pozsarzs/zacchaeus/Zacchaeus computer/hardware/PBKP Back panel/README.md

# Zacchaeus Microcomputer

## Hardware/PBKP Back panel

### Directory content

|file |description |
|---|---|
|\[pbkp\]|KiCAD files |
|pbkp.pdf|schematic drawing|

### About module

This wiring diagram contains the connections of the fixed and removable
backplane connectors. It is occasionally updated due to newly connected
ones.

The connection of serial ports and modules may vary depending on the
application (for example: tape interface).
