pozsarzs/zacchaeus/Zacchaeus computer/hardware/PFRP Front panel/README.md

# Zacchaeus Microcomputer

## Hardware/PFRP Front panel

### Directory content

|file |description |
|---|---|
|\[pfrp\]|KiCAD files |
|pfrp.pdf|schematic drawing|

### About module

This wiring diagram contains the connections of the manuals and connectors
on front panel. The light from the LEDs mounted on the PCB is forwarded using
optical fibers. It is occasionally updated due to newly connected ones.
