pozsarzs/zacchaeus/Zacchaeus computer/hardware/SC702 RCBus backplane/SC702 description.pdf

S (https://smallcomputercentral.com/)mall Computer Central (https://smallcomputercentral.com/)

# SC702 – RCBus Backplane

SC702 is an RCBus modular backplane with 6 vertical bus sockets, 1 horizontal bus socket, and one horizontal bus plug.

A 12-slot version of this backplane is also available: SC710 (https://smallcomputercentral.com/sc710-rcbus-backplane/) (https://smallcomputercentral.com/sc710-rcbus-backplane/)

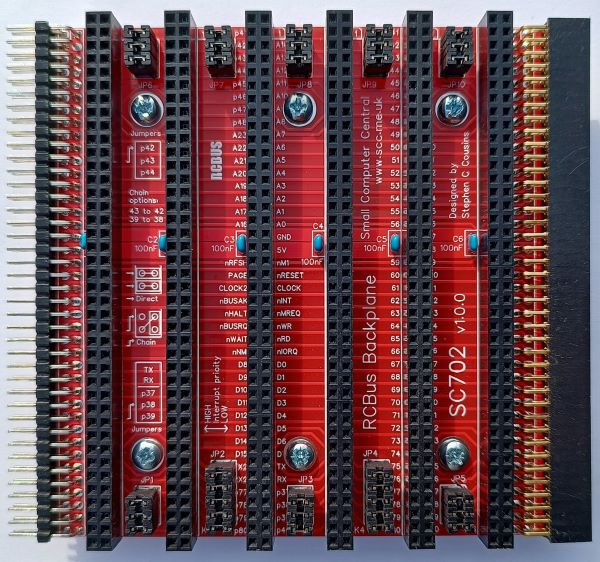
[picture p23: figure]

SC702 – Assembly guide
SC702 – Compatibility
SC702 – Parts list
SC702 – Printed circuit board SC702 – User guide

SC700 series information (https://smallcomputercentral.com/rcbus/sc700-series/) SC700 series support (https://smallcomputercentral.com/support/)

## Downloads

S (https://smallcomputercentral.com/wp-content/uploads/2024/01/sc702-kit-contents_v1.0.2_2024-01-13.pdf)C702, v1.0, Kit contents sheet (PDF) (https://smallcomputercentral.com/wp-content/uploads/2024/01/sc702-kit-contents_v1.0.2_2024-01-13.pdf) (https://smallcomputercentral.com/wpcontent/uploads/2024/01/sc702-kit-contents_v1.0.2_2024-01-13.pdf) (https://smallcomputercentral.com/wp-content/uploads/2024/01/sc702-kit-contents_v1.0.2_2024-01-13.pdf)
S (https://smallcomputercentral.com/wp-content/uploads/2023/04/sc702_v1.0.0_2023-03-21_00-14_schematic.pdf)C702, v1.0, Schematic (PDF) (https://smallcomputercentral.com/wp-content/uploads/2023/04/sc702_v1.0.0_2023-03-21_00-14_schematic.pdf) (https://smallcomputercentral.com/wpcontent/uploads/2023/04/sc702_v1.0.0_2023-03-21_00-14_schematic.pdf) (https://smallcomputercentral.com/wp-content/uploads/2023/04/sc702_v1.0.0_2023-03-21_00-14_schematic.pdf)
SC702, v1.0, PCB design files (OSHWLab) (https://oshwlab.com/sccousins/sc702-v1-0-backplane-6-1-for-rcbus) (https://oshwlab.com/sccousins/sc702-v1-0-backplane-6-1-for-rcbus)
SC702, v1.0, Gerber files (ZIP) (https://drive.google.com/file/d/1lC7prZ-vx8-ulZYEI05hR-YFU-A_hAfT/view?usp=share_link) (https://drive.google.com/file/d/1lC7prZ-vx8-ulZYEI05hR-YFU-A_hAfT/view?usp=share_link)
SC702, 3D printed mounting rails at thingiverse.com (https://www.thingiverse.com/thing:6334939/files)

## Warnings

Assembly: Ensure the bus sockets are pressed firmly against the PCB alone their entire length

## Errata

Nothing known

## Suppliers

Kits | Website | From | Currency
Small Computers Direct | SCDirect (https://small-computers-direct.square.site/s/search?q=sc702) (https://small-computers-direct.square.site/s/search?q=sc702) | UK | GBP
Stephen C Cousins | Tindie (https://www.tindie.com/search/?q=sc702) | UK | USD
Small Computer Central | Lectronz (https://lectronz.com/products/search?q=sc702) | UK | Euro/USD
PCBs | Website | From | Currency
Small Computers Direct | (https://small-computers-direct.square.site/s/search?q=sc733) (https://small-computers-direct.square.site/s/search?q=sc733)SCDirect (https://small-computers-direct.square.site/s/search?q=sc702) (https://small-computers-direct.square.site/s/search?q=sc702) (https://small-computers-direct.square.site/s/search?q=sc702) | UK | GBP
Stephen C Cousins | Tindie (https://www.tindie.com/products/tindiescx/picknmix-boards-for-rcbus-80pin/) (https://www.tindie.com/products/tindiescx/picknmix-boards-for-rcbus-80pin/) | UK | USD

Small
Computer
Central

Lectronz (https://lectronz.com/products/pick-n-mix-boards-for-rcbus-80pin) (https://lectronz.com/products/pick-n-mix-boards-for-rcbus-80pin)

UK | Euro/USD
Assembled and Tested | Website | From | Currency

Not available

Components
See parts list

Small Computers Direct does not collect VAT for EU countries Tindie does not collect VAT for EU countries Lectronz does collect EU VAT for orders up to 150 EUR

## Parts List

Reference | Qty | Component
PCB | 1 | SC702, v1.0, PCB
C1 to C6 | 6 | Capacitor, ceramic, 100 nF
JP1, 3 and 5 JP6 to JP10 | 8 | Header, male, 2 row x 3 pin, straight
JP2 and 4 | 2 | Header, male, 2 row x 5 pin, straight
Jumper | 34 | Jumper shunt
K1 to K6 | 6 | Header, female, 2 row x 40 pin, straight
P1 | 1 | Header, male, 2 row x 40 pin, angled
S1 | 1 | Header, female, 2 row x 40 pin, angled
Spacer | 6 | Spacer, 10mm, M3, nylon
Screw (for spacer) | 12 | Machine screw, 6mm, M3

Component details and sourcing (https://smallcomputercentral.com/components/)

## Printed Circuit Board

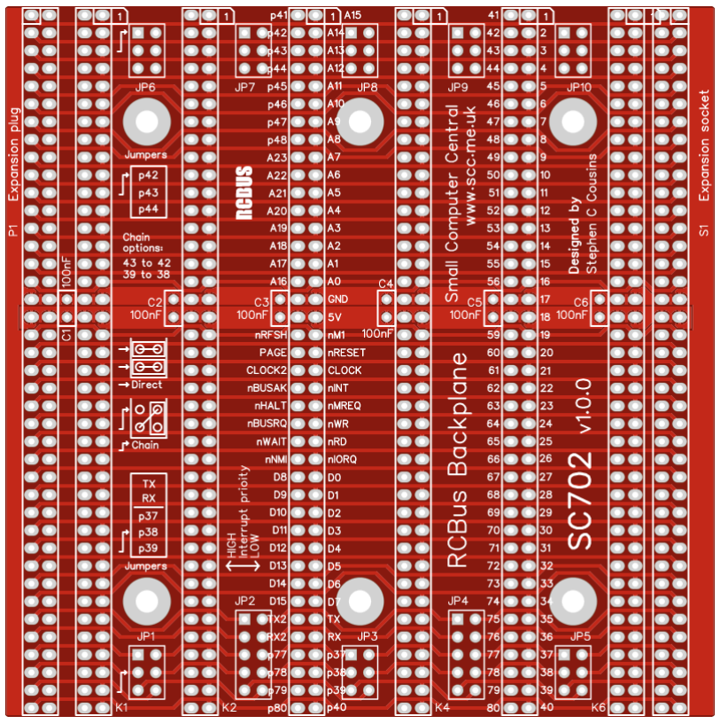
[picture p24: figure]

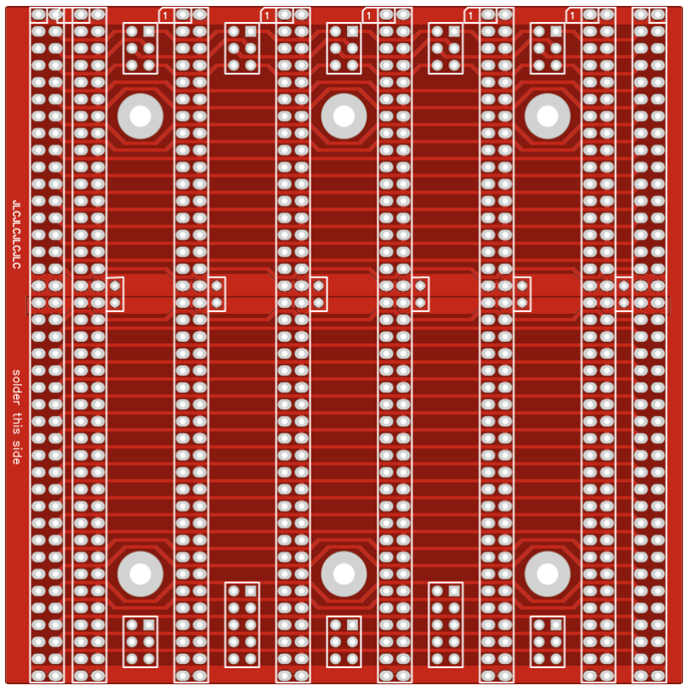
[picture p25: figure]

## User Guide

This backplane section can be used as an extension to other backplane sections or it can be used as the only backplane in the system.

Input/output port functions
I/O Address | Read | Write
none | n/a | n/a

Jumper options
Jumper Function

JP 1, 3, 5 | JPx.1 Connect P37 signal between bus sockets JPx.2 Connect P38 signal between bus sockets* JPx.3 Connect P39 signal between bus sockets* * See daisy chain details below
JP 2, 4 | JPx.1 Connect TX signal between bus sockets JPx.2 Connect RX signal between bus sockets JPx.3 Connect P37 signal between bus sockets JPx.4 Connect P38 signal between bus sockets* JPx.5 Connect P39 signal between bus sockets* * See daisy chain details below
JP6 to 10 | JPx.1 Connect P42 signal between bus sockets* JPx.2 Connect P43 signal between bus sockets* JPx.3 Connect P44 signal between bus sockets * See daisy chain details below

JP 1 to JP10 allow some signals to be isolated between bus sockets. This can be helpful if there are several mod‐ ules that use these signals for different functions.

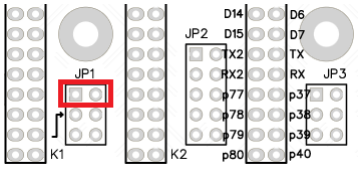
[picture p26: figure]

Typically the signals will be connected straight through to each bus socket by fitting jumper shunts horizontally, as illustrated to the left.

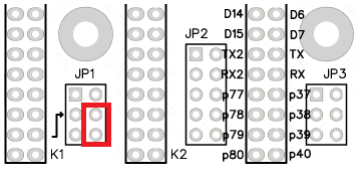
[picture p27: figure]

Alternatively, a daisy chain can be created from pin 39 to 38. This requires a jumper shunt to be fitted in the po‐ sition illustrated to the left. A second daisy chain can be created from pin 43 to 42.

A daisy chain is created with two pins on each module. One pin is an output signal while the other is an input signal. The jumper connects the output of one module to the input of the next. The illustration below shows the jumper positions required to create a daisy chain between four modules, in bus sockets K1 to K4.

Daisy chains are typically use to create a priority ‘chain’. In the case illustrated above the output is from pin 39 of one module and this is connected to the input pin 38 on the input of module to the right. This creates a prior‐ ity chain where the modules on the left are a higher priority than modules on the right.

Typical uses for a daisy chain are the Z80 mode 2 interrupt priority, IEI and IEO signals. This is specified as us‐ ing pins 39 and 38. The second chain, using pins 43 and 42 can be used for a DMA priority chain.

Priority chains require all bus slots in the chain to be occupied by suitable modules. A gap can be left by fitting a pair of jumper shunts horizontally to pass the input and output signals straight through to the bus socket not use the chain signals, rather than being crossed from output to input pins.

The illustration above configures the backplane for a daisy chain where bus socket K3 does not receive a crossed chain signal and thus should not contain a module which is part of the chain. Socket K3 can be empty or can contain a module which does not have connections to pins 39 or 38.

## Assembly Guide

Below is the suggested order of assembly. A general guide to assembling circuit boards can be found here (https://smallcomputercentral.com/assembly-guide/).

Decoupling capacitors C1 to C6
These can be fitted either way around
Header pins P1
Bus socket S1
Header pins JP1 to JP10
Bus sockets K1 to K6
Ensure the bus sockets are pressed firmly against the PCB along their entire length

## Compatibility

This backplane conforms fully to the RCBus specification v1.0 (https://smallcomputercentral.com/rcbus/) and thus supports: RCBus-2014, RCBus-Z80, RCBus-68xx, RCBus-9995.

The RCBus specification includes RCBus-2014 (both RC2014 standard 40-pin bus and RC2014 enhanced 60-pin bus) and also the full 80-pin RCBus. The 80-pin RCBus provides support for advanced Z80 features, such as the interrupt daisy-chain, as well as support for other processor families.

The following table indicates electrical compatibility with SC702. Check firmware and software details for any required software support.

Product (80-pin) | ? | Compatibility notes
SC126 (https://smallcomputercentral.com/sc126-z180-motherboard-rc2014/) Z180 motherboard | | Adds Z180 SBC/ motherboard
SC701 (https://smallcomputercentral.com/sc701-rcbus-backplane/) Backplane 6+1 | | Adds 6 module sockets RCBus 80-pin and PSU
SC702 (https://smallcomputercentral.com/sc702-rcbus-backplane/) Backplane 6+1 | | Adds 6 module sockets RCBus 80-pin
SC703 (https://smallcomputercentral.com/sc703-rcbus-power-supply-mod‐ule/) (https://smallcomputercentral.com/sc703-rcbus-power-supply-module/) Power from 12v | | Adds power supply (8 to 12 volt input) and reset
SC704 (https://smallcomputercentral.com/sc704-rcbus-i2c-bus-master/) I2C bus master | | Adds I2C bus master and I2C EEPROM
SC705 (https://smallcomputercentral.com/sc705-rcbus-serial-acia/) Serial ACIA | | Adds one serial port Typically set to 0x40
SC706 (https://smallcomputercentral.com/sc706-rcbus-z80-cpu-module/) Z80 CPU | | Adds Z80 CPU and main bus clock
SC707 (https://smallcomputercentral.com/sc707-rcbus-memory-module/) Memory 128k | | Adds 128k RAM and 128k flash ROM
SC708 (https://smallcomputercentral.com/sc708-rcbus-z80-sbc-module/) Z80 SBC | | Adds CPU, ROM, RAM clock and reset
SC709 (https://smallcomputercentral.com/sc709-rcbus-backplane/) Backplane 12+1 | | Adds 12 module sock‐ ets RCBus 80-pin and PSU
SC710 (https://smallcomputercentral.com/sc710-rcbus-backplane/) Backplane 12+1 | | Adds 12 module sock‐ ets RCBus 80-pin
SC711 (https://smallcomputercentral.com/sc711-rcbus-prototyping-module/) Prototyping | | Prototyping module
SC712 (https://smallcomputercentral.com/sc712-rcbus-power-supply-mod‐ule/) (https://smallcomputercentral.com/sc712-rcbus-power-supply-module/) Power from 5v | | Adds power supply (5 volt input) and reset
SC713 (https://smallcomputercentral.com/sc713-rcbus-tool/) RCBus tool | n/a | Simple reference tool No electrical function

SC714 (https://smallcomputercentral.com/sc714-rcbus-z80-memory-mod‐ule/) (https://smallcomputercentral.com/sc714-rcbus-z80-memory-module/) Memory 512k | Adds 512k RAM and 512k flash ROM
SC715 (https://smallcomputercentral.com/sc715-rcbus-compact-flash-mod‐ule/) (https://smallcomputercentral.com/sc715-rcbus-compact-flash-module/) Compact flash | Adds Compact Flash storage
SC716 (https://smallcomputercentral.com/sc716-rcbus-z80-sio-2-serial-mod‐ule/) (https://smallcomputercentral.com/sc716-rcbus-z80-sio-2-serial-module/) Z80 SIO/2 | Adds two serial ports Typically set to 0x84
SC717 (https://smallcomputercentral.com/sc717-rcbus-z80-pio-module/) Z80 PIO | Adds parallel I/O using Z80 PIO
SC718 (https://smallcomputercentral.com/sc718-rcbus-z80-ctc-module/) Z80 CTC | Adds counter/timer using Z80 CTC
SC719 (https://smallcomputercentral.com/sc719-rcbus-digital-i-o-module/) Digital I/O | Adds digital I/O Eight in, eight out
SC720 (https://smallcomputercentral.com/sc781-rcbus-z80-sbc-mother‐board/) (https://smallcomputercentral.com/sc781-rcbus-z80-sbc-motherboard/) Z80 motherboard | Adds Z80 SBC/ motherboard
SC721 (https://smallcomputercentral.com/sc721-rcbus-memory-module/) Memory 512k | Adds 512k RAM and 2 x 512k flash ROM
SC722 (https://smallcomputercentral.com/sc722-rcbus-z180-cpu-module/) Z180 CPU | Adds Z180 CPU with two serial ports
SC723 (https://smallcomputercentral.com/sc723-rcbus-backplane-3/) Backplane 3 | No male header pins for expansion
SC724 (https://smallcomputercentral.com/sc724-rcbus-breakout-module/) Breakout | Prototyping breakout module
SC725 (https://smallcomputercentral.com/sc725-rcbus-serial-and-timer-module/) (https://smallcomputercentral.com/sc725-rcbus-serial-and-timer-module/) SIO+CTC | Adds two serial ports and 4 counter/timers
SC726 (https://smallcomputercentral.com/sc726-rcbus-clock-module/) Clock generator | Generates CLK and CLK2 bus signals
SC727 (https://smallcomputercentral.com/sc727-rcbus-rtc-module/) Real time clock | Adds real time clock for time and date
SC728 (https://smallcomputercentral.com/sc727-rcbus-module-riser/) Module riser | Simple module riser for RCBus 80-pin
SC791 (https://smallcomputercentral.com/sc791-rcbus-z80-romwbw-com‐puter/) (https://smallcomputercentral.com/sc791-rcbus-z80-romwbw-computer/) Z80 system | Modular Z80 system
SC792 (https://smallcomputercentral.com/sc792-modular-z180-computer/) Z180 system | Modular Z180 system
Product (40 pin) | ? | Compatibility notes

SC114 (https://smallcomputercentral.com/2019/02/27/sc114-motherboard-kit/) (https://smallcomputercentral.com/2019/02/27/sc114-motherboard-kit/) Z80 motherboard | Z80 SBC/motherboard
SC130 (https://smallcomputercentral.com/sc130-z180-motherboard/) Z180 motherboard | Z180 SBC/motherboard
SC133 (https://smallcomputercentral.com/sc133-modular-backplane-rc2014/) (https://smallcomputercentral.com/sc133-modular-backplane-rc2014/) Backplane 11+1 | Adds 11 module sock‐ ets RCBus 40-pin and PSU
SC134 (https://smallcomputercentral.com/sc134-led-output-module-rc2014/) LED output port | Adds eight LED outputs
SC135 (https://smallcomputercentral.com/sc135-digital-output-module-rc2014/) (https://smallcomputercentral.com/sc135-digital-output-module-rc2014/) Digital output port | Adds eight digital outputs
SC136 (https://smallcomputercentral.com/sc136-digital-input-module-rc2014/) (https://smallcomputercentral.com/sc136-digital-input-module-rc2014/) Digital input port | Adds eight digital inputs
SC137 (https://smallcomputercentral.com/sc137-i2c-master-module-rc2014/) I2C bus master | Adds I2C bus master
SC139 (https://smallcomputercentral.com/sc139-serial-68b50-module-rc2014/) (https://smallcomputercentral.com/sc139-serial-68b50-module-rc2014/) Serial ACIA | Adds one serial port Typically set to 0x40
SC141 (https://smallcomputercentral.com/sc141-modular-backplane-rc2014/) (https://smallcomputercentral.com/sc141-modular-backplane-rc2014/) Backplane 12+1 | Adds 12 module sock‐ ets RCBus 40-pin
SC142 (https://smallcomputercentral.com/sc142-power-module-rc2014/) Power from 12v | Adds power supply (8 to 12 volt input) and reset
SC143 (https://smallcomputercentral.com/sc143-rom-module-rc2014/) Flash ROM | Adds 128k flash ROM
SC145 (https://smallcomputercentral.com/sc145-compact-flash-rc2014/) Compact flash | Adds Compact Flash storage
SC147 (https://smallcomputercentral.com/sc147-modular-backplane-rc2014/) (https://smallcomputercentral.com/sc147-modular-backplane-rc2014/) Backplane 6+1 | Adds 6 module sockets RCBus 40-pin
SC148 (https://smallcomputercentral.com/sc148-power-module-rc2014/) Power from 5v | Adds power supply (5 volt input) and reset
SC149 (https://smallcomputercentral.com/sc149-z80-cpu-module-rc2014/) Z80 CPU | Adds Z80 CPU and main bus clock
SC150 (https://smallcomputercentral.com/sc150-paged-ram-module-rc2014/) (https://smallcomputercentral.com/sc150-paged-ram-module-rc2014/) Paged RAM 128k | Adds 128k of paged RAM

SC151 (https://smallcomputercentral.com/sc151-paged-rom-modulerc2014/) (https://smallcomputercentral.com/sc151-paged-rom-module-rc2014/)
Paged ROM 128k

Adds 128k of paged
ROM
Other suppliers | ? | Compatibility notes
RC2014 Mini system | | No male header pins for expansion
RC2014 Pro system | | No male header pins for expansion
RC2014 Zed system | | No male header pins for expansion
RC2014 Micro module | | Adds CPU, ROM, RAM serial, clock and reset
RC2014 Backplane 5 | | If header pins fitted it adds 4 x 40-pin sockets
RC2014 Backplane 8 | | No male header pins for expansion
RC2014 Backplane Pro | | No male header pins for expansion
RC2014 Z80 CPU | | Adds Z80 CPU
RC2014 SIO/2 dual serial | | Adds two serial ports at 0x80 to 0x87
RC2014 Compact flash | | Adds Compact Flash at 0x10 to 0x17
RC2014 Dual clock | | Generates CLK and CLK2 bus signals
RC2014 Pageable ROM | | Adds 64k paged ROM
RC2014 64k RAM | | Adds 64k paged RAM
RC2014 Memory 512k | | Adds 512k RAM and 512k flash ROM
RC2014 Digital I/O | | Adds eight LED out‐ puts and eight push buttons
RC2014 Real time clock | | Adds real time clock for time and date
RC2014 RP2040 VGA terminal | | Connect VGA monitor and USB keyboard
RC2014 Pi Pico terminal | | Connect VGA monitor and USB keyboard

RC2014 YM2149 sound card | Adds authentic retro sound
Weird electronics Flock v2 | Adds floppy disk and real time clock

## Notes

This product is designed for hobby use and is not suitable for industrial, commercial, or safety-critical applications.
The product contains small parts and is not suitable for young children.
