pozsarzs/zacchaeus/Zacchaeus computer/hardware/SC702 RCBus backplane/SC702 kit contents.pdf

A | A
B | B

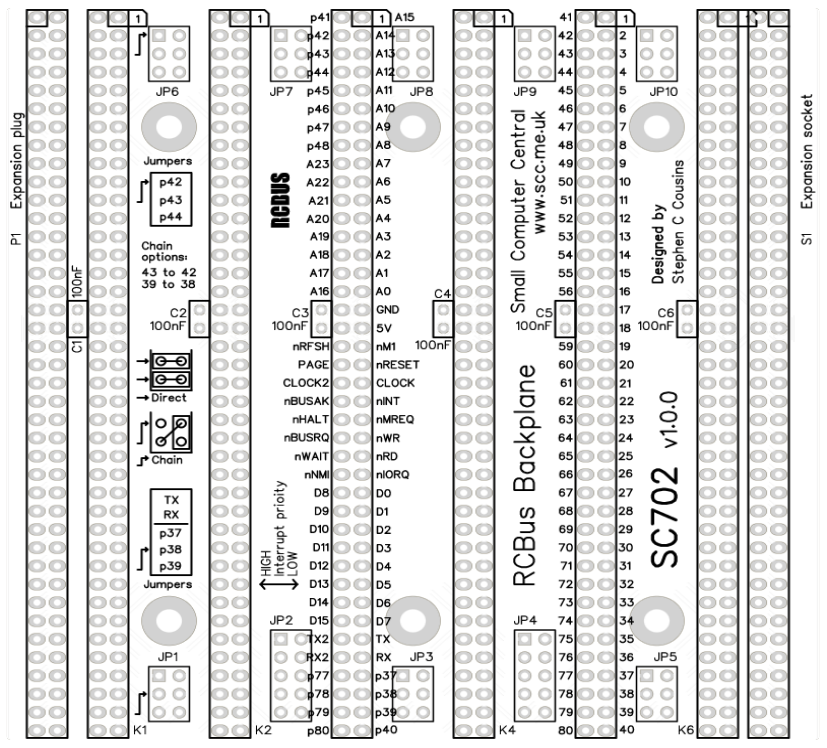
[picture p28: figure]

C | C
D | D

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
TITLE:

SC142 - Kit Contents

REV: 1.0.2

Date:

2021-01-11

Sheet: 1/1
Drawn By: sccousins

Company: www.scc.me.uk

C1 to C6
Capacitor 100 nF
6

Designed for
RCBus

# Welcome to your SC702, Backplane Kit

## Assembly instructions, user guide, and other documentation can be found at www.scc.me.uk (small computer central)

Contains small parts. Not suitable for young children. Designed for hobby use. Not suitable for commercial, industrial or safety-critical use.
1

SC702 v1.0.x
Printed circuit board

2024-01-13

SC702 - Kit Contents

Release date: 2023-04-05

6

K1 to K6 Female
2 row x 40 pin straight
1

JP1 to JP10 Header
2 row x 40 pin straight

Jumper shunt
34

See note 1

1

S1 Header socket
2 row x 40 pin angled

Spacer
Nylon, 10mm, M3
6

Screw (for spacer)
M3, 6mm, pan head
12

1

P1 Header plug
2 row x 40 pin angled

the PCB alone their entire length

(long nose wire cutters work well)

Notes:
1/ Cut into short length strips, 3 and 5 pins long, for J1 to JP10

2/ Ensure the module sockets (K1 to K6) are pressed firmly against

Label includes "104" | See note 2
