pozsarzs/zacchaeus/Zacchaeus computer/hardware/SC716 RCBus SIO-2 module/SC716 kit contents.pdf

A | A

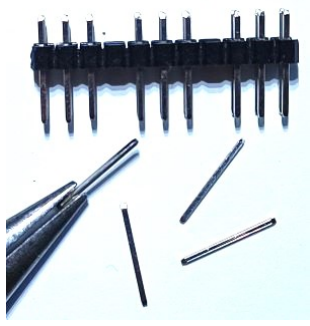
[picture p32: figure]

B | B

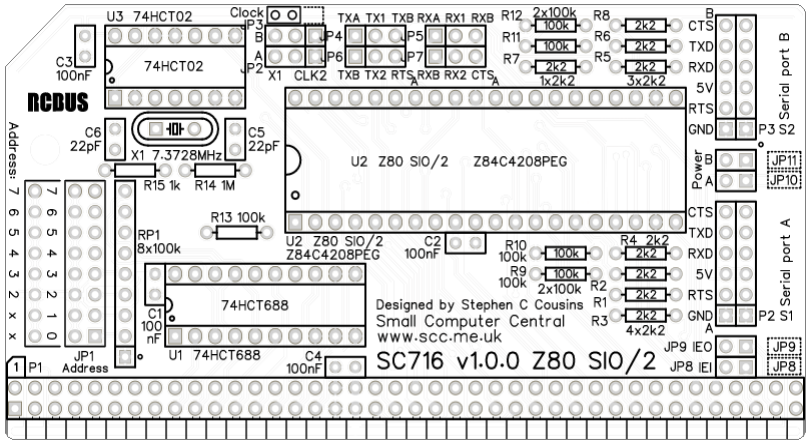
[picture p33: figure]

C | C
D | D

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
TITLE:

SC142 - Kit Contents

REV: 1.0.0

Date:

2021-01-11

Sheet: 1/1
Drawn By: sccousins

Company: www.scc.me.uk

C1 to C4
100 nF
4

Designed for
RCBus

# Welcome to your SC716, Z80 SIO/2 Serial Module Kit

## Assembly instructions, user guide, and other documentation can be found at www.scc.me.uk (small computer central)

Contains small parts. Not suitable for young children. Designed for hobby use. Not suitable for commercial, industrial or safety-critical use.
1

SC716 v1.0.x
Printed circuit board

2023-05-14

SC716 - Kit Contents

Release date: 2023-05-14

P1 Male
2 row x 40 pin angled
1

Spacer
Nylon, 10mm, M3

Screw (for spacer)
M3, 6mm, pan head
1 1

1

U3
74HCT02

1

JP1 Male
2 row x 8 pin angled

Jumper shunts
16

1

X1
7.3728 MHz crystal

2

C5 and C6
22 pF capacitor
Label includes "22" | See note 1 JP2 to JP7 Header 2 row x 11 pin straight
1

JP8 + JP9 Male
2 row x 2 pin angled
1

JP10 + JP11 Male
2 row x 2 pin angled
1

Cut with long nose wire cutters from a strip 2 row x 12+ pins

P2 Male
1 row x 6 pin angled
1

Cut from a strip 12+ pins long

P3 Male
1 row x 6 pin angled
1

1

5 1

R9 to R13
100K
8

R1 to R8
2K2

R14
1M

R15
1K

Label includes "104"

RP1 Resistor network
8 x 100K

# 1 2 S1 and S2 Female 1 row x 6 pin angled

1

1

U1
74HCT688

U1 socket
20-pin IC socket DIL
1

U1 Socket
40-pin IC socket DIL

1

U2 Z80 SIO/2
Z84C42xxPEG

U3 socket
14-pin IC socket DIL
1

Notes
1/ Removed the 4th and

connector fits in JP2

(pull out with pliers)

8th pair of pins so the

to JP7 holes

Label includes "104"
