pozsarzs/zacchaeus/Zacchaeus computer/hardware/SC717 RCBus PIO module/SC717 kit contents.pdf

A | A
B | B

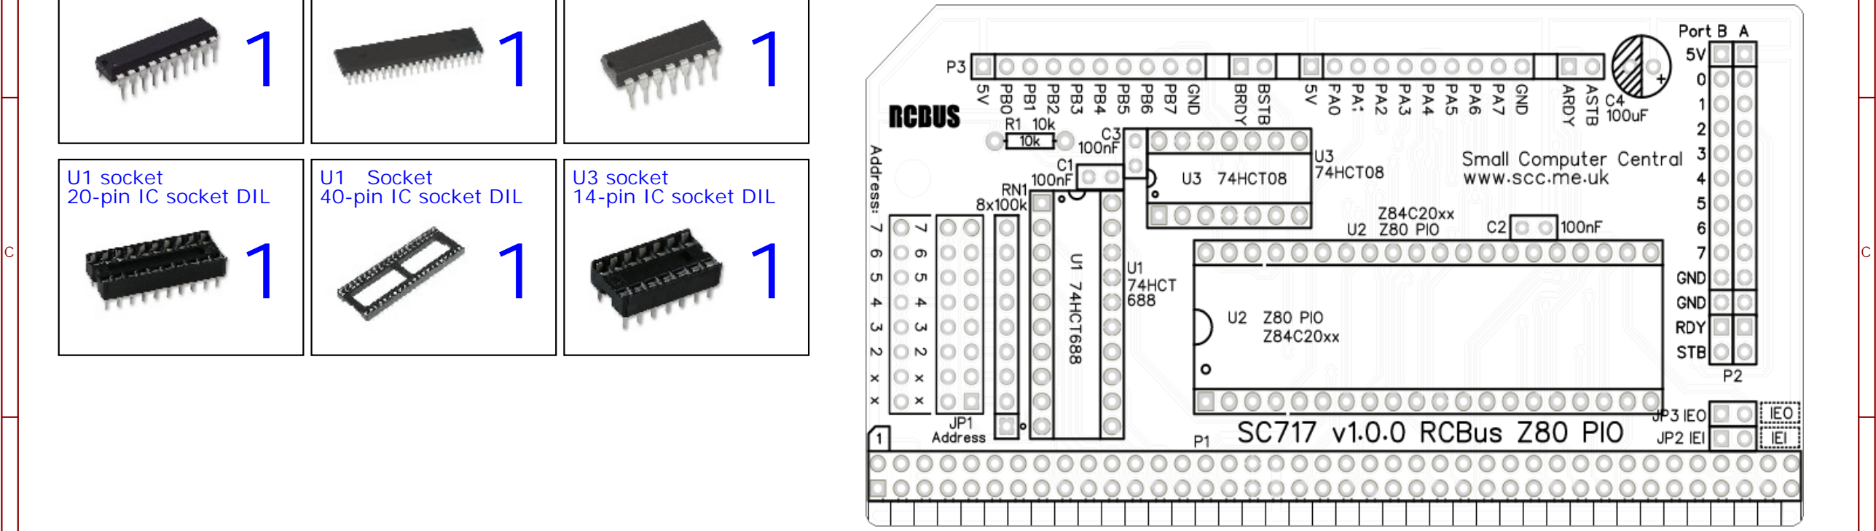
[picture p37: figure]
U1 socket 20-pin IC socket DIL; U1 Socket 40-pin IC socket DIL; U3 socket 14-pin IC socket DIL 1

D | D

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
TITLE:

SC142 - Kit Contents

REV: 1.0.0

Date:

2021-01-11

Sheet: 1/1
Drawn By: sccousins

Company: www.scc.me.uk

C1 to C3
100 nF
3

Designed for
RCBus

# Welcome to your SC717, Z80 PIO Digital Module Kit

## Assembly instructions, user guide, and other documentation can be found at www.scc.me.uk (small computer central)

Contains small parts. Not suitable for young children. Designed for hobby use. Not suitable for commercial, industrial or safety-critical use.
1

SC717 v1.0.x
Printed circuit board

2023-05-17

SC717 - Kit Contents

Release date: 2023-05-17

P1 Male
2 row x 40 pin angled
1

Spacer
Nylon, 10mm, M3

Screw (for spacer)
M3, 6mm, pan head
1 1

U3
74HCT08

1

JP1 Male
2 row x 8 pin angled

Jumper shunts
8

JP2 + JP3 Male
2 row x 2 pin angled
1

Cut from a strip 2 row x 10+ pins

P3 Male
1 row x 27 pin angled
1

Label includes "104"

RN1 Resistor network
8 x 100K
1

U1
74HCT688

U2 Z80 PIO
Z84C20xxPEG

Label includes "104"

1

C4
100 F

1

P2 Box header
2 row x 13 pin angled
1

R1
10k
