pozsarzs/zacchaeus/Zacchaeus computer/hardware/SC718 RCBus CTC module/SC718 kit contents.pdf

A | A
B | B

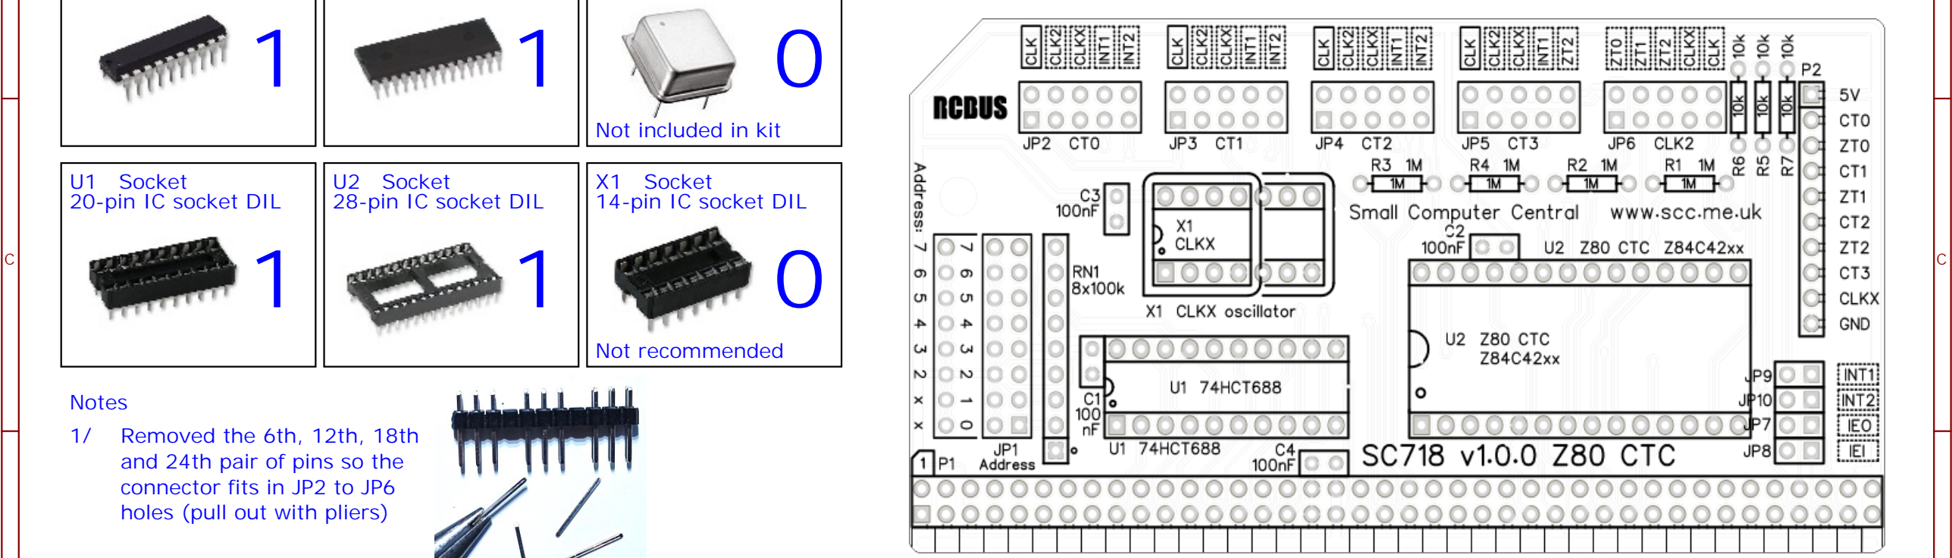
[picture p41: figure]
U1 Socket 20-pin IC socket DIL; U2 Socket 28-pin IC socket DIL; X1 Socket 14-pin IC socket DIL 0; Not included in kit; Not recommended; Notes 1/; holes (pull out with pliers); and 24th pair of pins so the connector fits in JP2 to JP6; Removed the 6th, 12th, 18th
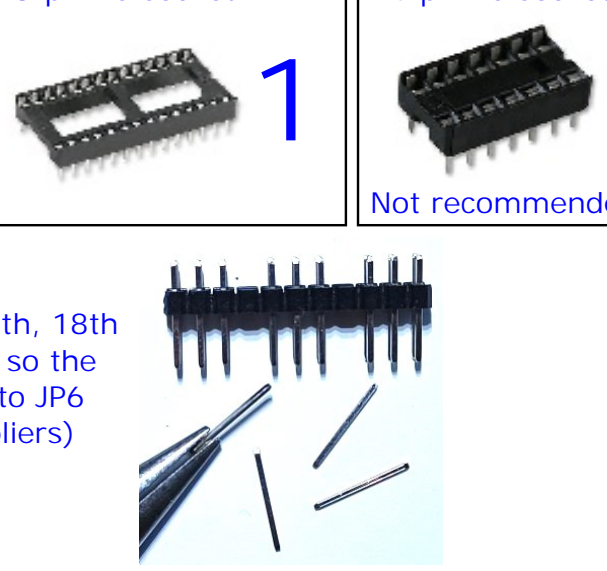
[picture p42: figure]

D | D

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
TITLE:

SC142 - Kit Contents

REV: 1.0.0

Date:

2021-01-11

Sheet: 1/1
Drawn By: sccousins

Company: www.scc.me.uk

C1 to C4
100 nF
4

Designed for
RCBus

# Welcome to your SC718, Z80 CTC Timer Module Kit

## Assembly instructions, user guide, and other documentation can be found at www.scc.me.uk (small computer central)

Contains small parts. Not suitable for young children. Designed for hobby use. Not suitable for commercial, industrial or safety-critical use.
1

SC718 v1.0.x
Printed circuit board

2023-05-21

SC718 - Kit Contents

Release date: 2023-05-21

P1 Male
2 row x 40 pin angled
1

Spacer
Nylon, 10mm, M3

Screw (for spacer)
M3, 6mm, pan head
1 1

1

JP1 Male
2 row x 8 pin angled

Jumper shunts
15

JP7+8+9+10 Male
2 row x 4 pin angled
1

Cut from a strip 2 row x 12+ pins

P2 Male
1 row x 10 pin angled
1

Label includes "104"

RN1 Resistor network
8 x 100K
1

U1
74HCT688

U2 Z80 CTC
Z84C30xxPEG

Label includes "104"
3

R5 to R7
10k

1

JP2 to JP6 Header
2 row x 29 pin straight

See note 1

R1 to R4
1M
4

X1 (optional)
7.3728MHz oscillator

Errata: PCB v1.0.0 has the wrong component label for U2
