pozsarzs/zacchaeus/Zacchaeus computer/hardware/SC719 RCBus DIO module/SC719 kit contents.pdf

A | A
B | B

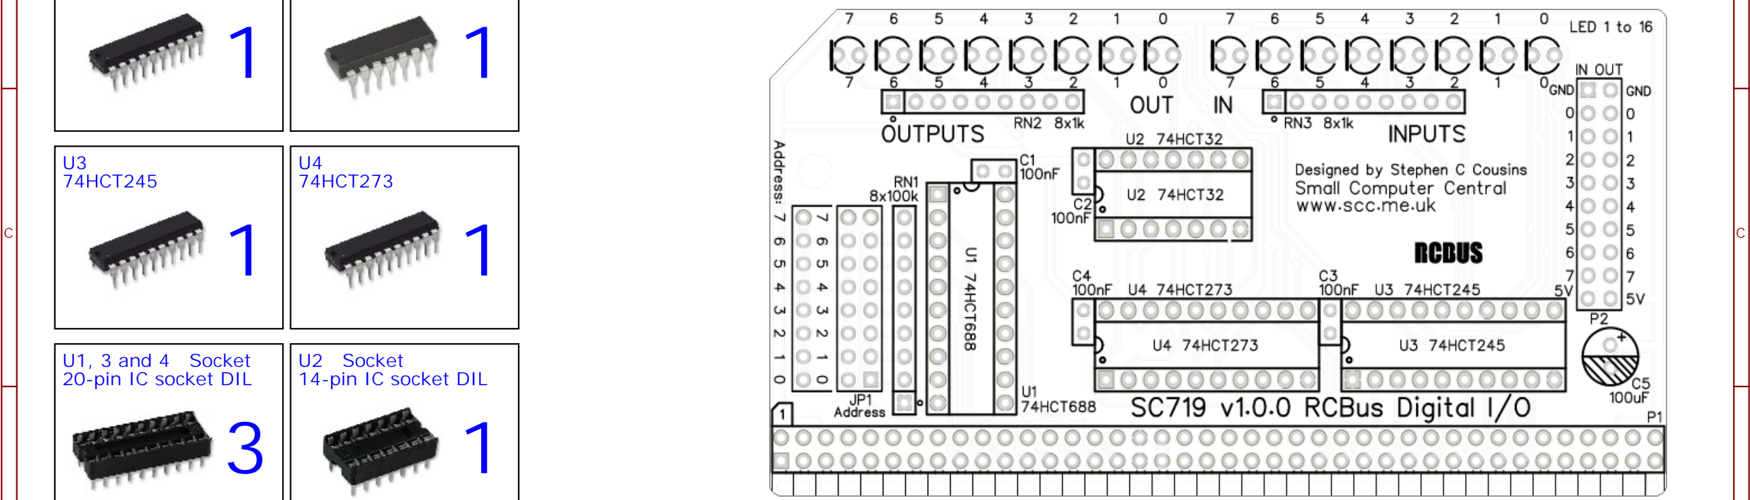
[picture p46: figure]
U1, 3 and 4 Socket 20-pin IC socket DIL; U2 Socket 14-pin IC socket DIL; U3 74HCT245; U4 74HCT273

D | D

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
TITLE:

SC142 - Kit Contents

REV: 1.0.1

Date:

2021-01-11

Sheet: 1/1
Drawn By: sccousins

Company: www.scc.me.uk

C1 to C4
100 nF
4

Designed for
RCBus

# Welcome to your SC719, Digital I/O Module Kit

## Assembly instructions, user guide, and other documentation can be found at www.scc.me.uk (small computer central)

Contains small parts. Not suitable for young children. Designed for hobby use. Not suitable for commercial, industrial or safety-critical use.
1

SC719 v1.0.x
Printed circuit board

2023-08-28

SC719 - Kit Contents

Release date: 2023-05-21

P1 Male
2 row x 40 pin angled
1

Spacer
Nylon, 10mm, M3

Screw (for spacer)
M3, 6mm, pan head
1 1

1

JP1 Male
2 row x 8 pin angled

Jumper shunts
8

Label includes "102"

RN2 and 3 Resistor
network 8 x 1K
2

U1
74HCT688

Label includes "104"

C5
100 F
1 | 8

LED9 to LED16
| Red LED 3mm angled

LED1 to LED8
Green LED 3mm angled
8

P2 Box header
2 row x 10 pin angled

# 1 1 RN1 Resistor network

8 x 100K

Label includes "104"

U2
74HCT32
