pozsarzs/zacchaeus/Zacchaeus computer/hardware/Front panel/README.md

# Zacchaeus Microcomputer

## Hardware/Front panel

### Directory content

|file |description |
|---|---|
|z180cpu.cdr |label 'Z180 CPU' |
|zacchaeus.cdr |label 'ZACCHAEUS' |
|zacchaeus_z180.dxf  |front panel design in DXF|
|zacchaeus_z180.jpg  |front panel appearance |
|zacchaeus_z180.panel|front panel design |

This folder contains the design of the front panel of the device. The front
panel was made in excellent quality by the Slovak company
[Quickpanel](https://quickpanel.sk). The design was made with their own
downloadable [design program](https://quickpanel.sk/en/download-quickpanel-program-software).
