pozsarzs/zacchaeus/PEIX External interface box/hardware/aim62-1/aim62-1.jpg

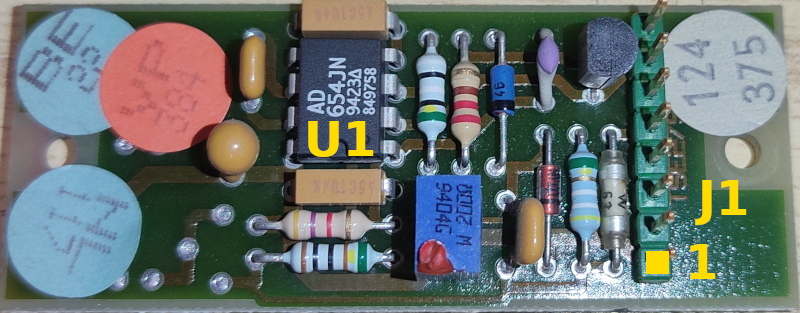
PEIX External interface box/hardware/aim62-1/aim62-1.jpg
