pozsarzs/zacchaeus/PEMX External memory box/hardware/block diagram/blk_pemx.png

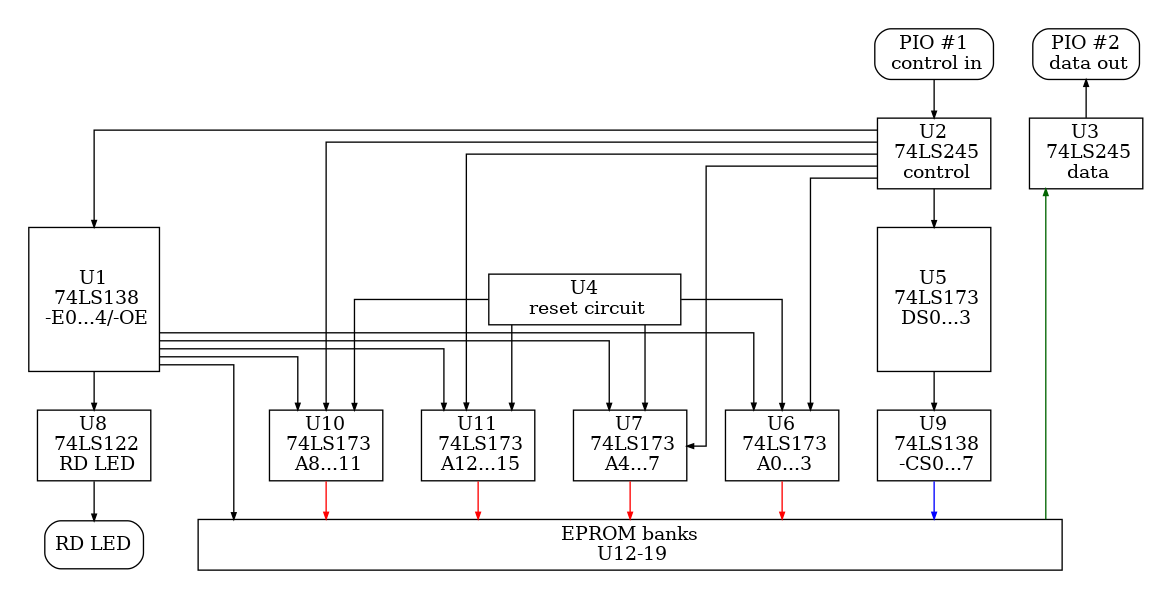
PEMX External memory box/hardware/block diagram/blk_pemx.png
