pozsarzs/zacchaeus/pictures/screenshot/scr_01.png

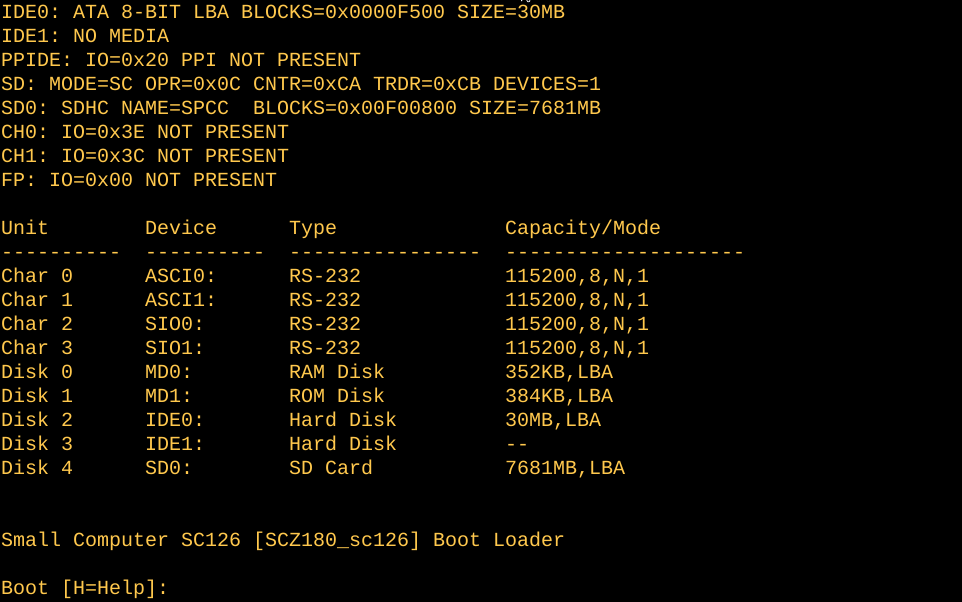
pictures/screenshot/scr_01.png
