pozsarzs/zacchaeus/pictures/screenshot/scr_02.png

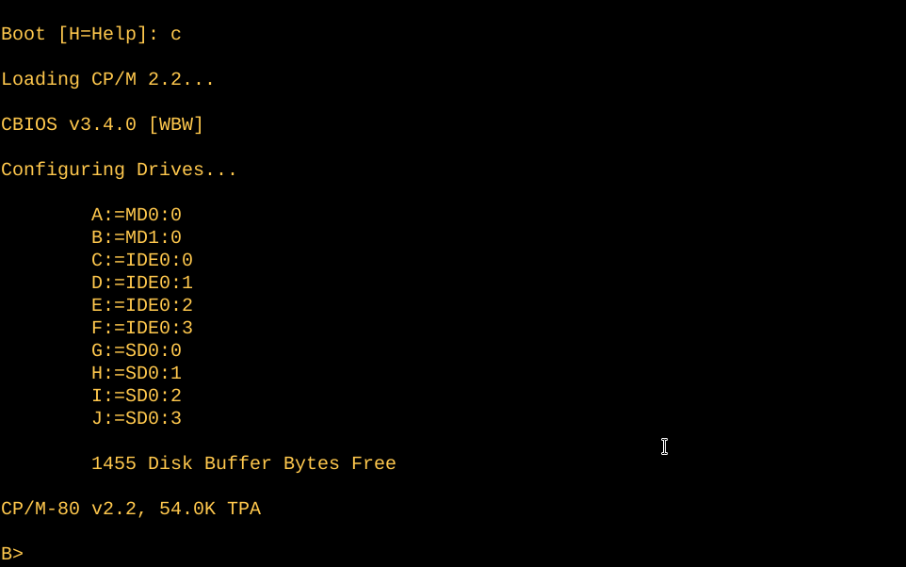
pictures/screenshot/scr_02.png
