pozsarzs/zacchaeus/pictures/screenshot/scr_03.png

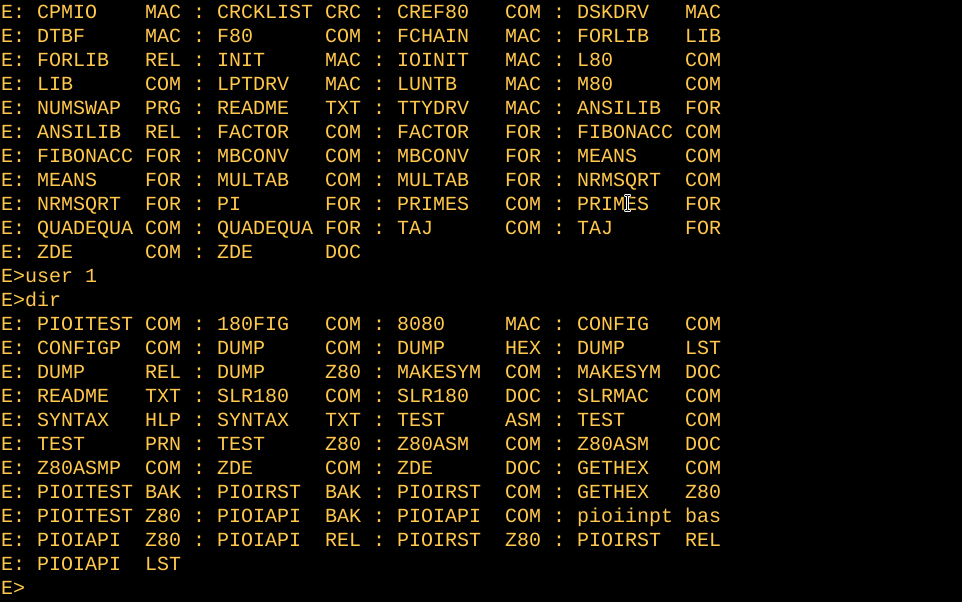
pictures/screenshot/scr_03.png
