pozsarzs/zacchaeus/pictures/screenshot/scr_04.png

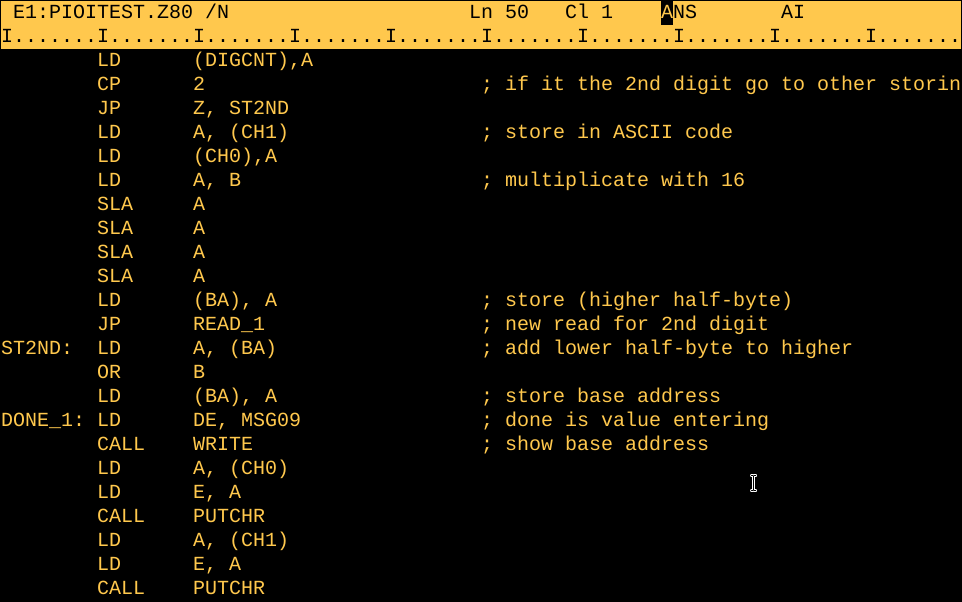
pictures/screenshot/scr_04.png
