pozsarzs/zacchaeus/pictures/screenshot/scr_05.png

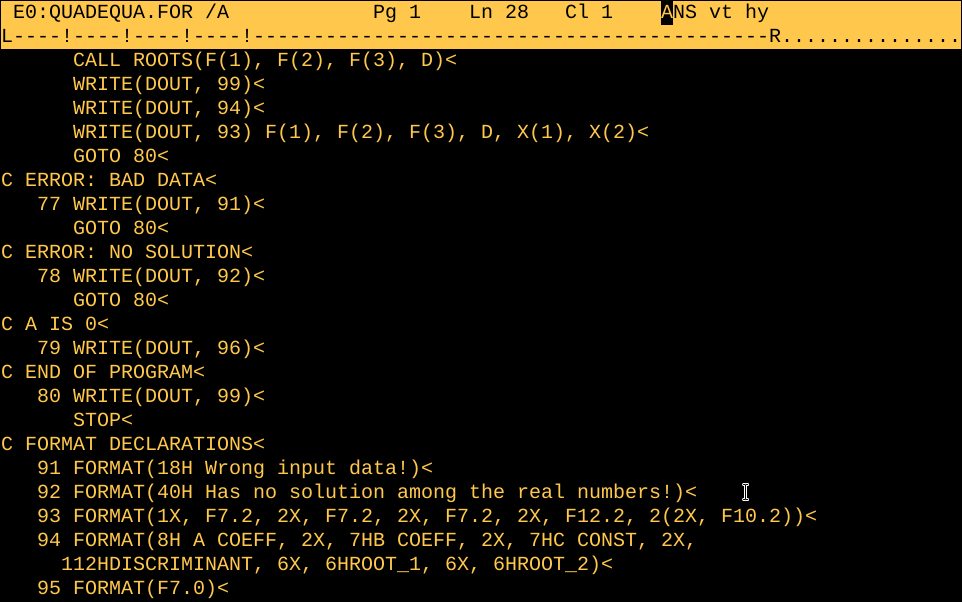
pictures/screenshot/scr_05.png
