pozsarzs/zacchaeus/pictures/Zacchaeus_01.jpg

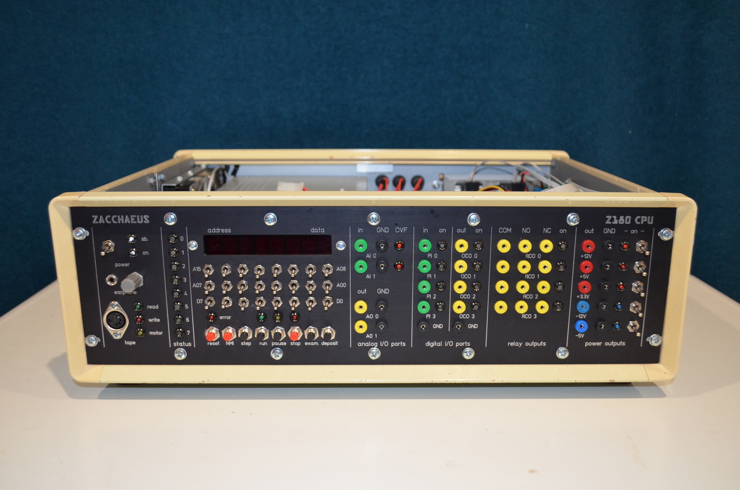
pictures/Zacchaeus_01.jpg
