pozsarzs/zacchaeus/pictures/Zacchaeus_02.jpg

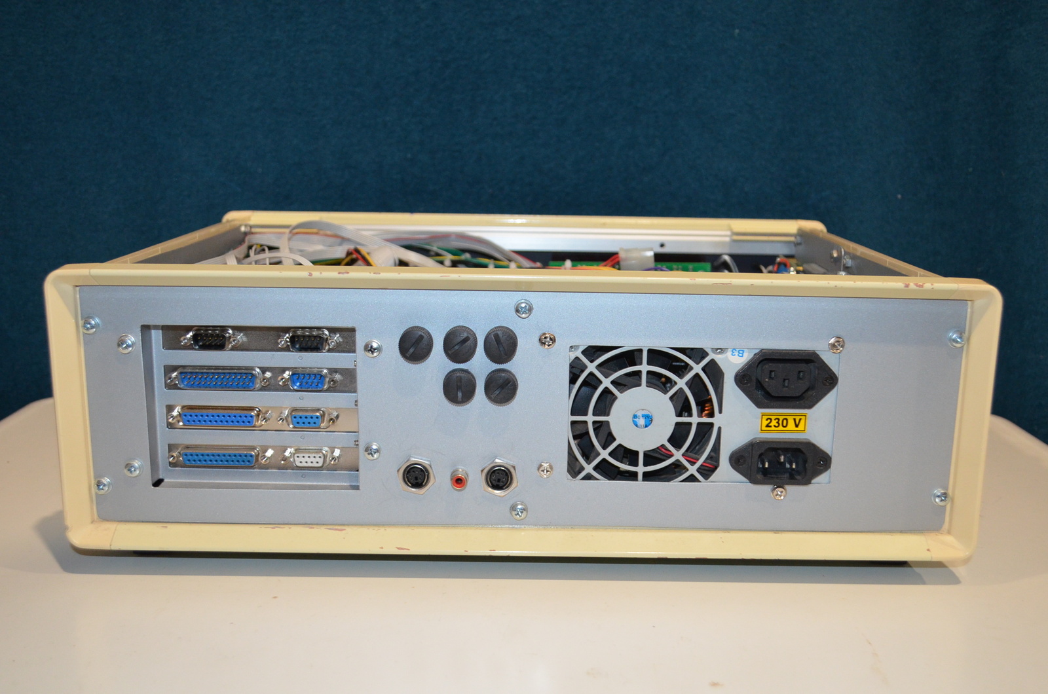
pictures/Zacchaeus_02.jpg
