pozsarzs/zacchaeus/Zacchaeus computer/hardware/Front panel/zacchaeus_z180.jpg

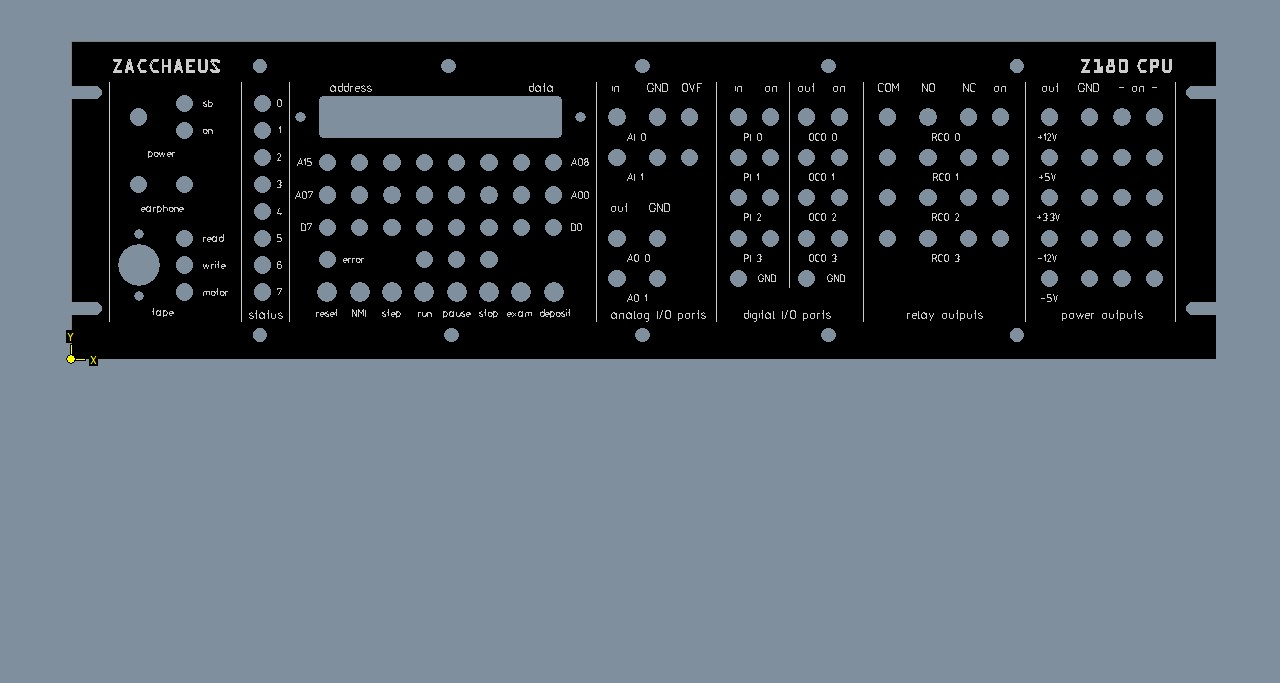
Zacchaeus computer/hardware/Front panel/zacchaeus_z180.jpg
