pozsarzs/zacchaeus/Zacchaeus computer/hardware/PMAN-IF Interface module/pman-if.jpg

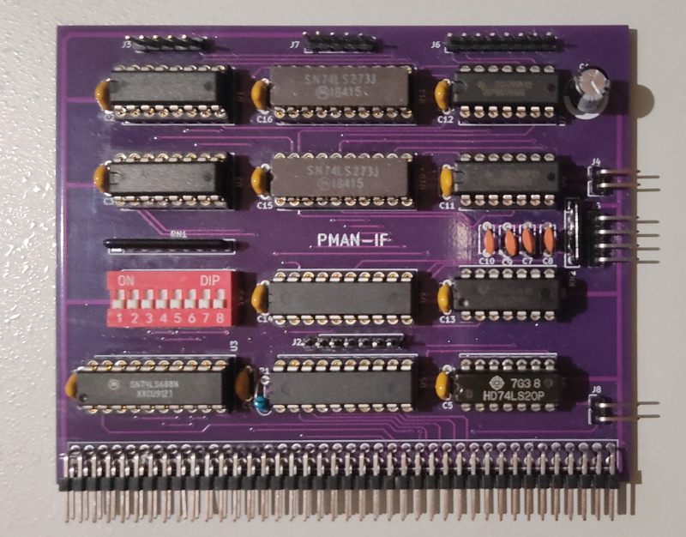
Zacchaeus computer/hardware/PMAN-IF Interface module/pman-if.jpg
