pozsarzs/zacchaeus/Zacchaeus computer/hardware/SC126 Z180 motherboard/SC126.jpg

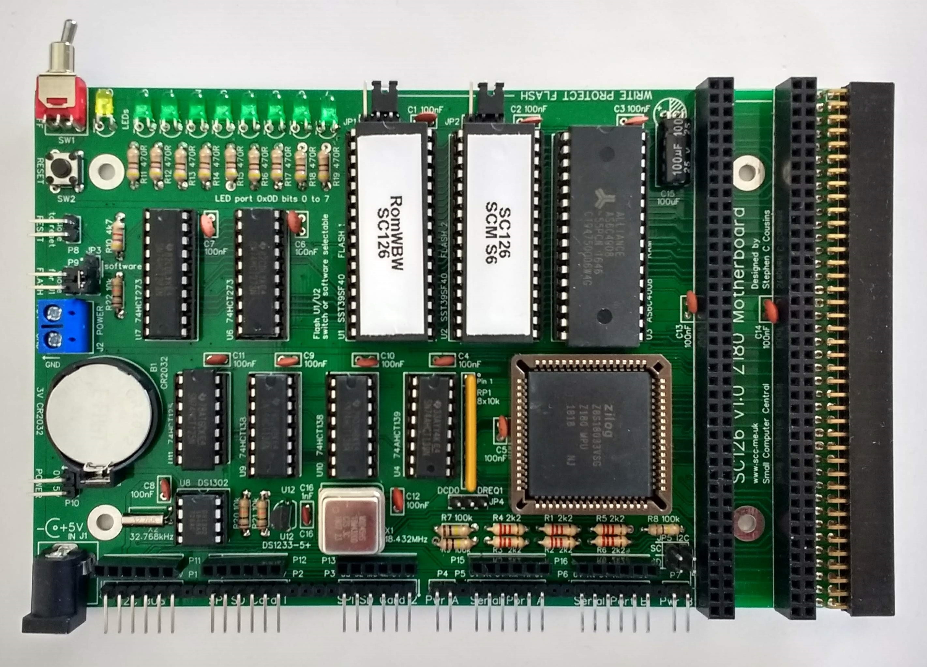
Zacchaeus computer/hardware/SC126 Z180 motherboard/SC126.jpg
