pozsarzs/zacchaeus/Zacchaeus computer/hardware/SC716 RCBus SIO-2 module/sc716.jpg

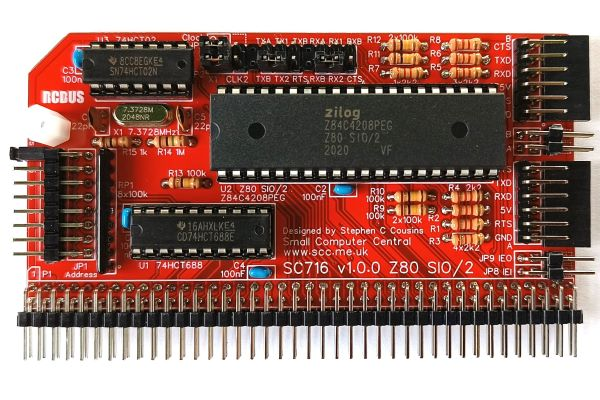
Zacchaeus computer/hardware/SC716 RCBus SIO-2 module/sc716.jpg
