pozsarzs/zacchaeus/Zacchaeus computer/hardware/MCS-51M RS232 level shifter module/MCS-51M assembled.jpg

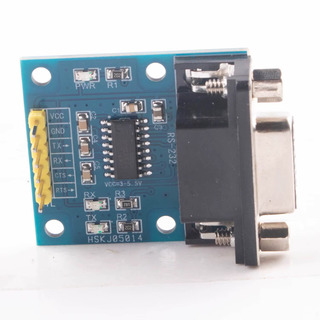
Zacchaeus computer/hardware/MCS-51M RS232 level shifter module/MCS-51M assembled.jpg
