pozsarzs/zacchaeus/Zacchaeus computer/hardware/RCBus/protocard-1.pdf

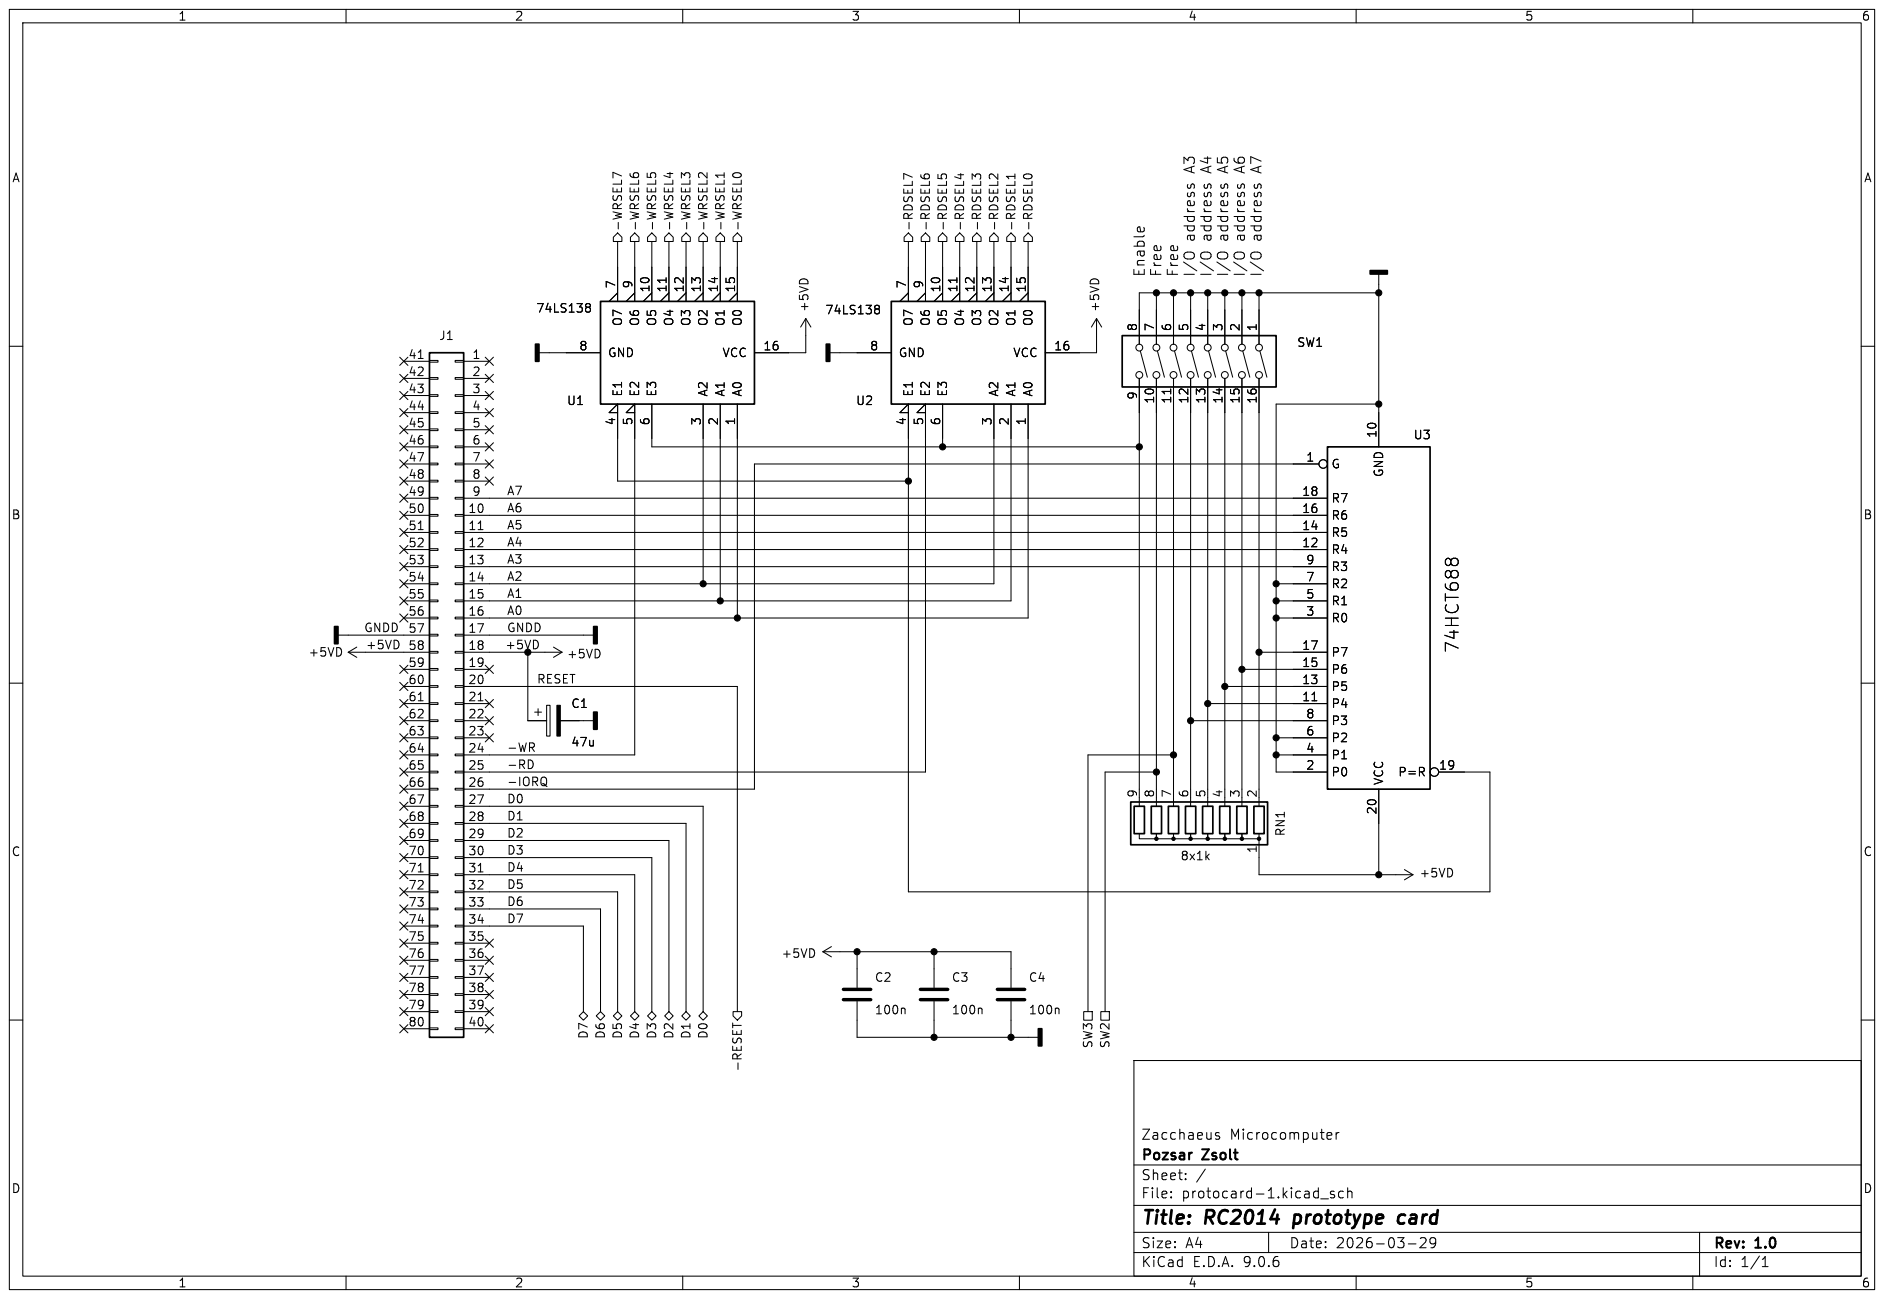
[picture p70: page 1]

Id: 1/1 Title: RC2014 prototype card
