pozsarzs/zacchaeus/Zacchaeus computer/hardware/RCBus/protocard-2.pdf

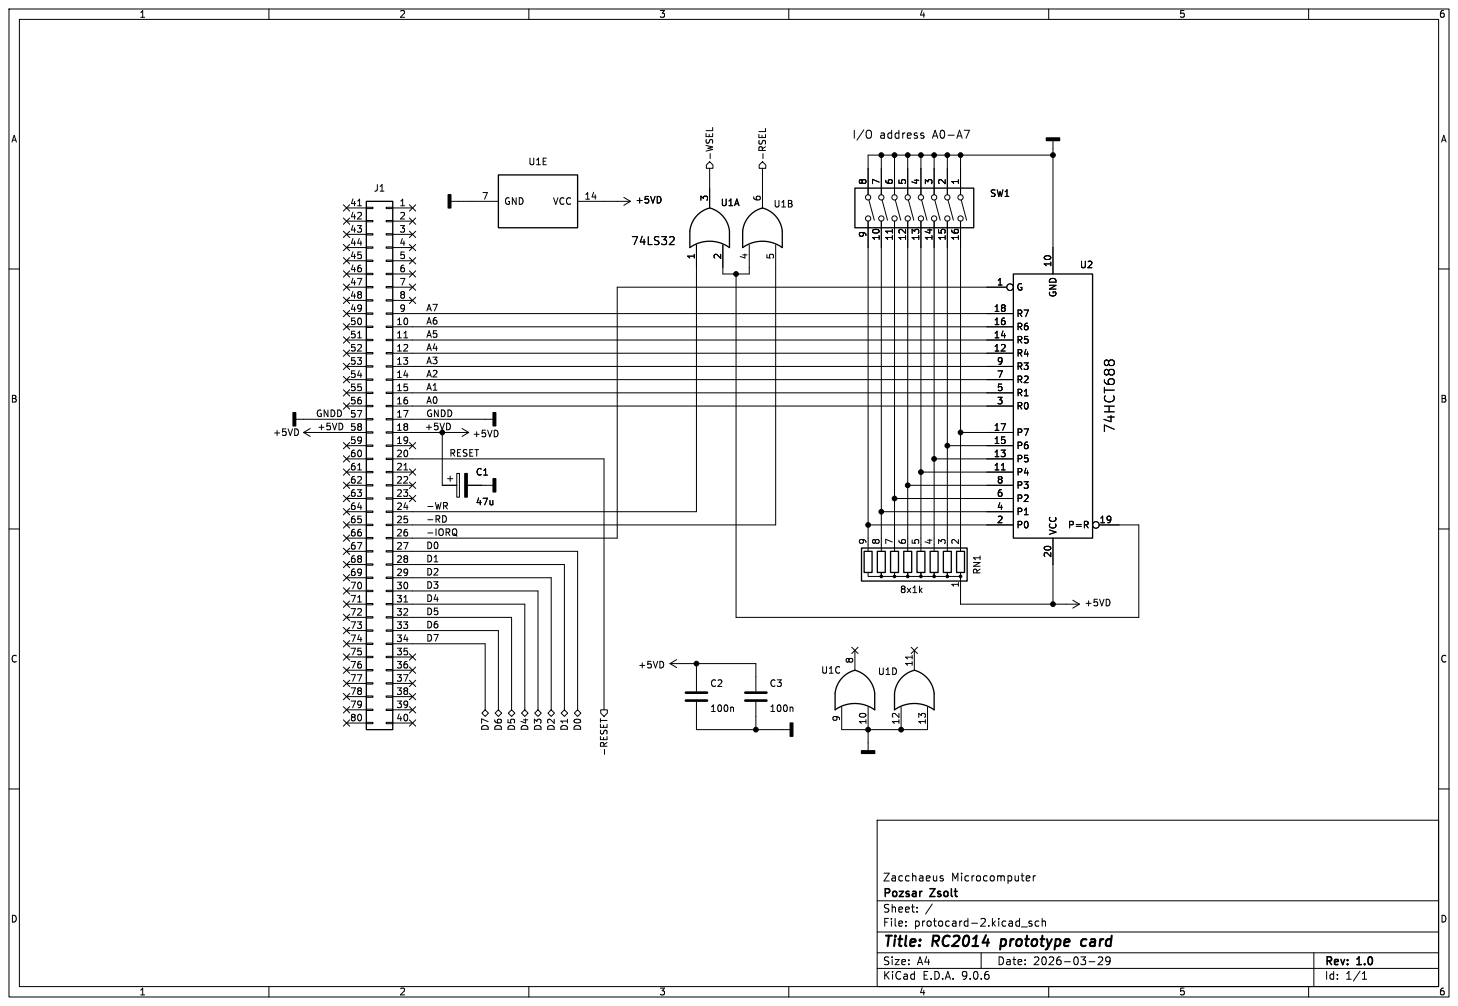
[picture p71: page 1]

Id: 1/1 Title: RC2014 prototype card
