pozsarzs/zacchaeus/PEIX External interface box/hardware/aqm61-2/aqm61-2.pdf

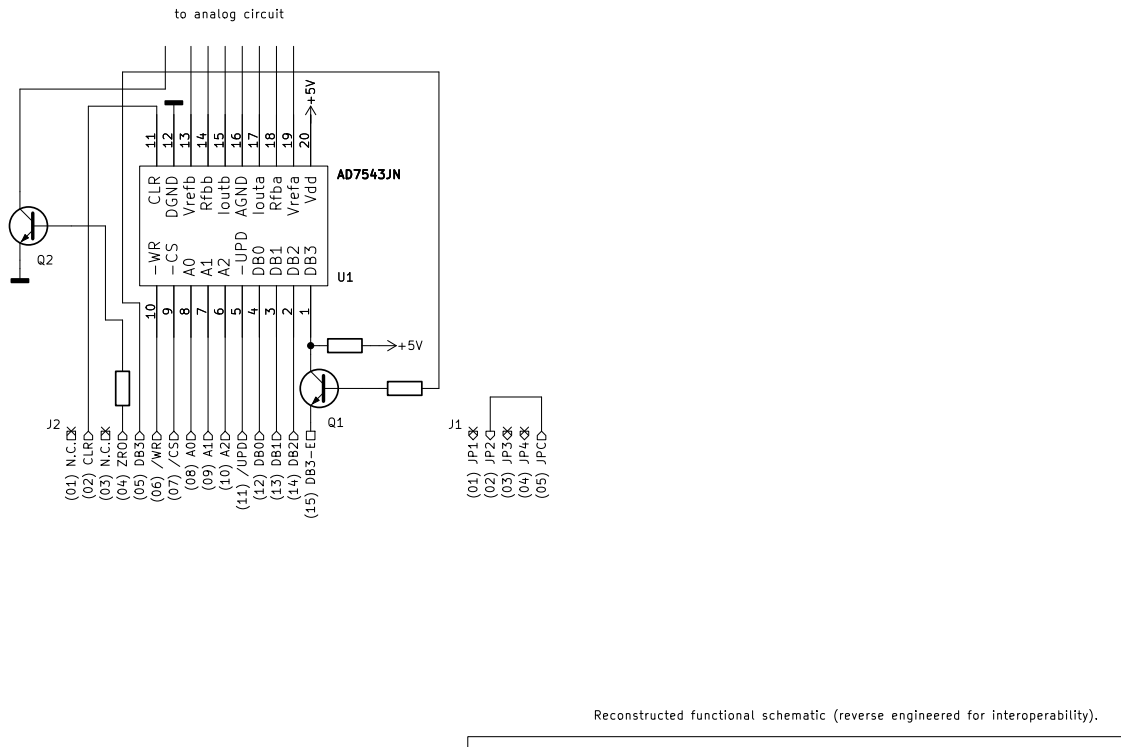
[picture p72: page 1]

3 U1 AD7543JN Q1 +5V (02) CLR (11) /UPD (01) N.C. (04) ZRO (03) N.C. (05) DB3 (13) DB1 (15) DB3-E (14) DB2 (05) JPC (01) JP1 (04) JP4 (02) JP2 (03) JP3 (09) A1 (06) /WR (07) /CS (10) A2 (08) A0 (12) DB0
