pozsarzs/zacchaeus/Zacchaeus computer/hardware/PPOW Power distribution module/ppow.pdf

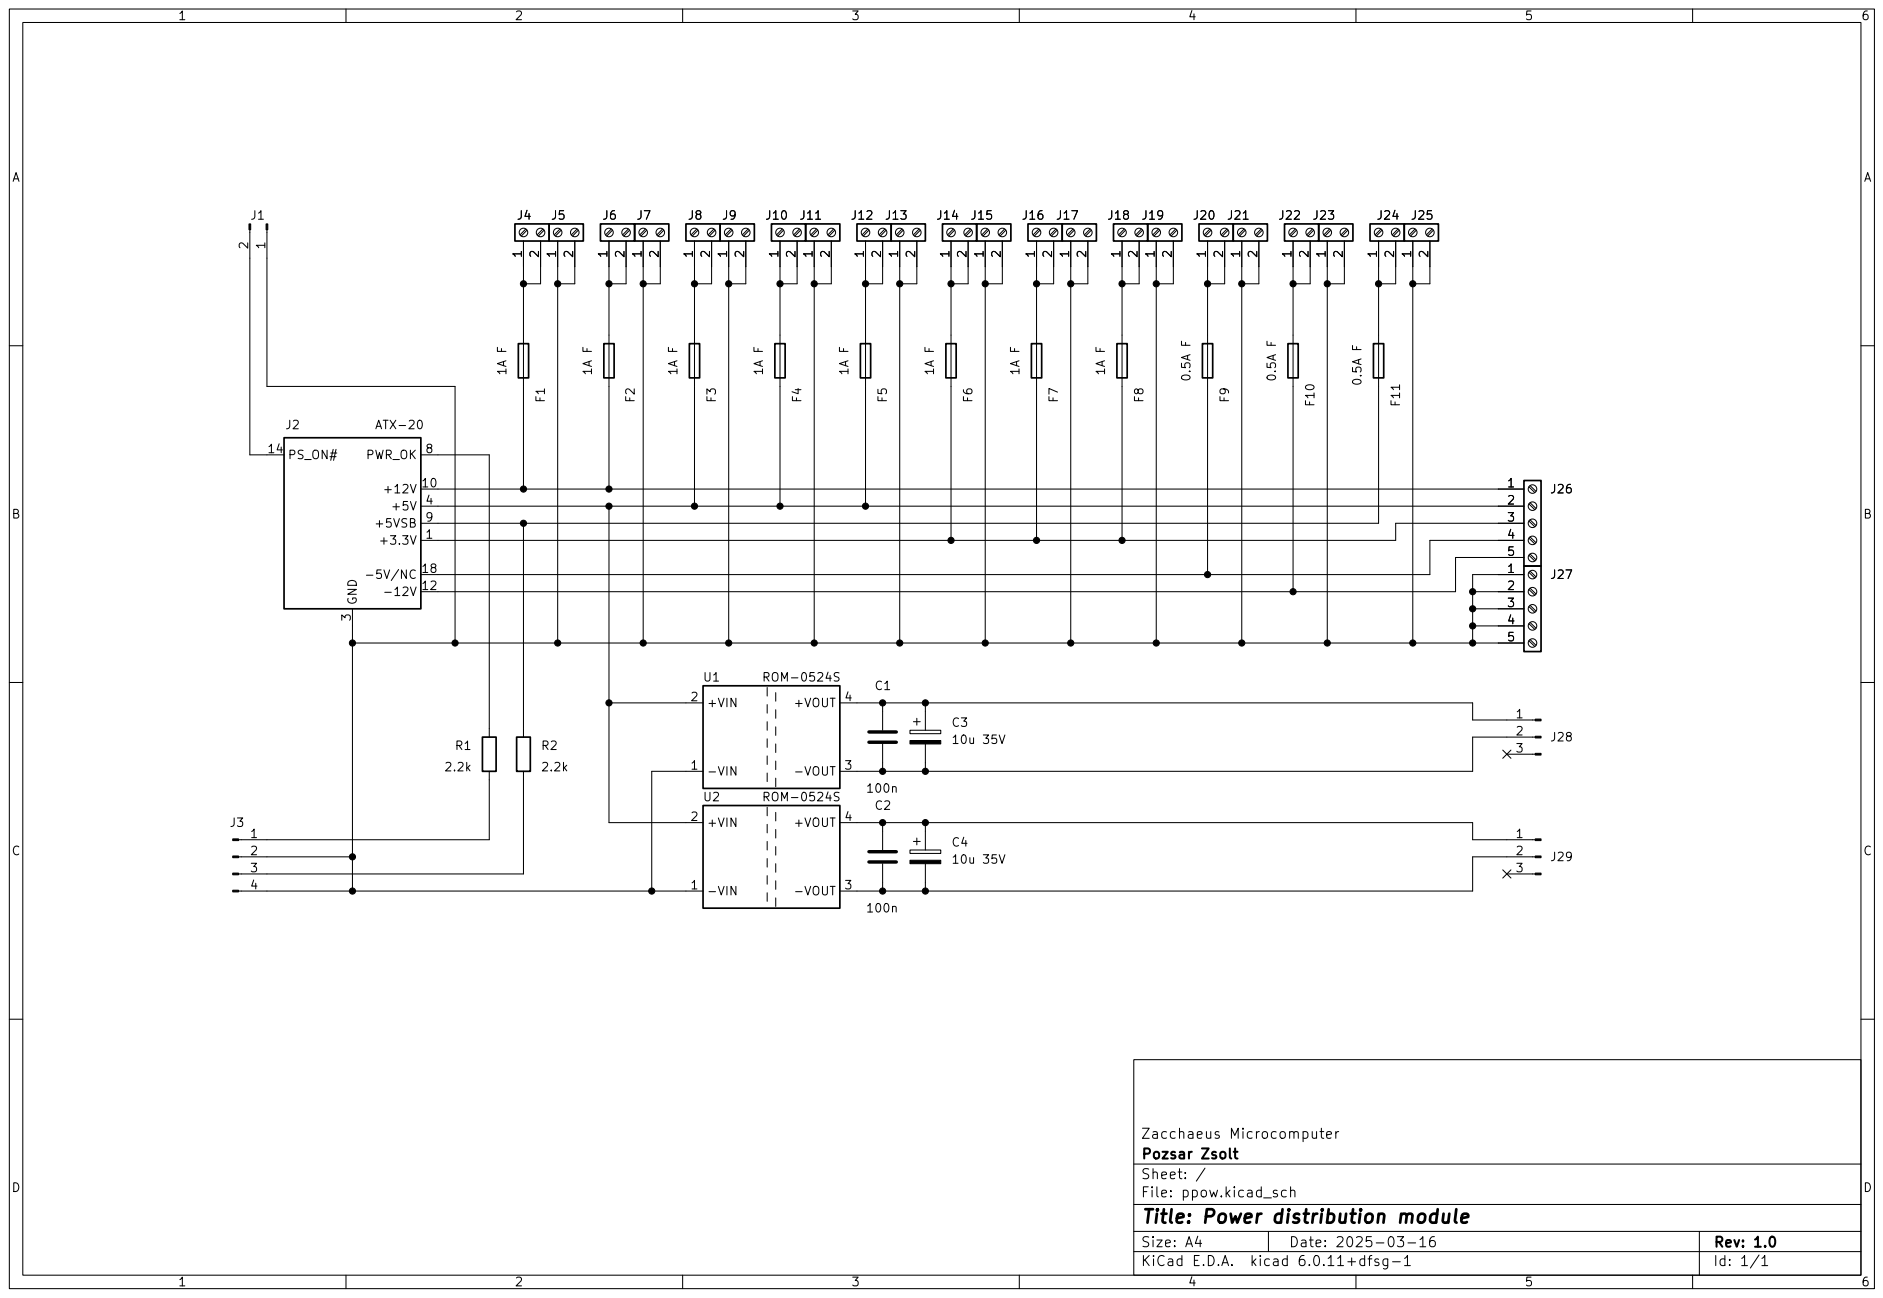
[picture p73: page 1]

2 2
3 3
4 4

Id: 1/1 Title: Power distribution module
