pozsarzs/zacchaeus/Zacchaeus computer/hardware/PMAN-SW Switch module/pman-sw-B_Cu.pdf

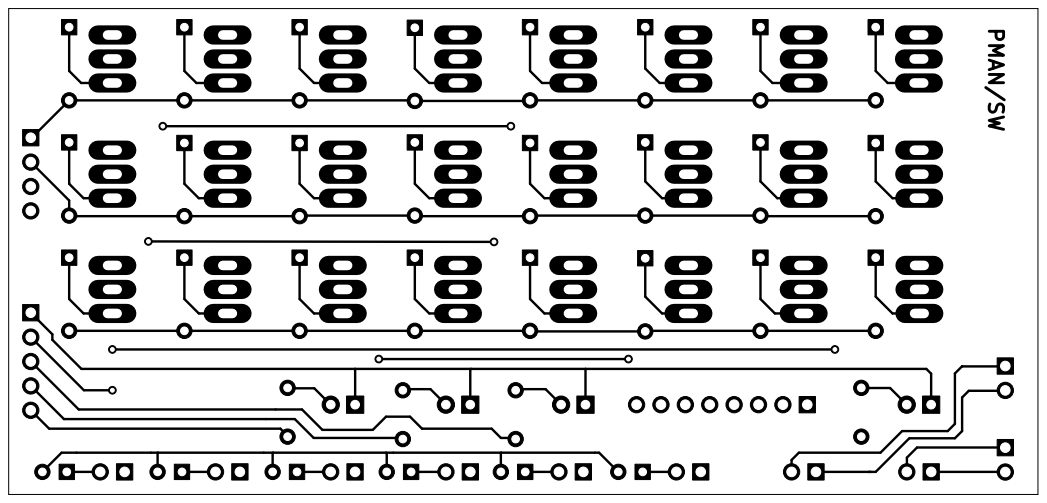
[picture p74: page 1]

Id: 1/1 Title: PMAN/SW - switch module
