pozsarzs/zacchaeus/Zacchaeus computer/hardware/PMAN-SW Switch module/pman-sw-F_Silkscreen.pdf

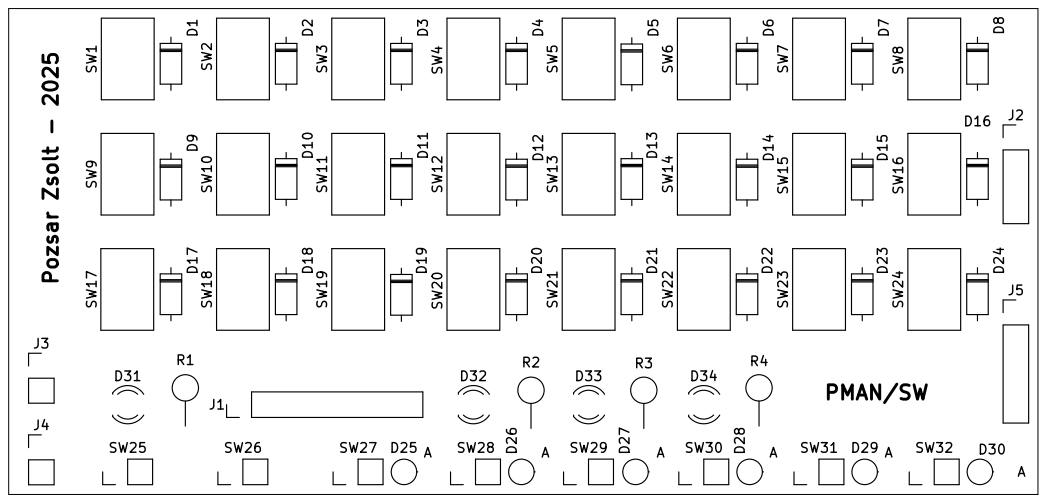
[picture p76: page 1]

Id: 1/1 Title: PMAN/SW - switch module
