pozsarzs/zacchaeus/Zacchaeus computer/hardware/SC126 Z180 motherboard/SC126 kit contents.pdf

6

2

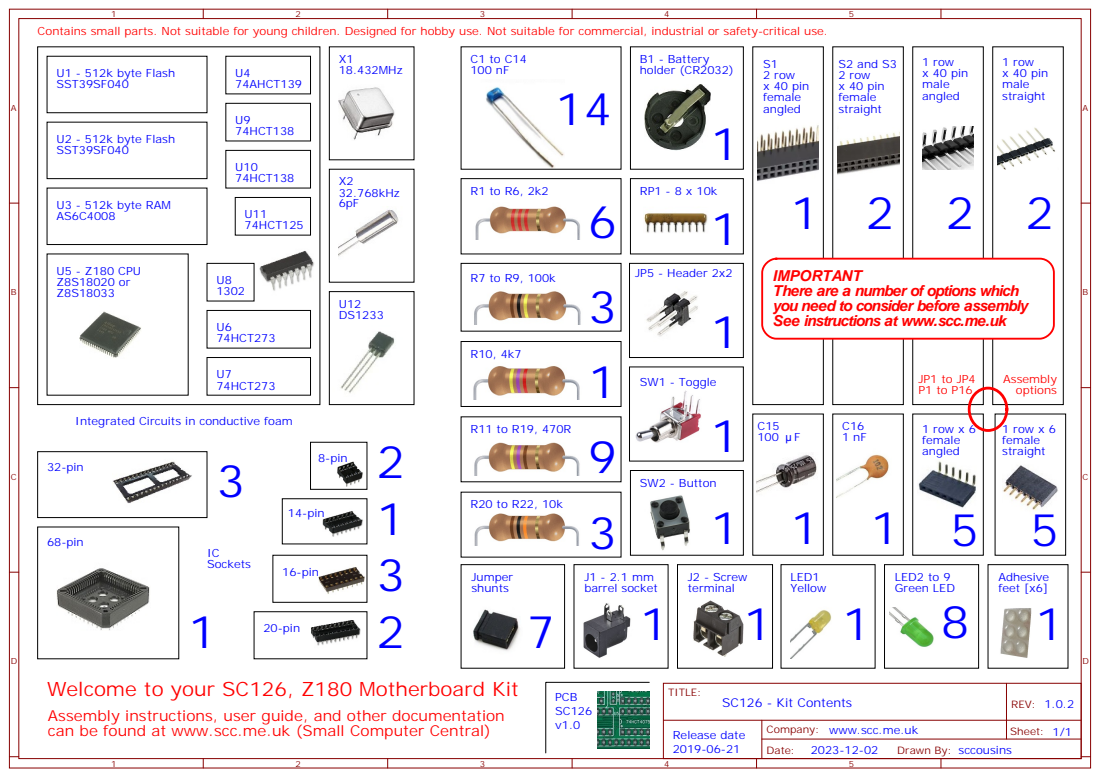
[picture p77: page 1]
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

IMPORTANT
There are a number of options which
you need to consider before assembly
See instructions at www.scc.me.uk

Welcome to your SC126, Z180 Motherboard Kit
Assembly instructions, user guide, and other documentation
can be found at www.scc.me.uk (Small Computer Central)

Company: www.scc.me.uk
