pozsarzs/zacchaeus/Zacchaeus computer/hardware/SC126 Z180 motherboard/SC126 schematic.pdf

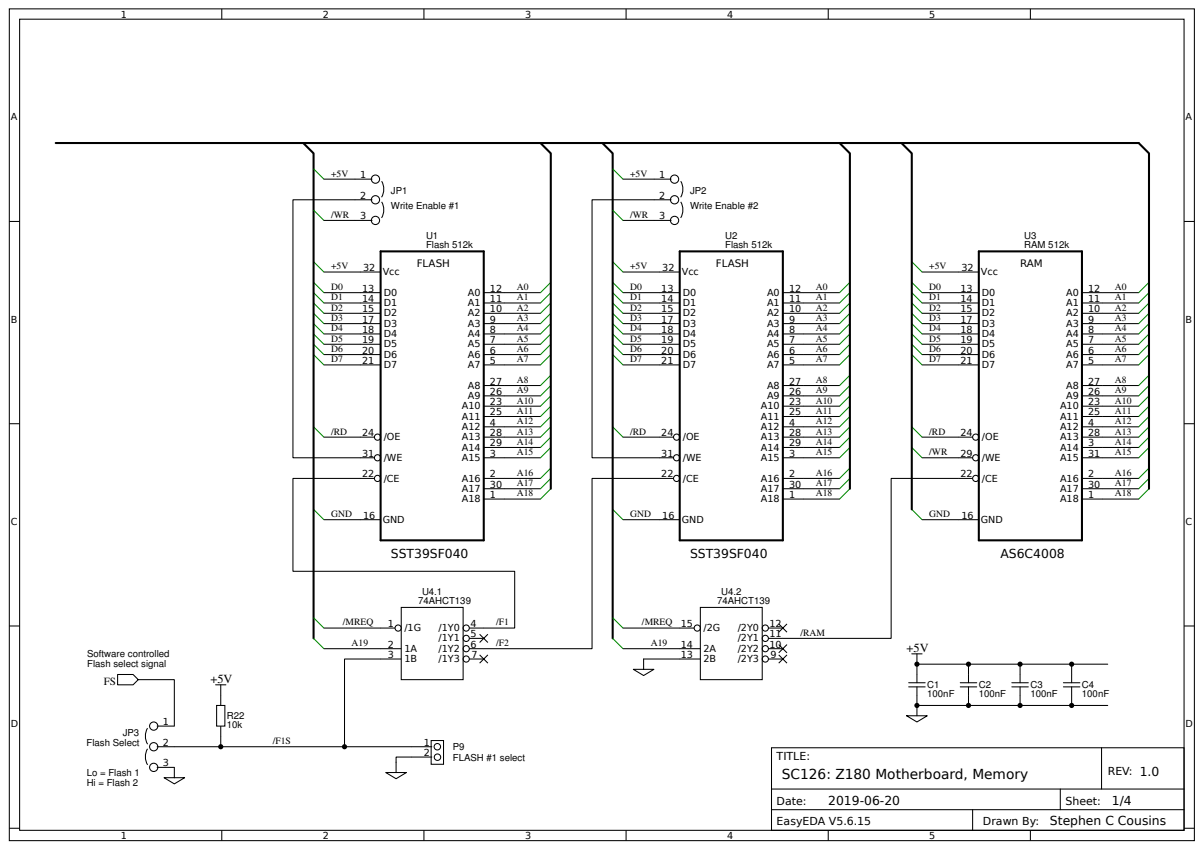
[picture p78: page 1]

+5V

+5V

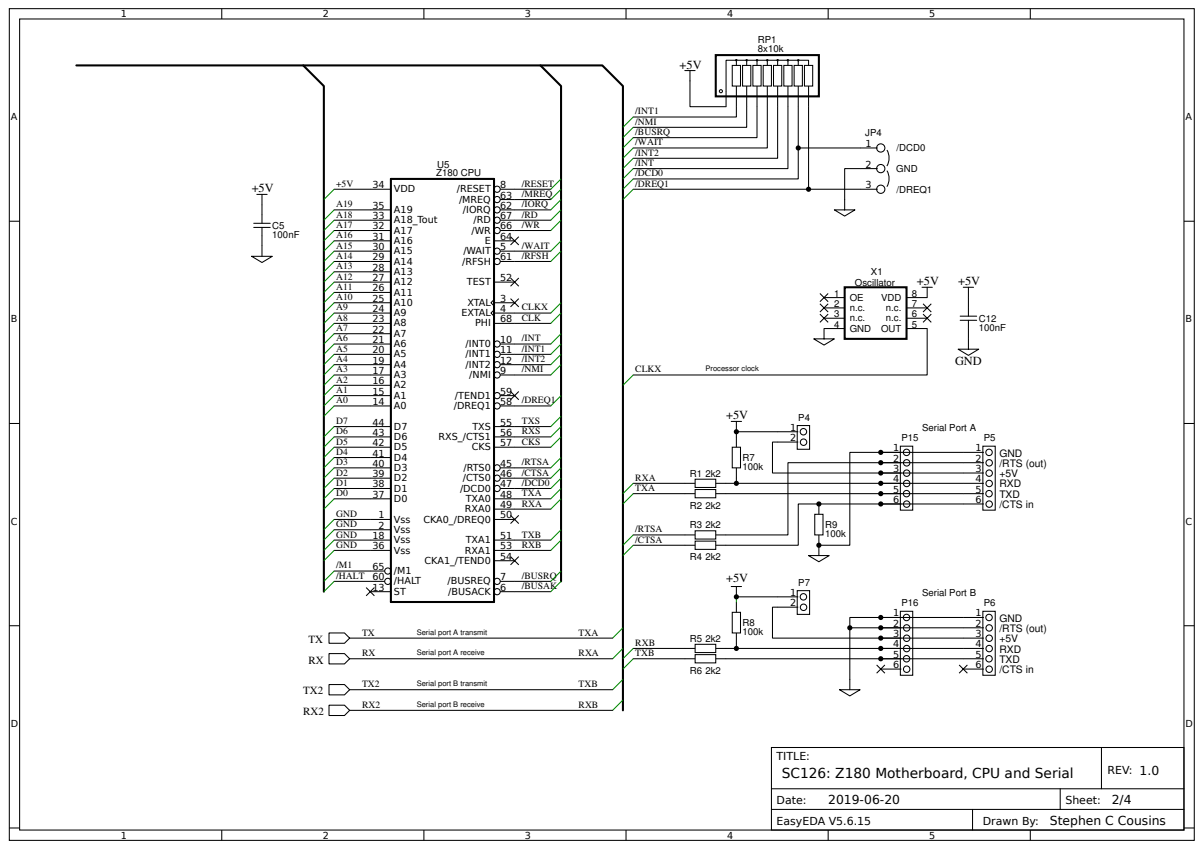
[picture p79: page 2]

+5V

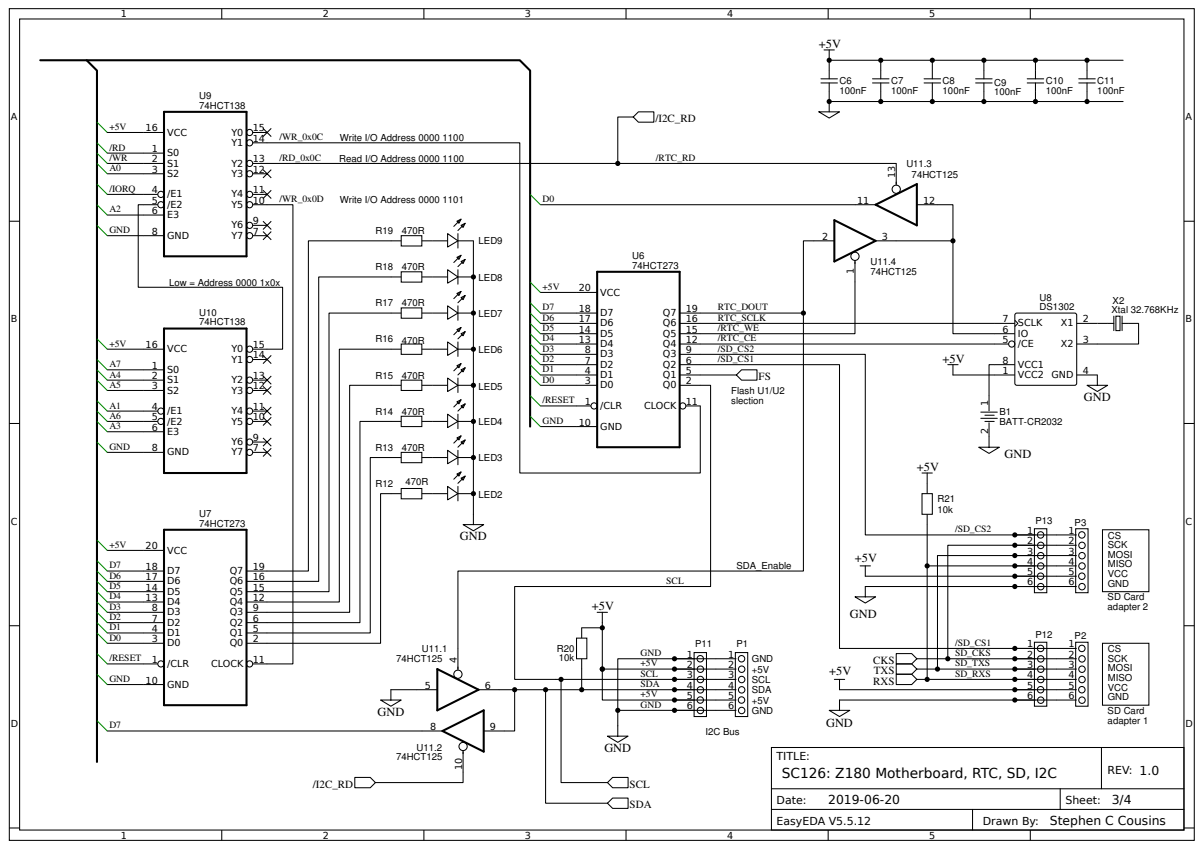
[picture p80: page 3]

+5V

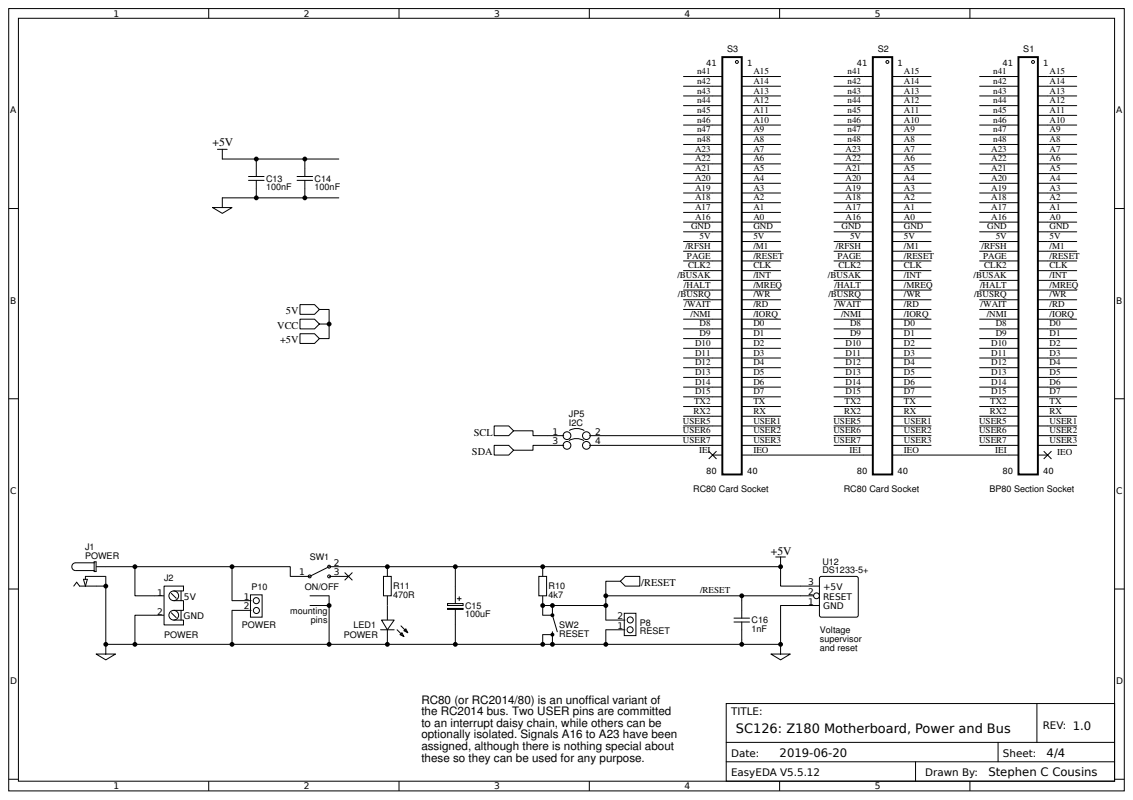
[picture p81: page 4]

RC80 (or RC2014/80) is an unoffical variant of
the RC2014 bus. Two USER pins are committed
to an interrupt daisy chain, while others can be
optionally isolated. Signals A16 to A23 have been
assigned, although there is nothing special about
these so they can be used for any purpose.
