pozsarzs/zacchaeus/Zacchaeus computer/hardware/SC715 RCBus CF module/SC715 kit contents.pdf

3

1 | 1

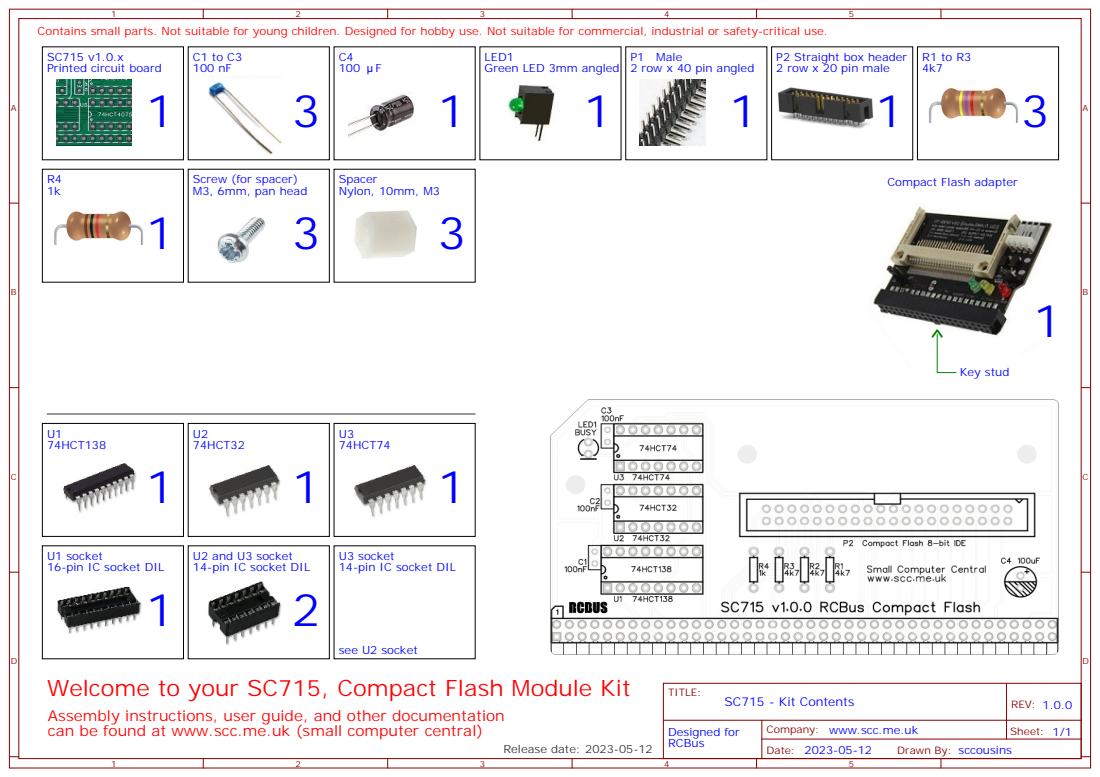
[picture p82: page 1]
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

U1 socket
16-pin IC socket DIL

U2 and U3 socket
14-pin IC socket DIL

U3 socket

Welcome to your SC715, Compact Flash Module Kit
Assembly instructions, user guide, and other documentation
can be found at www.scc.me.uk (small computer central)

Company: www.scc.me.uk
Date:
