pozsarzs/zacchaeus/Zacchaeus computer/hardware/PMAN-IF Interface module/pman-if-F_Cu.pdf

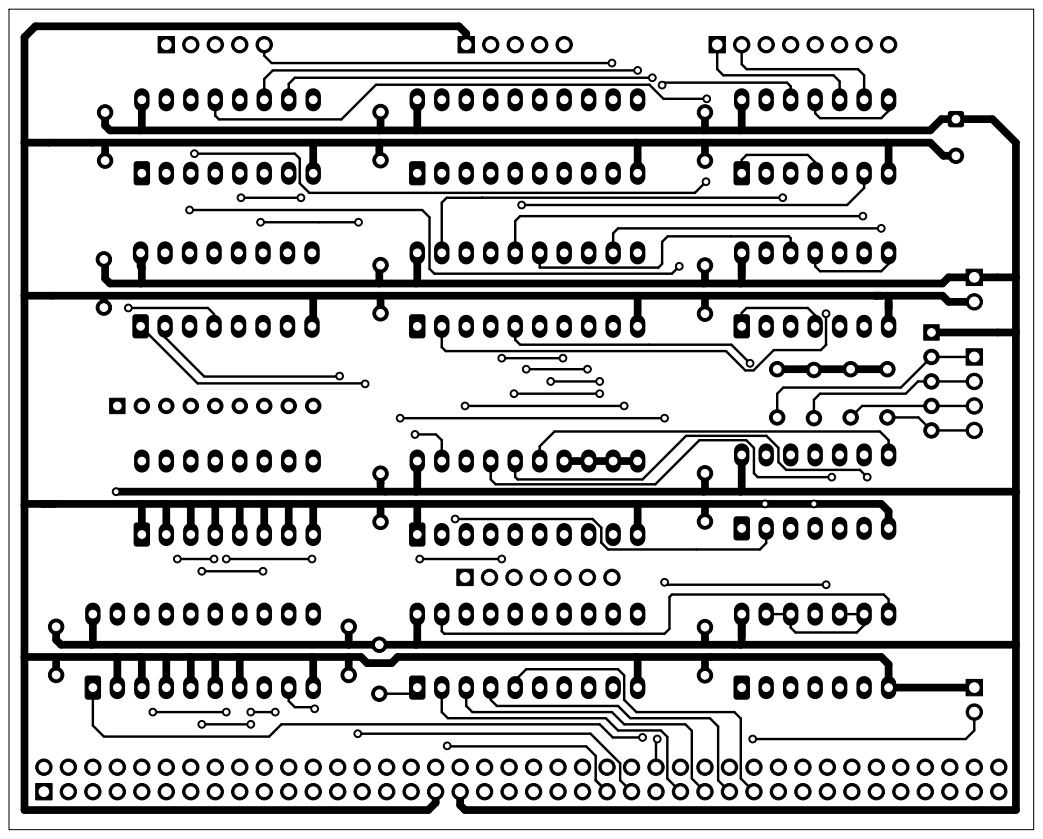
[picture p94: page 1]

Id: 1/2 Title: PMAN-IF Interface module
