pozsarzs/zacchaeus/Zacchaeus computer/hardware/PMAN-IF Interface module/pman-if-F_Silkscreen.pdf

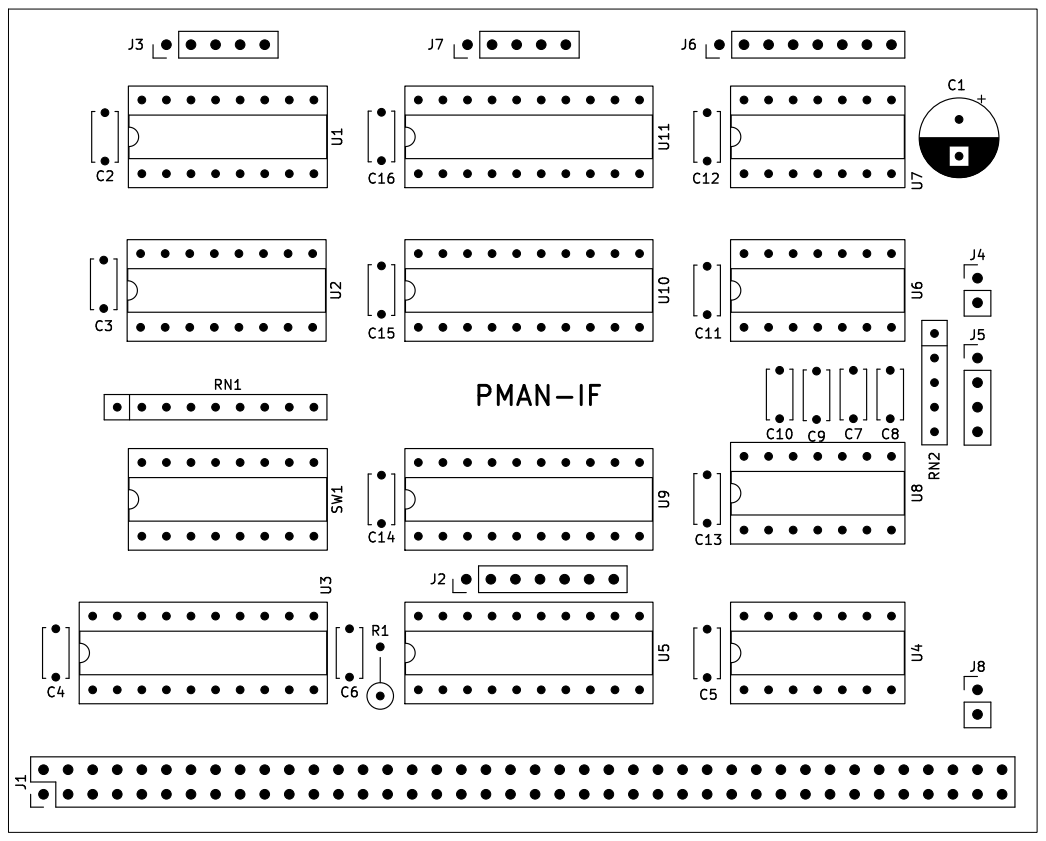
[picture p95: page 1]

Id: 2/2 Title: PMAN-IF Interface module
