pozsarzs/zacchaeus/Zacchaeus computer/hardware/PMAN-IF Interface module/pman-if.pdf

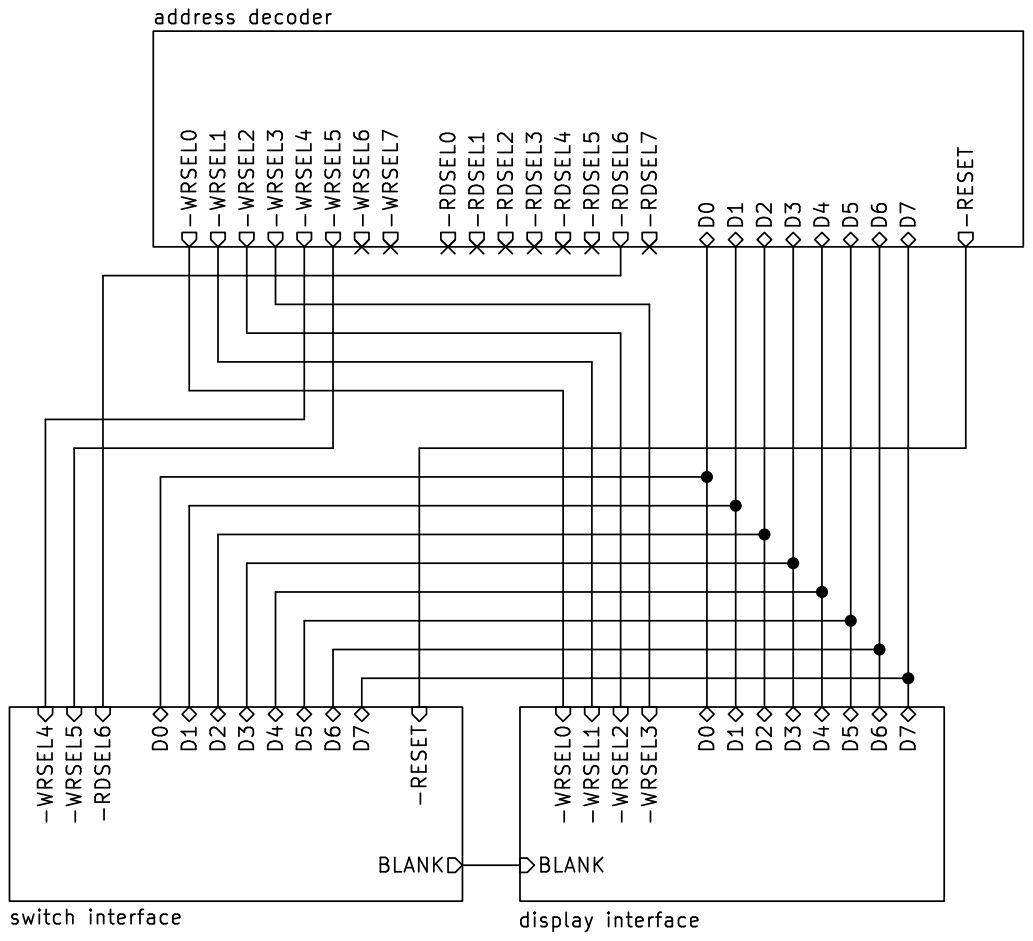
[picture p96: page 1]

Id: 1/4 Title: PMAN-IF - Manual control panel interface module

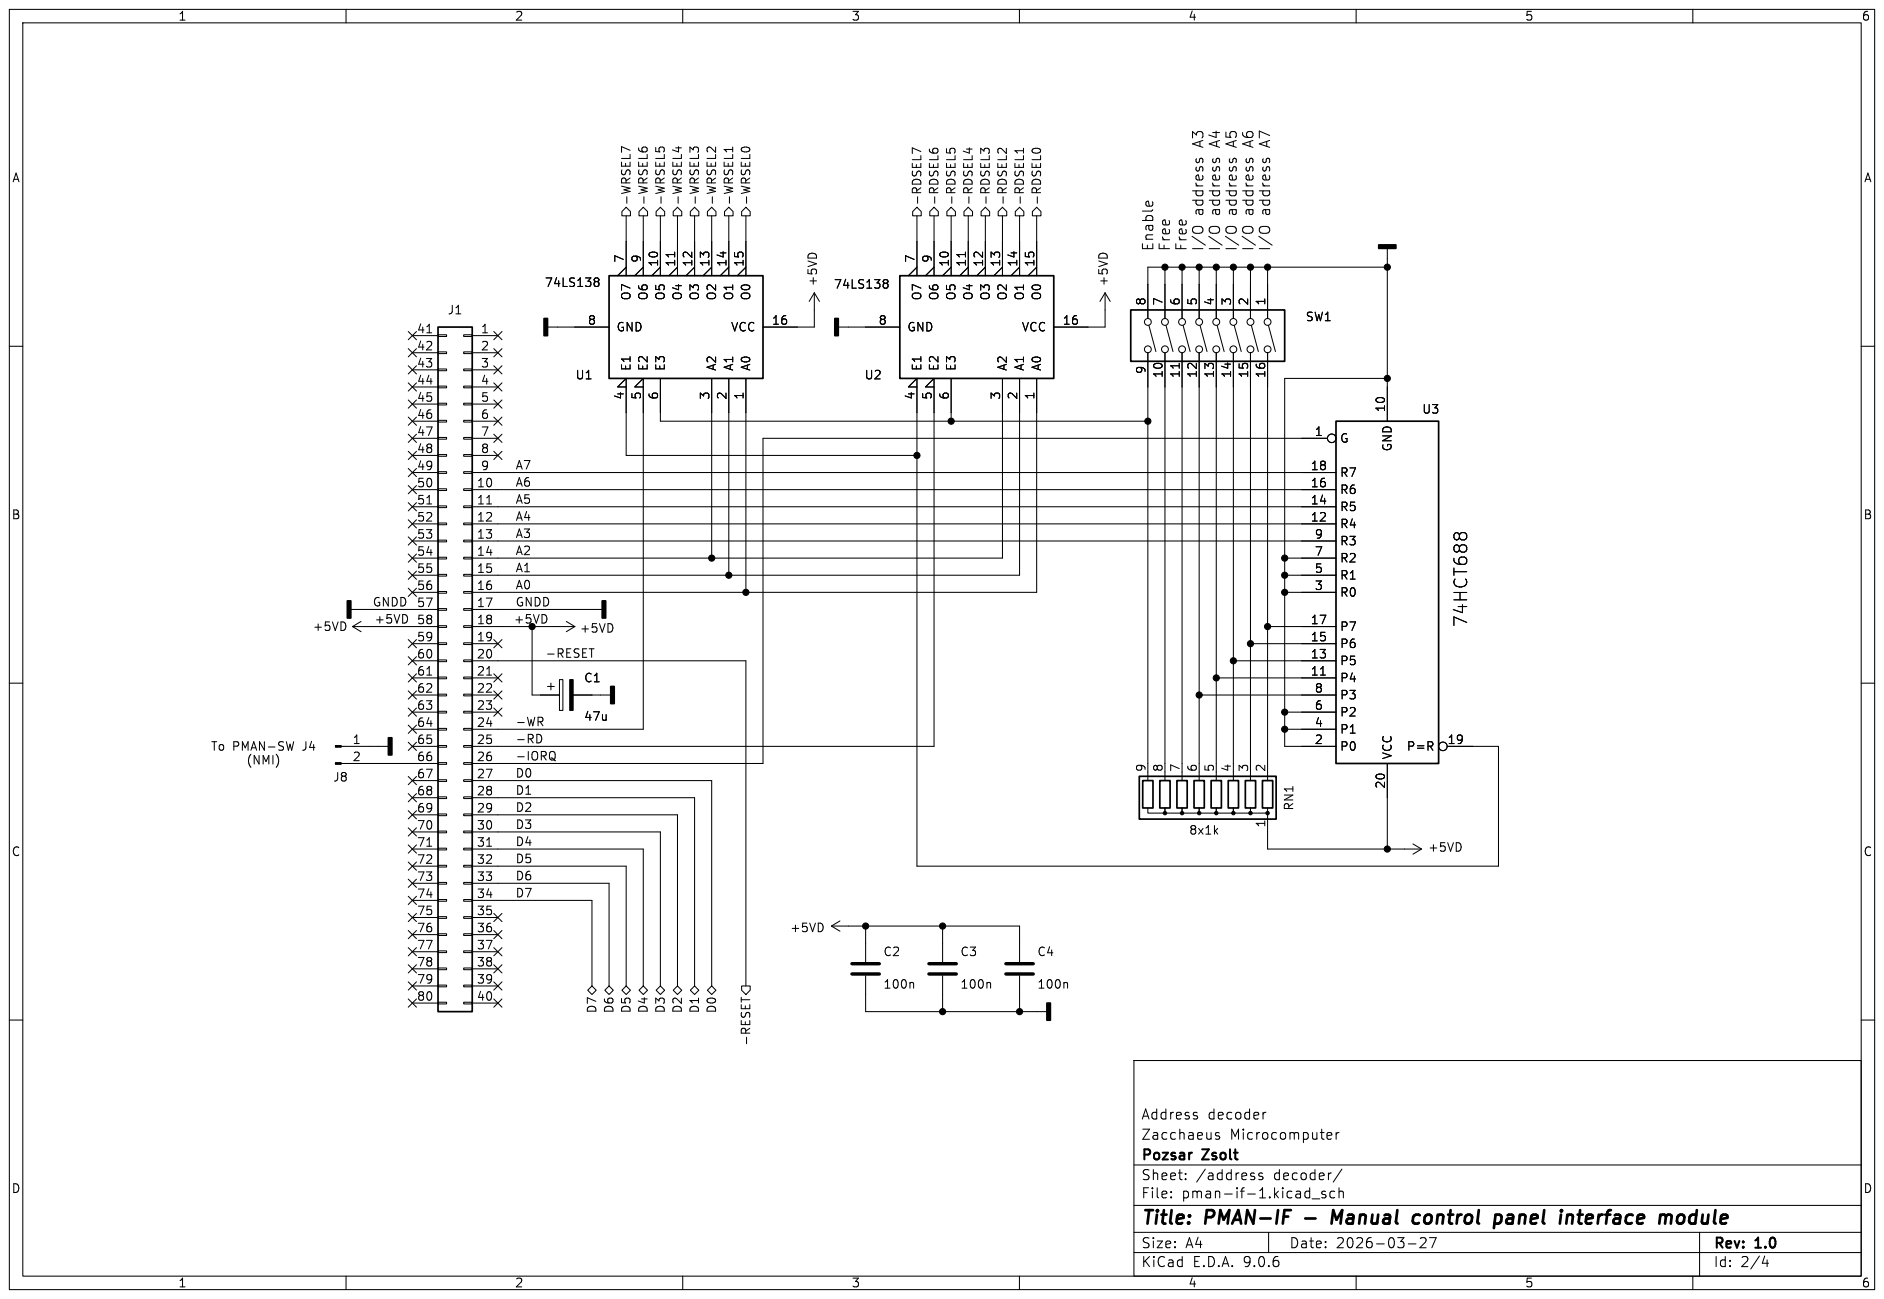
[picture p97: page 2]

Id: 2/4 Title: PMAN-IF - Manual control panel interface module

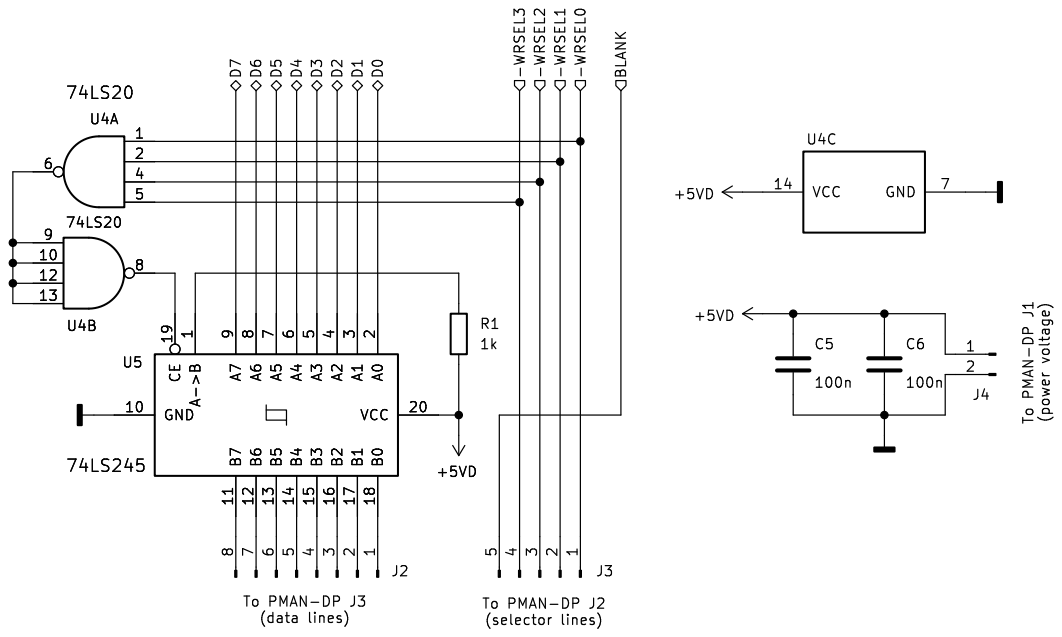
[picture p98: page 3]

2 2
4 4
5 5

Id: 3/4 Title: PMAN-IF - Manual control panel interface module

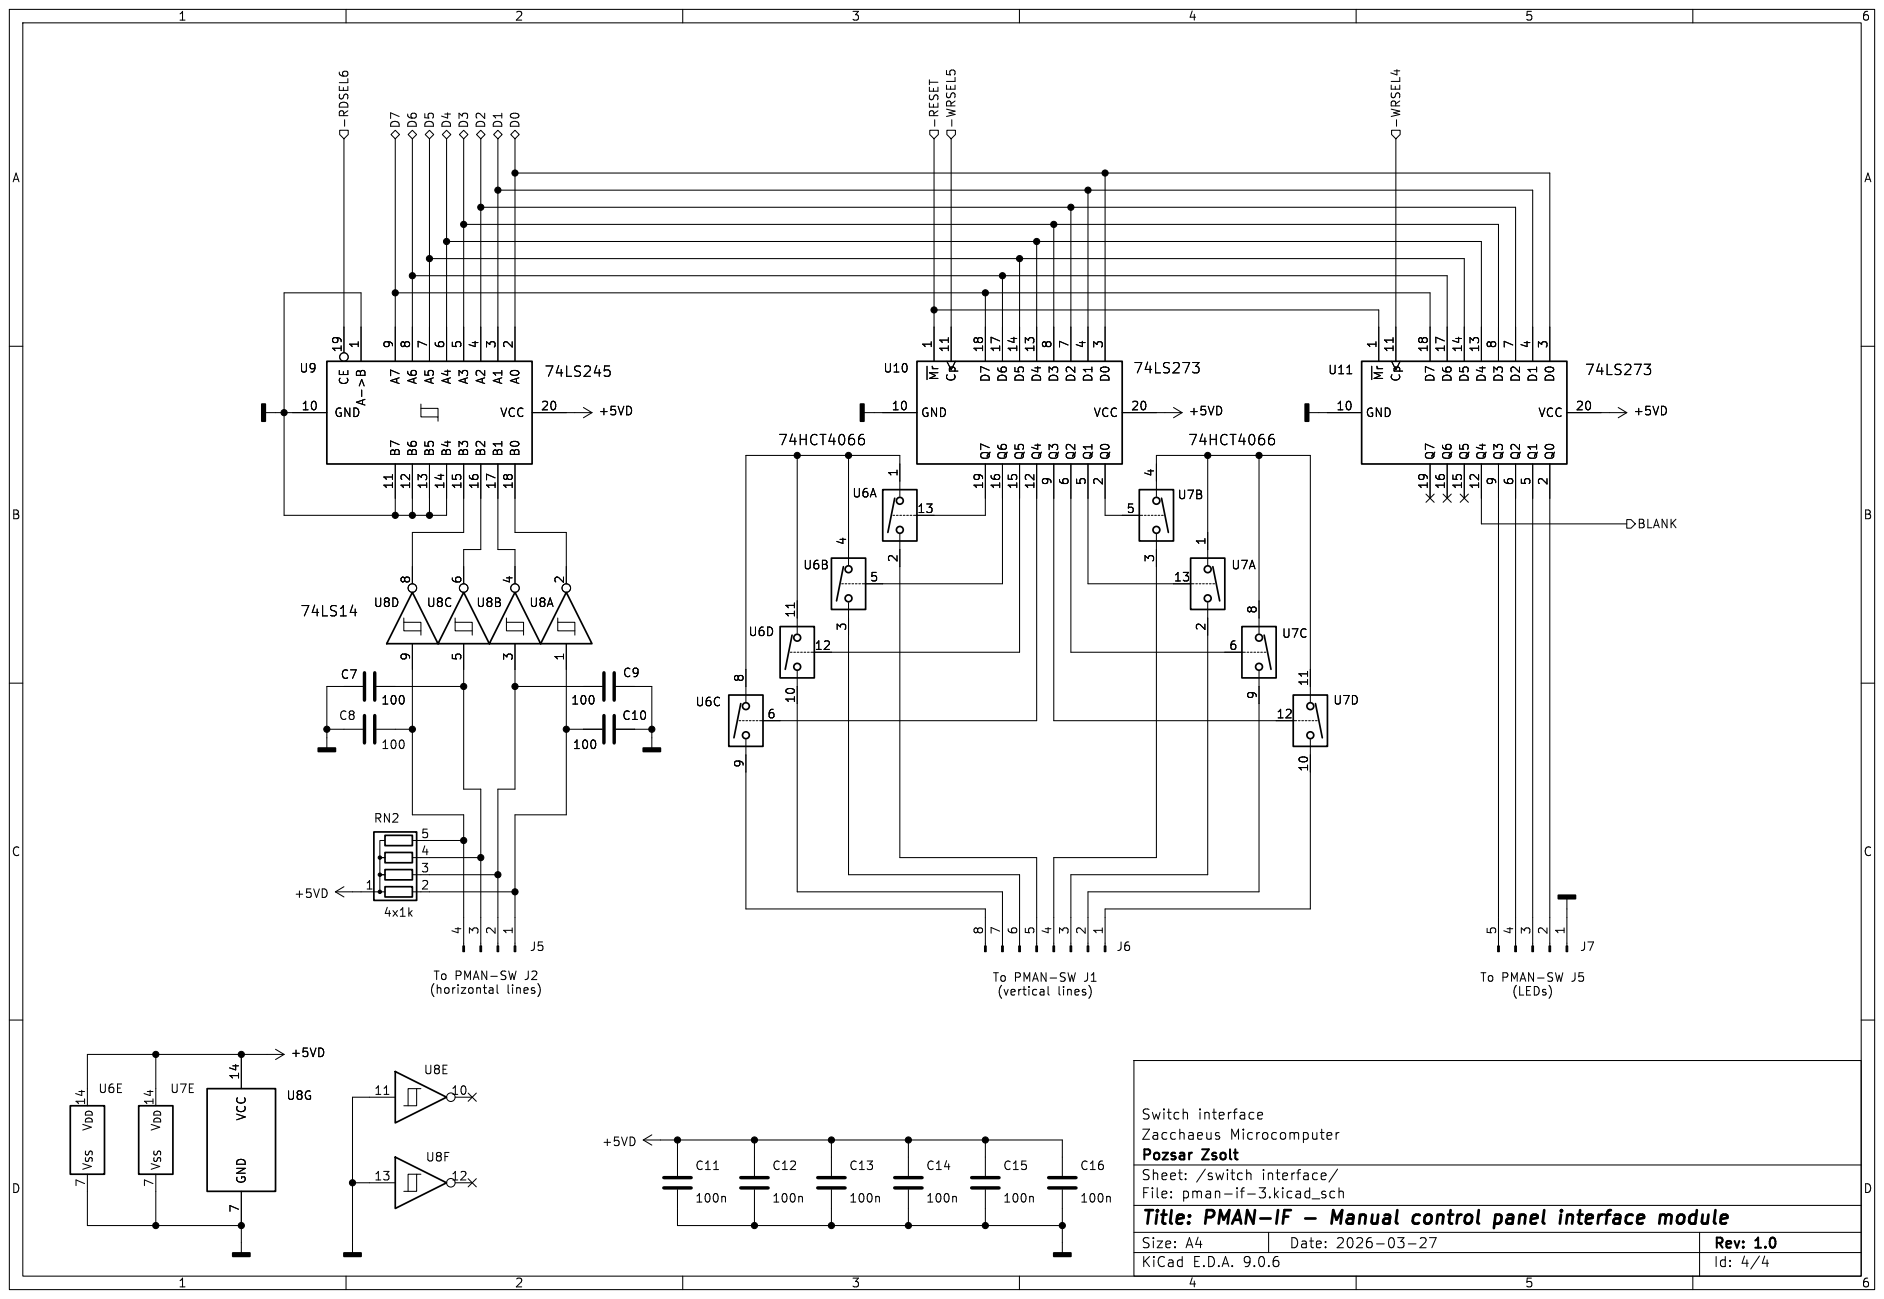
[picture p99: page 4]

8 D4 13 D5 14 D6 17 D7 18 Cp 11 ~{Mr} 1 VCC 20 GND 10 Q0

Id: 4/4 Title: PMAN-IF - Manual control panel interface module
