pozsarzs/zacchaeus/Zacchaeus computer/hardware/PFRP Front panel/pfrp.pdf

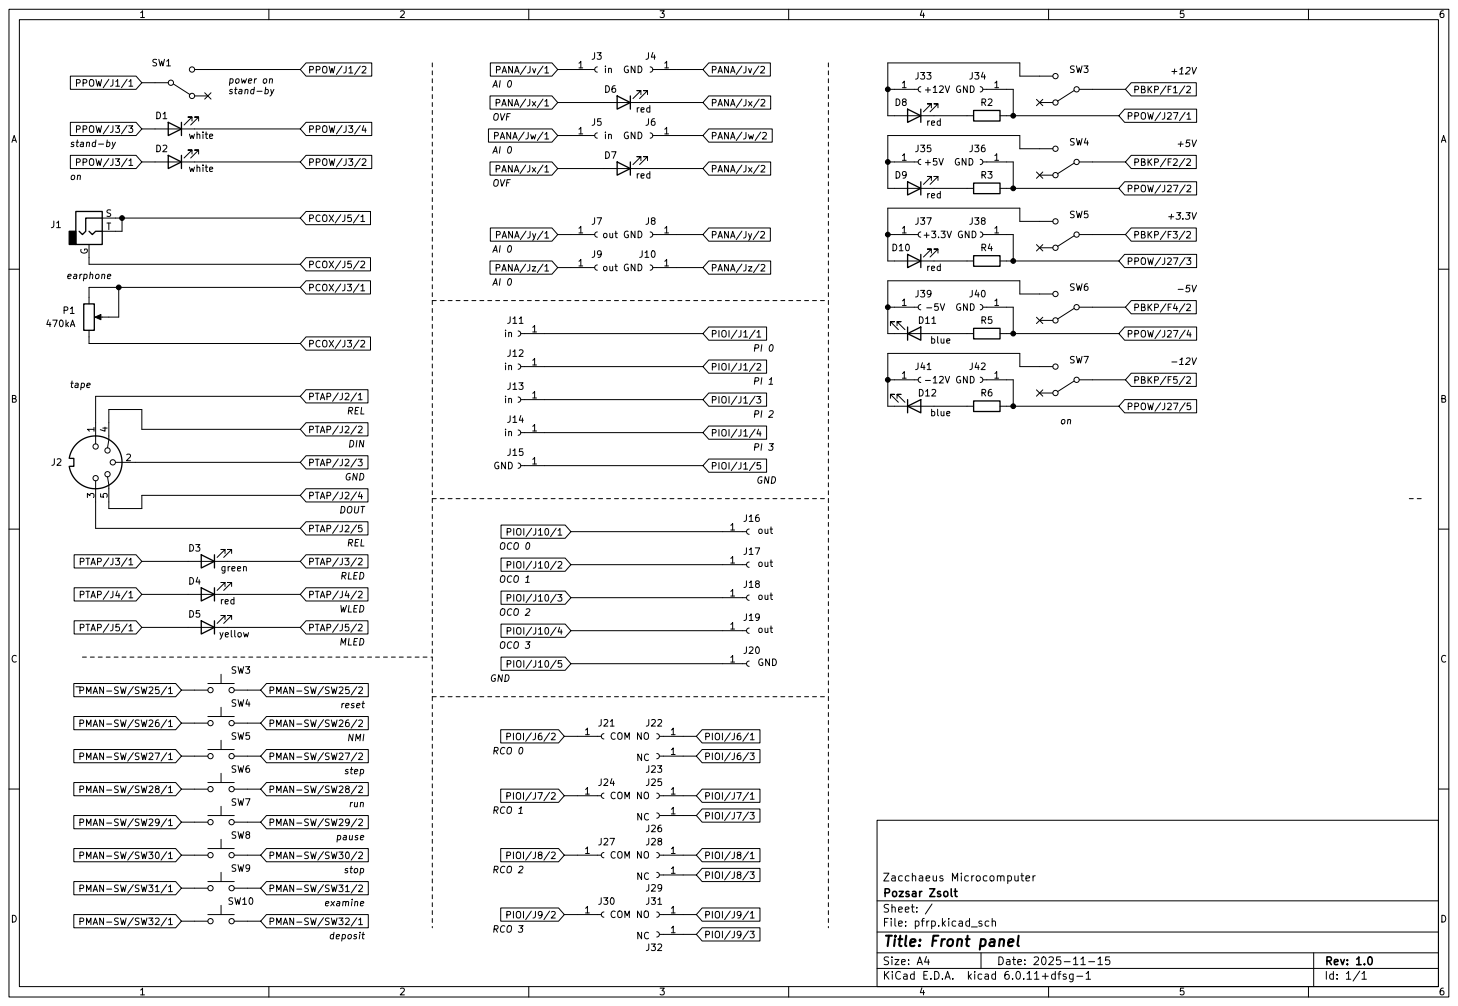
[picture p100: page 1]
