pozsarzs/zacchaeus/PEIX External interface box/hardware/ebe_287-1/ebe_287-1-analog.pdf

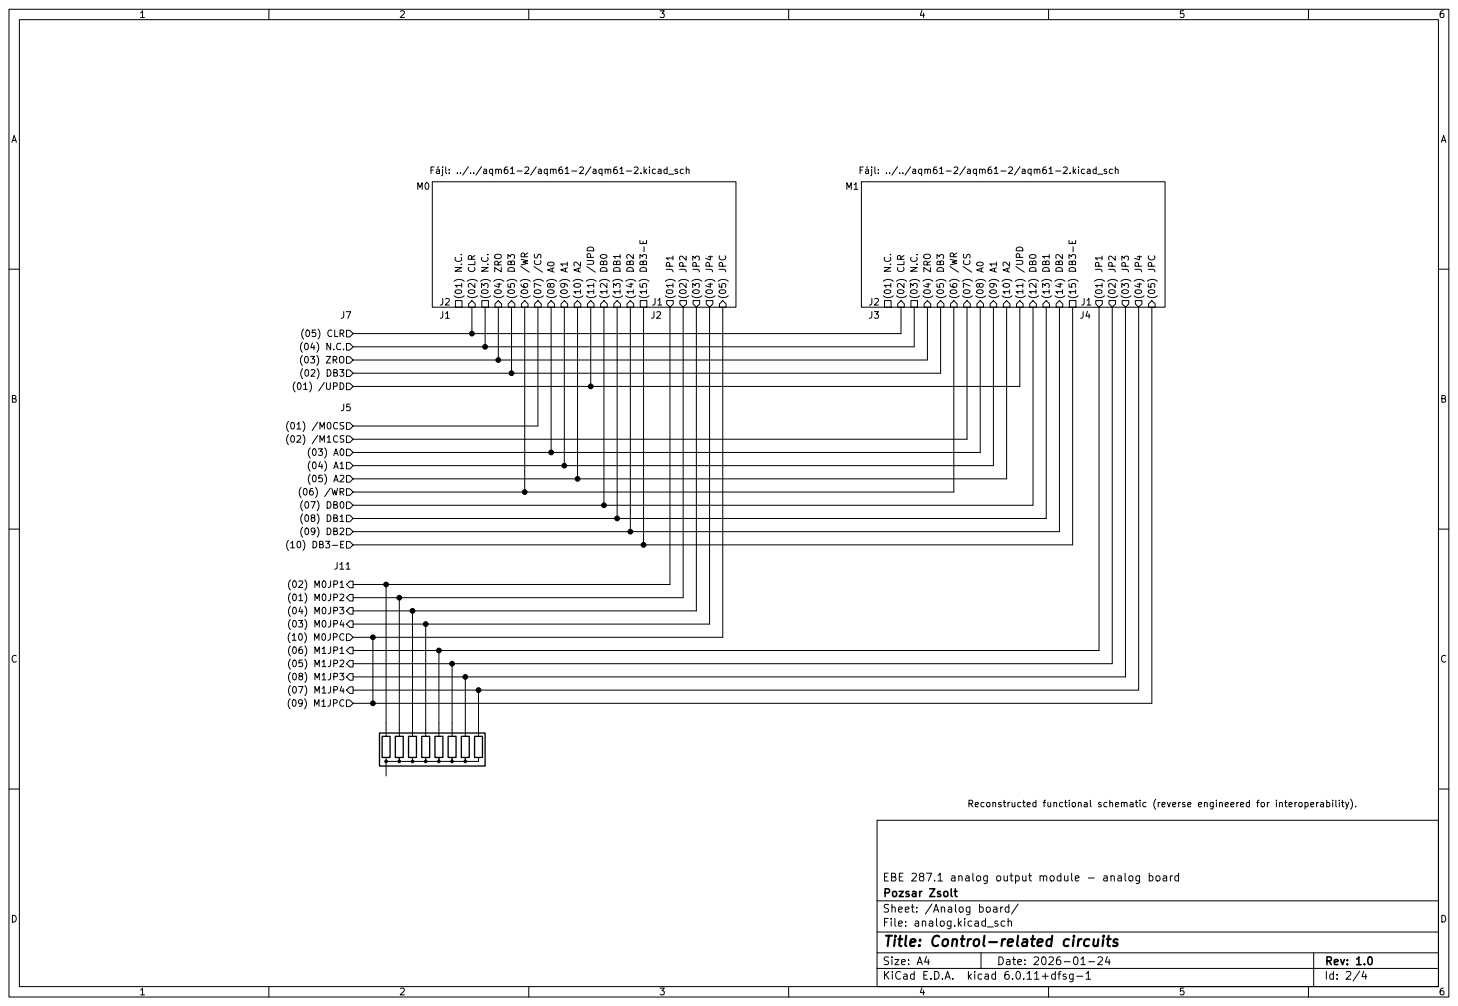
[picture p101: page 1]
