pozsarzs/zacchaeus/PEIX External interface box/hardware/ebe_287-1/ebe_287-1-digital.pdf

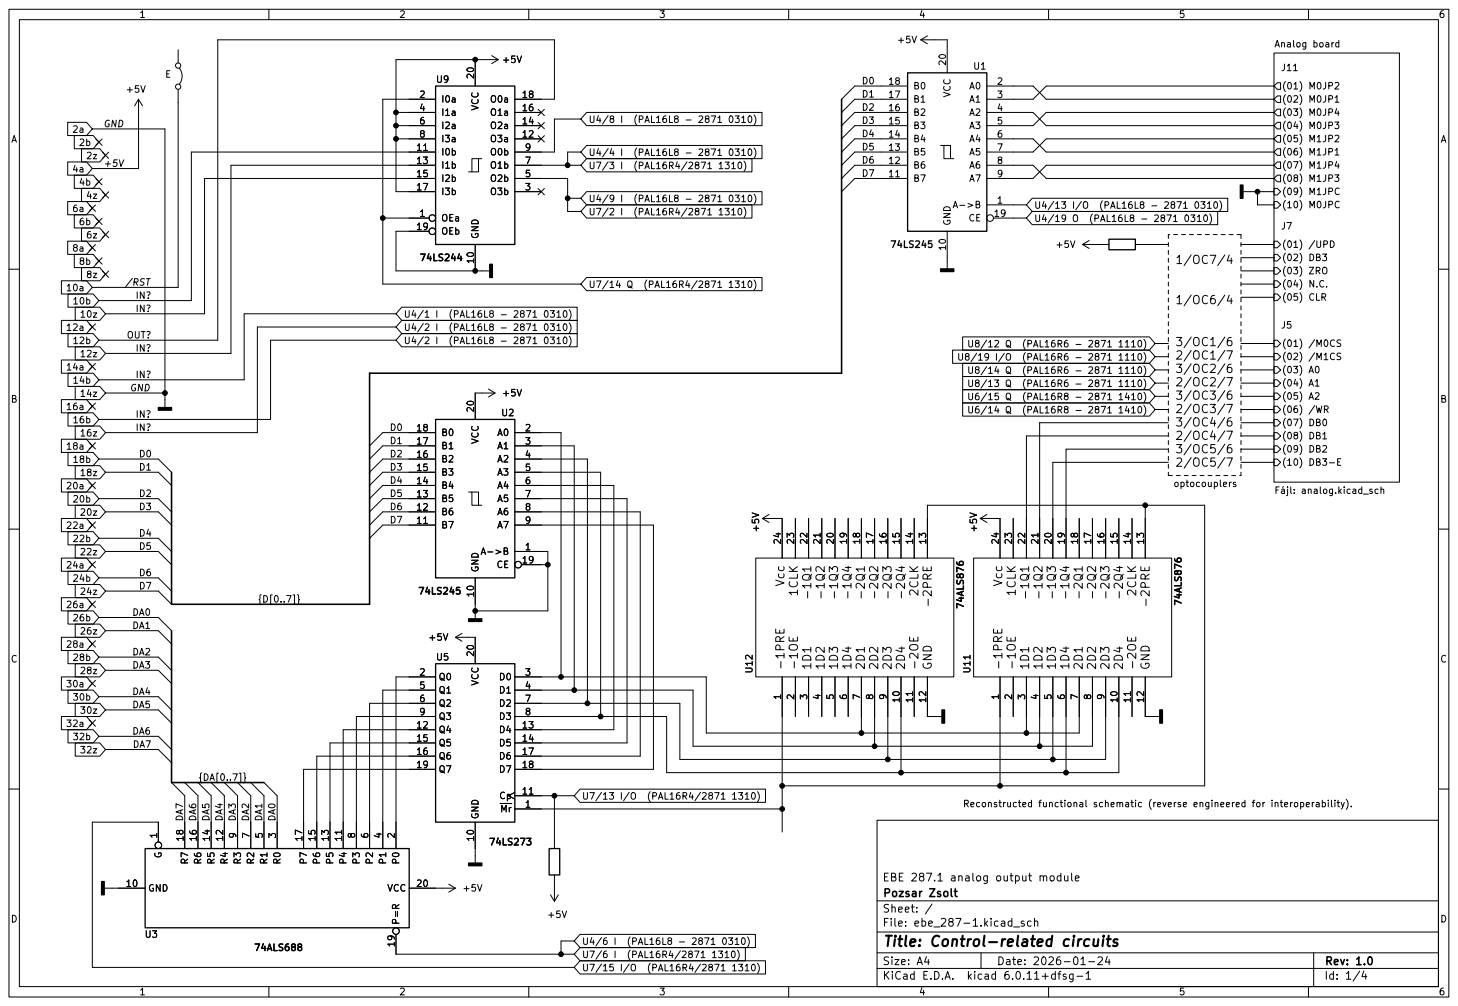
[picture p102: page 1]
