pozsarzs/zacchaeus/PEIX External interface box/hardware/ebe_206-1/ebe_206-1.pdf

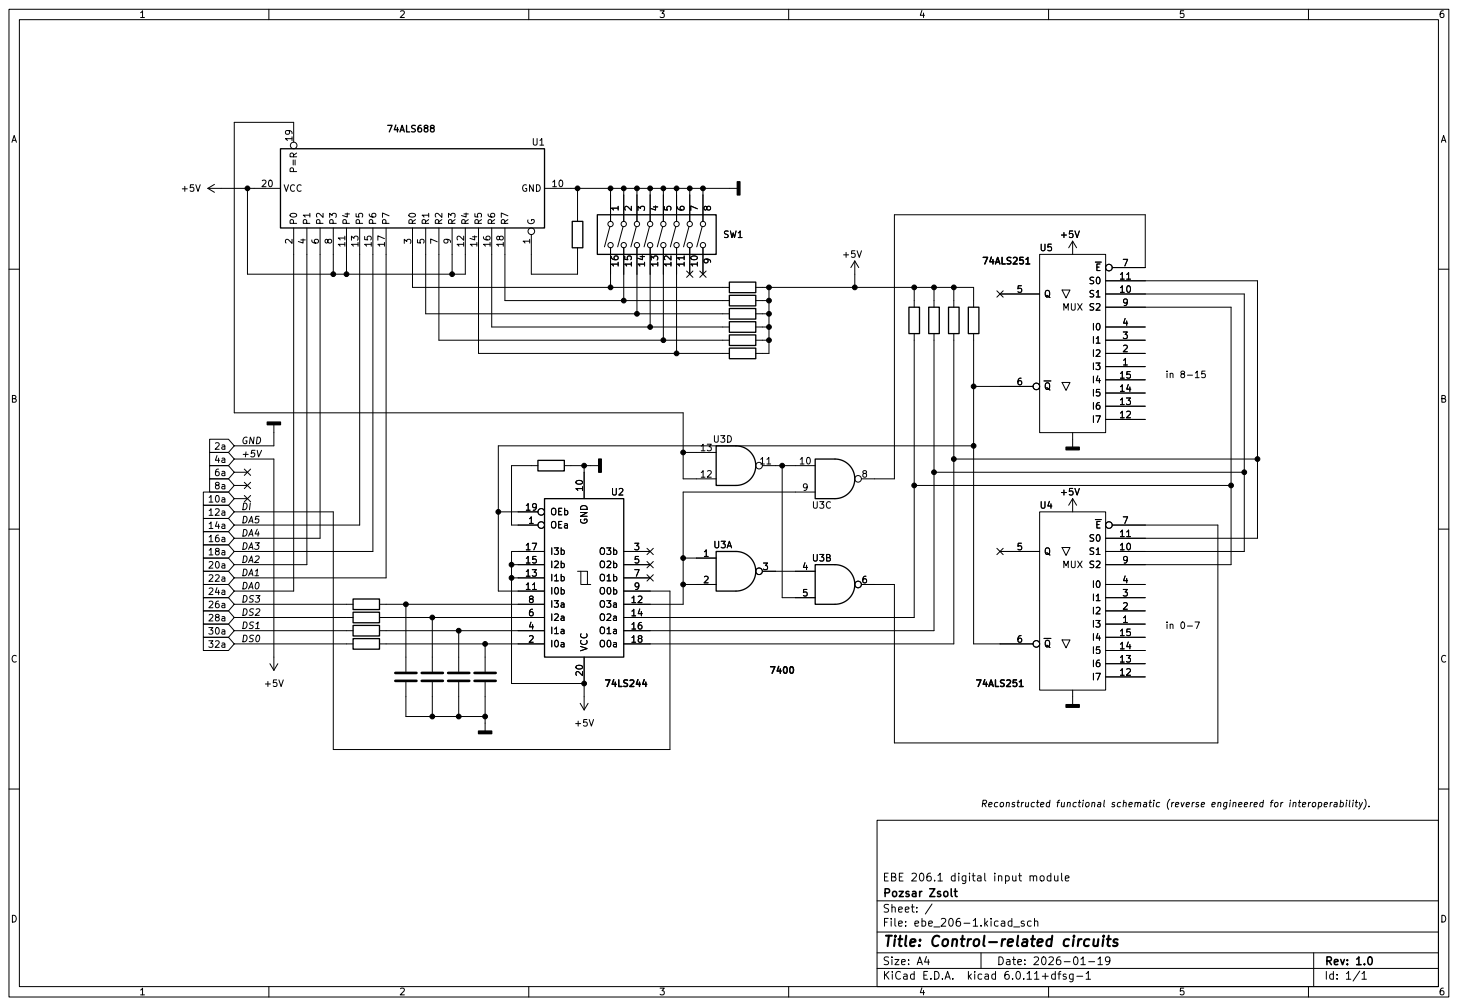
[picture p103: page 1]
