pozsarzs/zacchaeus/PEIX External interface box/hardware/ebe_266-1/ebe_266-1.pdf

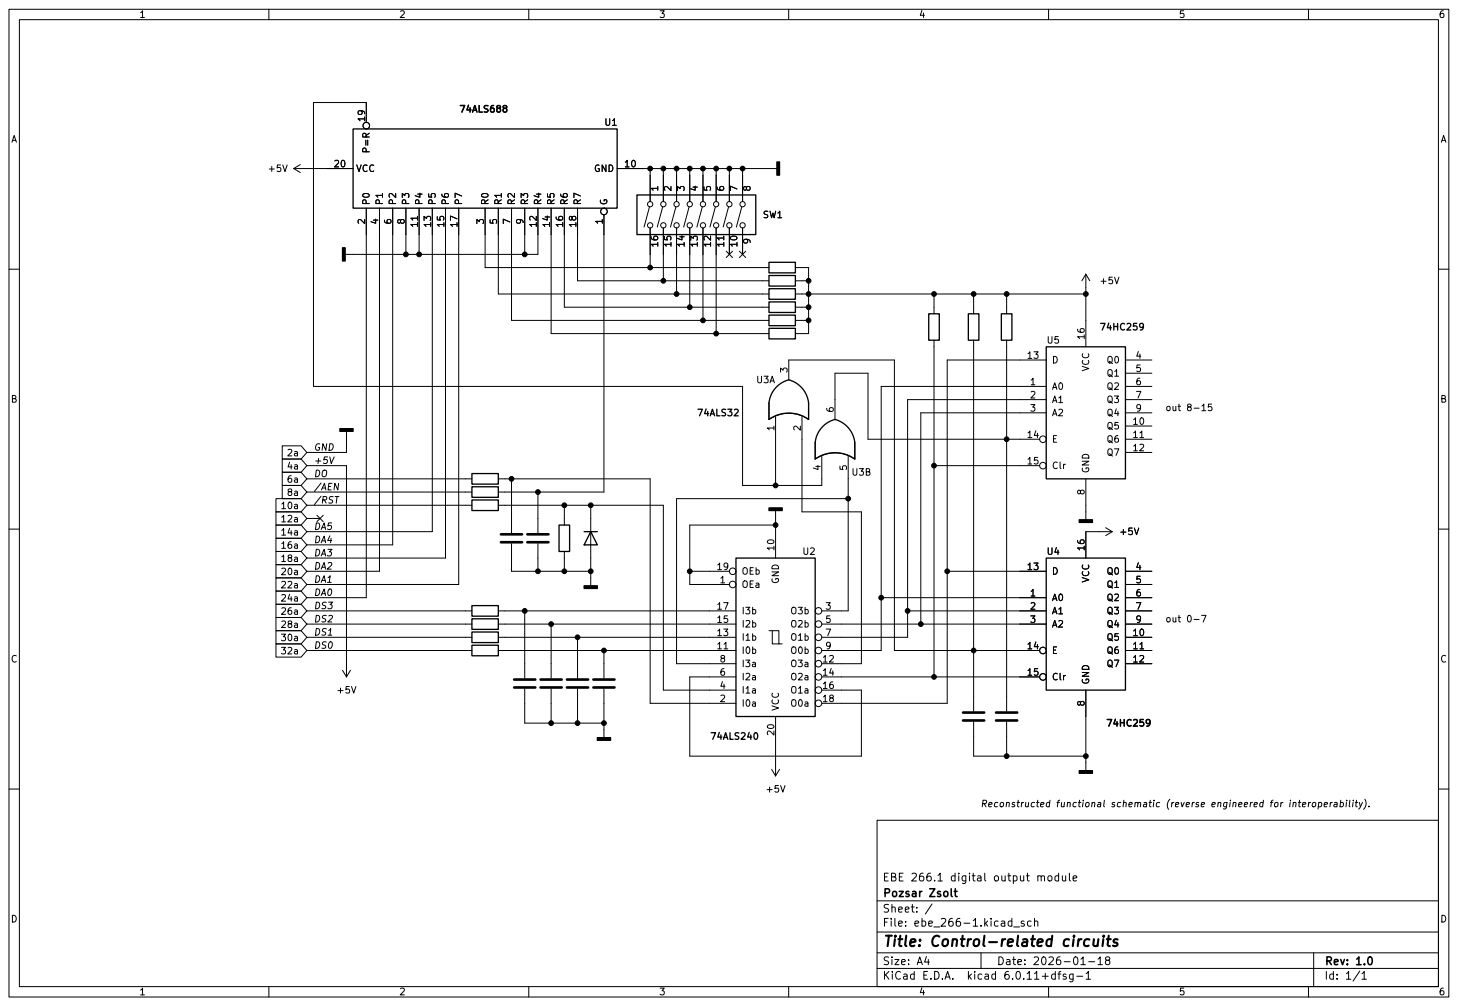
[picture p104: page 1]
