pozsarzs/zacchaeus/Zacchaeus computer/hardware/PBKP Back panel/pbkp.pdf

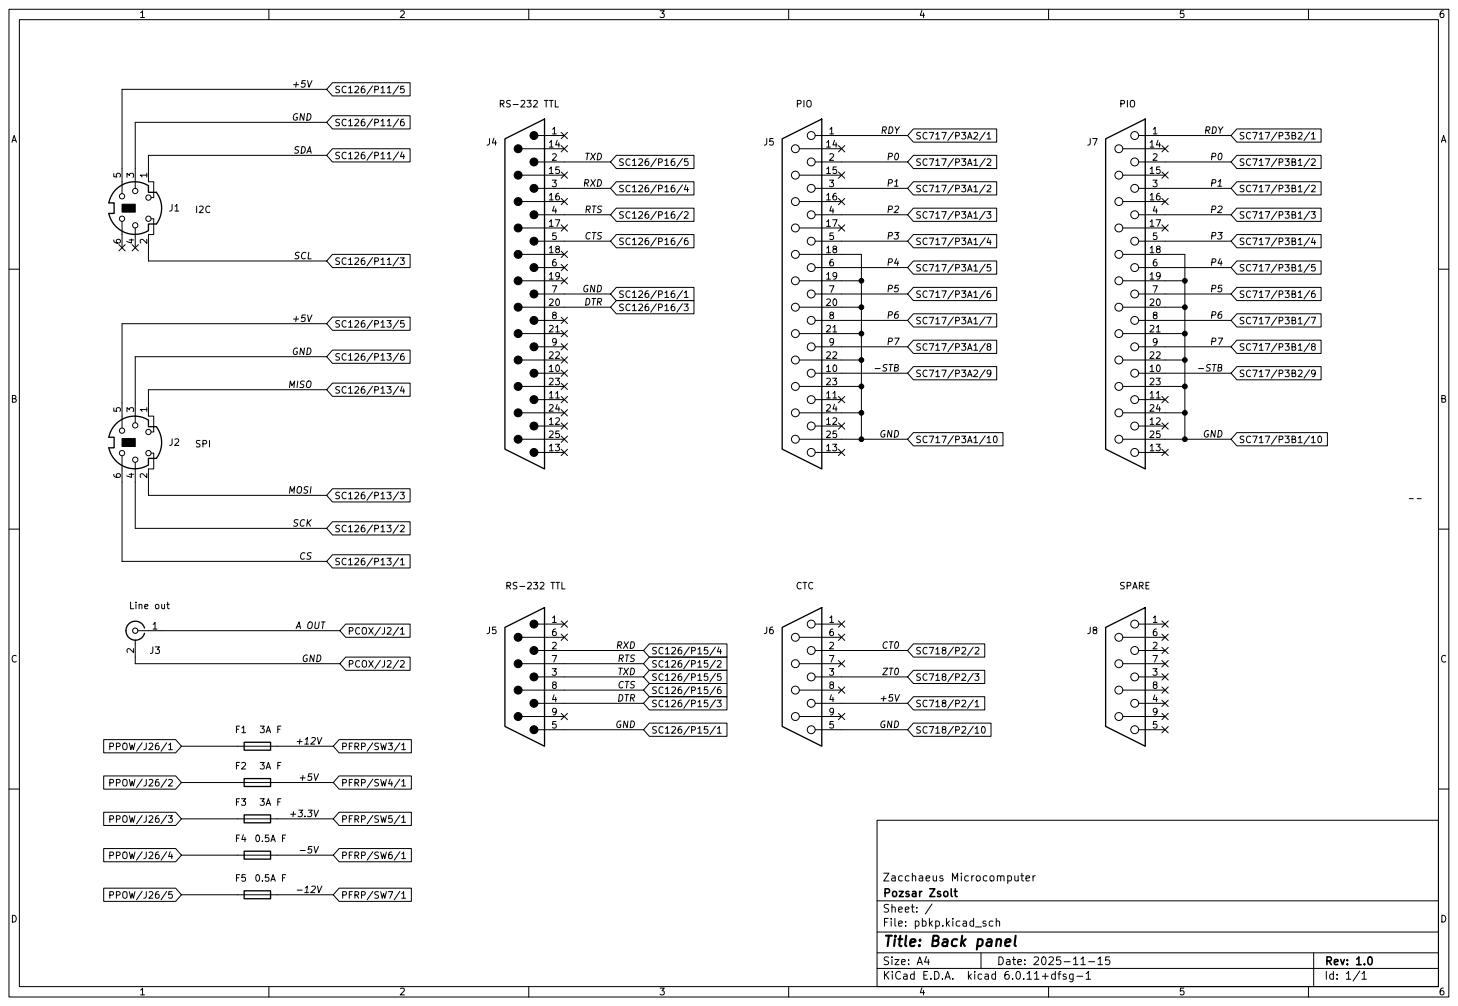
[picture p105: page 1]
