pozsarzs/zacchaeus/Zacchaeus computer/hardware/PCOX COVOX module/pcox-B_Cu.pdf

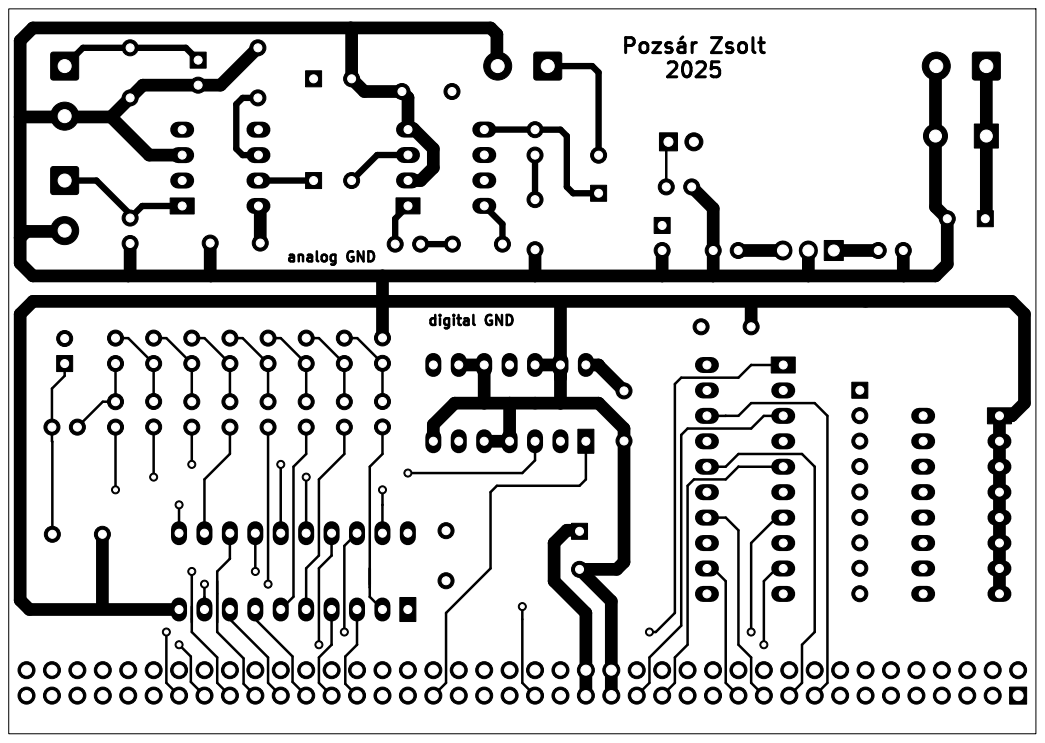
[picture p106: page 1]

Id: 1/1 Title: PCOX - COVOX module
