pozsarzs/zacchaeus/Zacchaeus computer/hardware/PCOX COVOX module/pcox-F_Cu.pdf

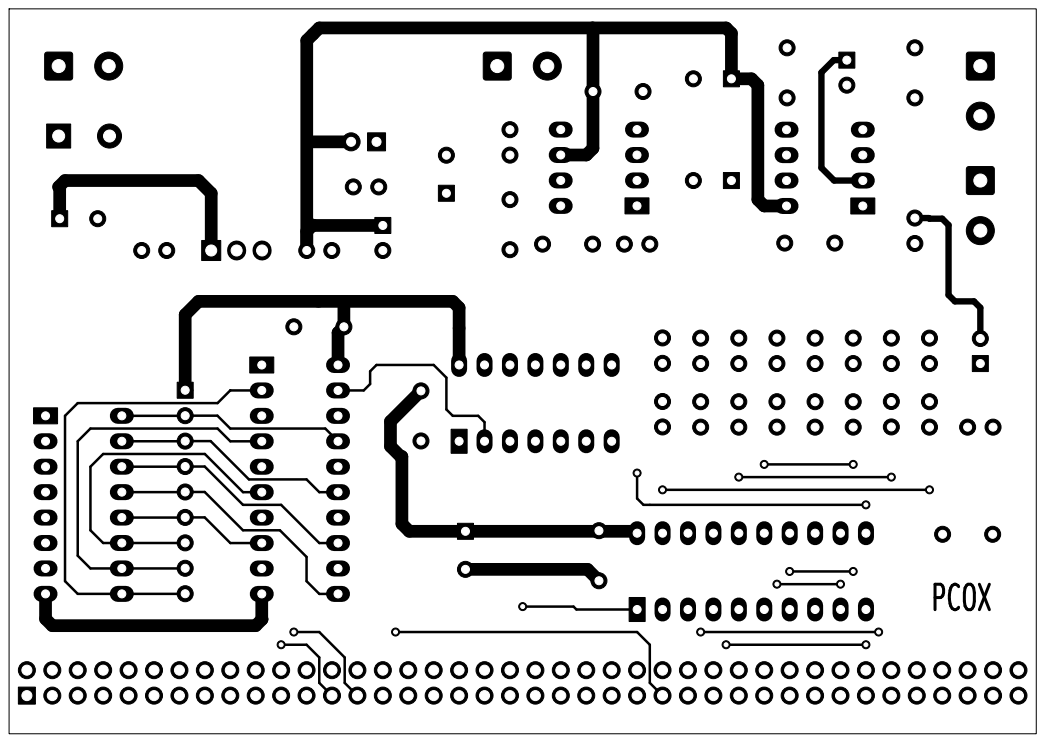
[picture p107: page 1]

Id: 1/2 Title: PCOX - COVOX module
