pozsarzs/zacchaeus/Zacchaeus computer/hardware/PCOX COVOX module/pcox-F_Silkscreen.pdf

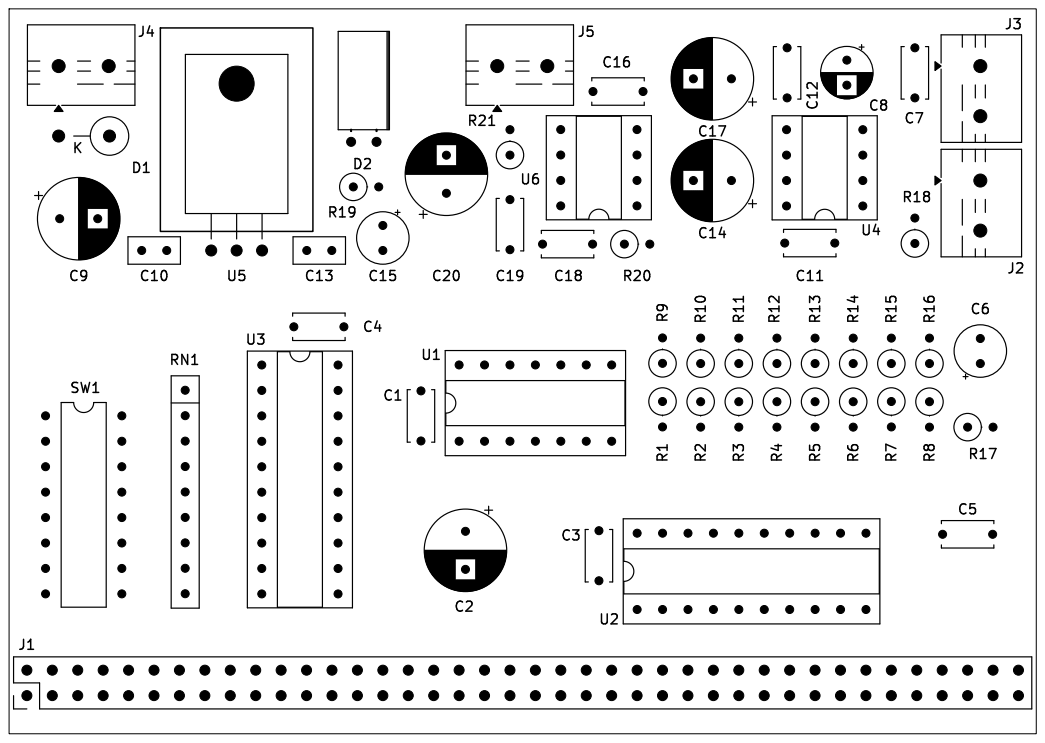
[picture p108: page 1]

Id: 2/2 Title: PCOX - COVOX module
