pozsarzs/zacchaeus/Zacchaeus computer/hardware/PCOX COVOX module/pcox.pdf

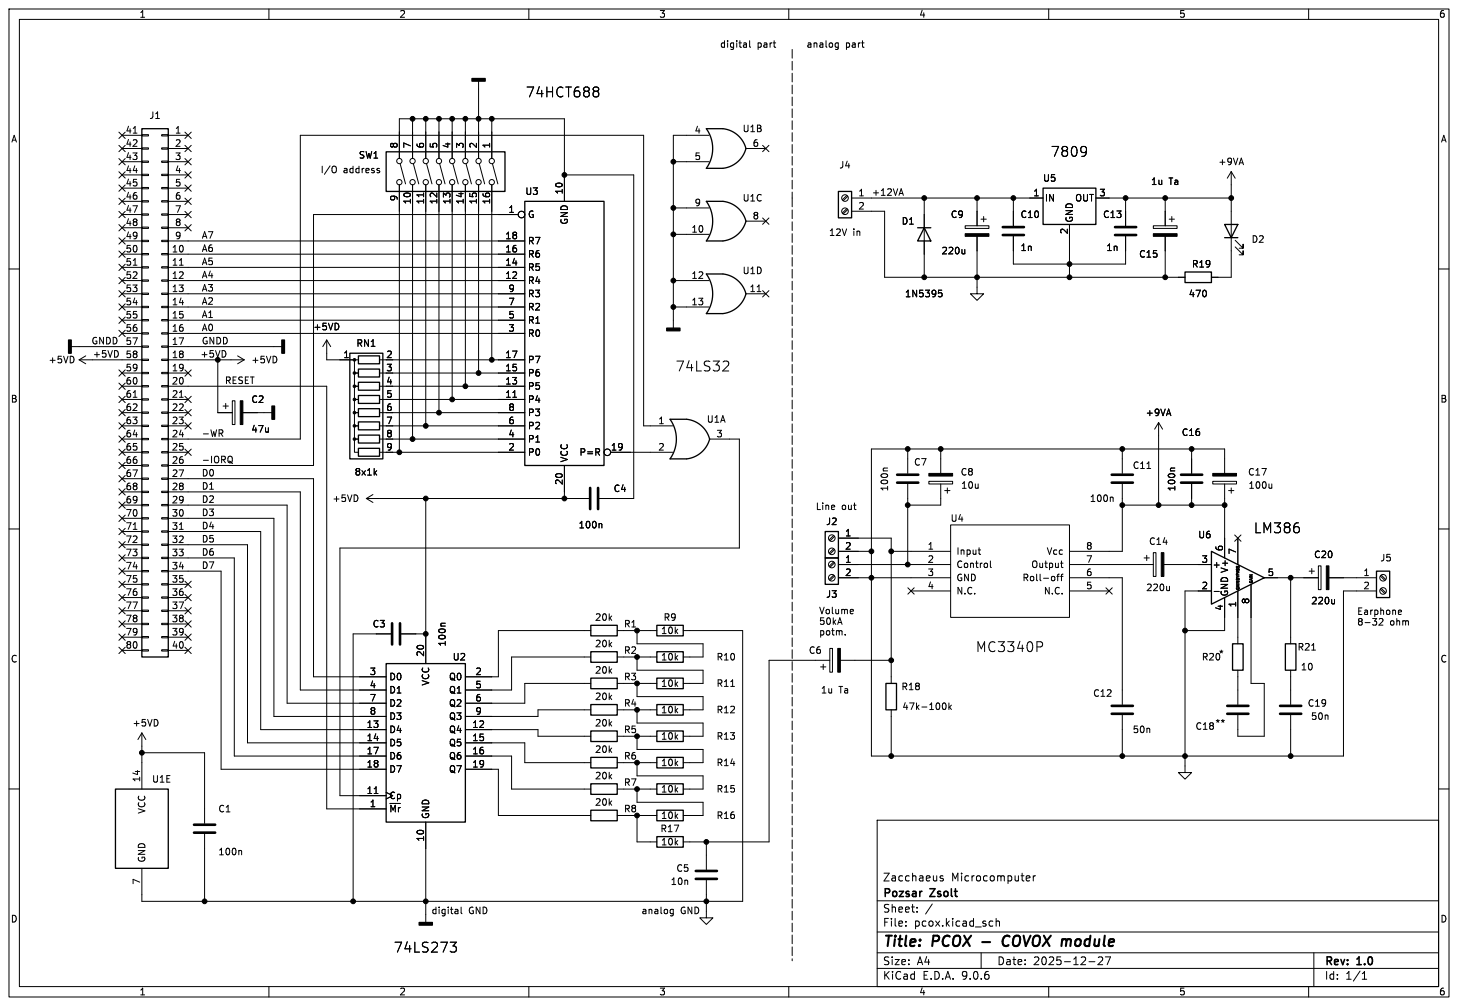
[picture p109: page 1]

Id: 1/1 Title: PCOX - COVOX module
