pozsarzs/zacchaeus/Zacchaeus computer/hardware/PIOI IO Interface module/pioi-B_Cu.pdf

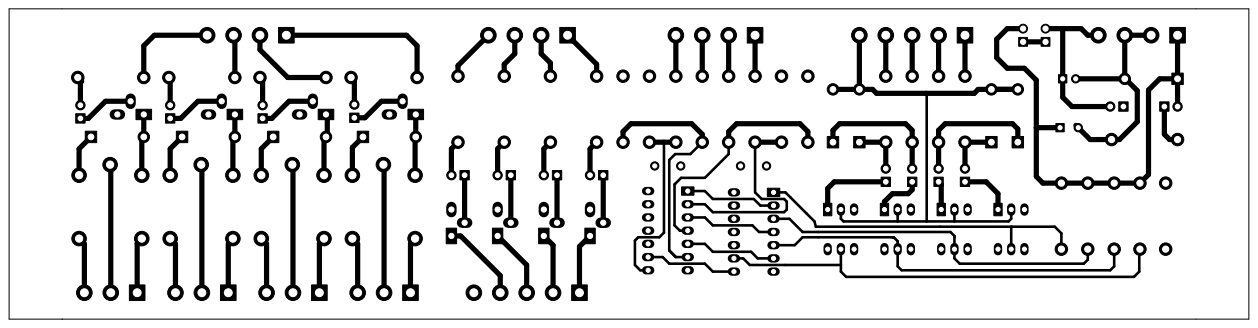
[picture p110: page 1]

Id: 1/1 Title: PIOI I/O interface module
