pozsarzs/zacchaeus/Zacchaeus computer/hardware/PIOI IO Interface module/pioi-F_Cu.pdf

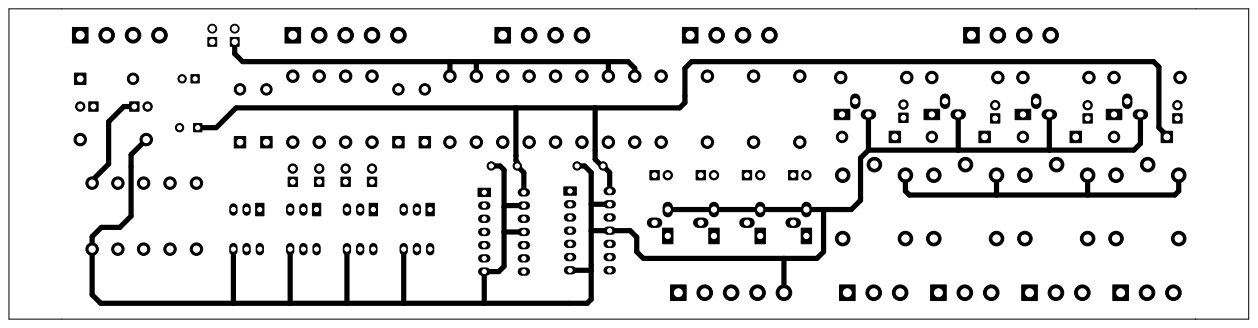
[picture p111: page 1]

Id: 1/1 Title: PIOI I/O interface module
