pozsarzs/zacchaeus/Zacchaeus computer/hardware/PIOI IO Interface module/pioi.pdf

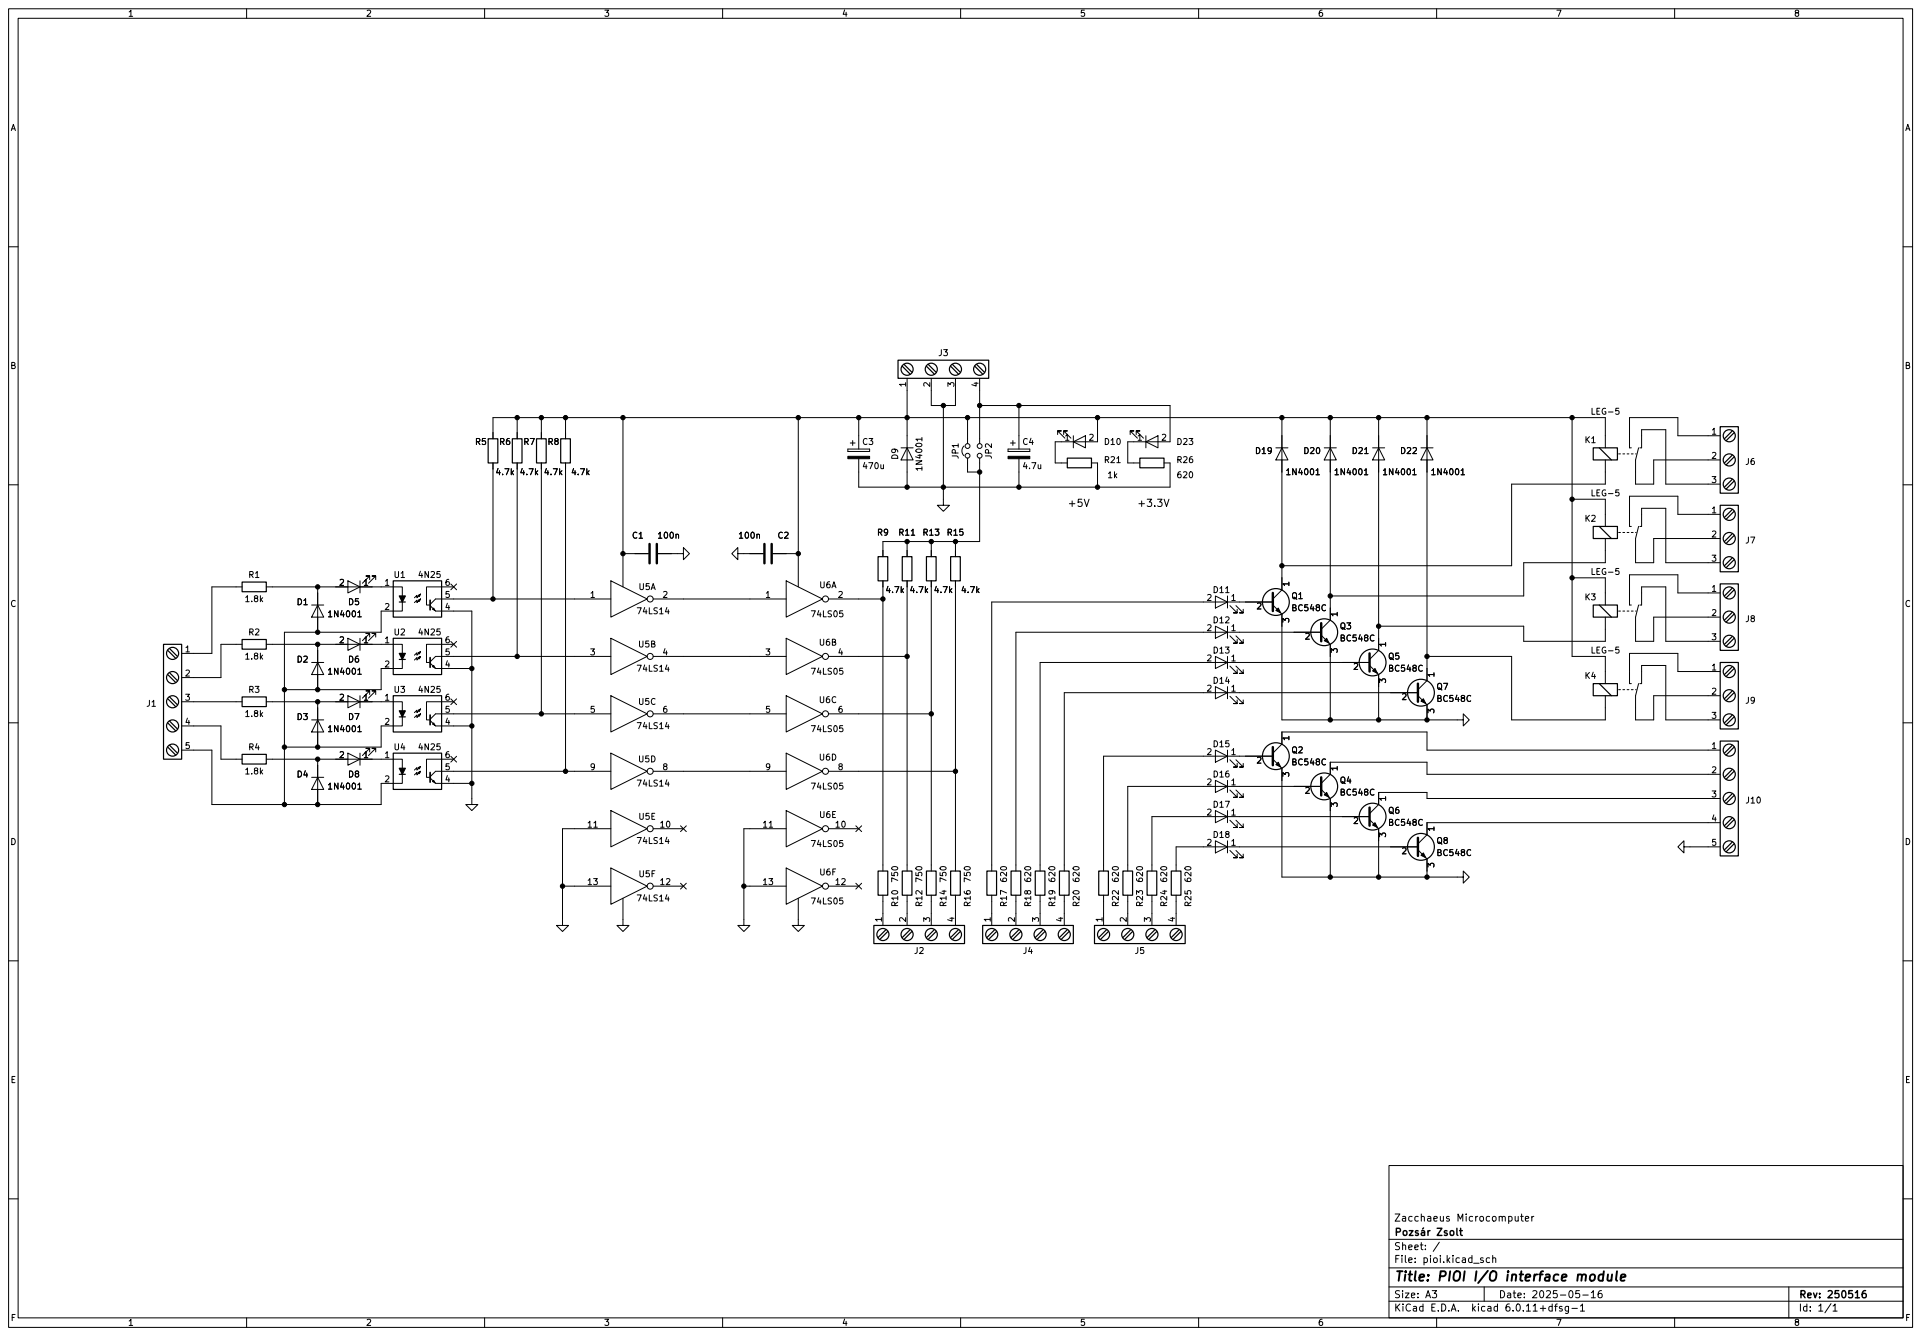
[picture p113: page 1]

Id: 1/1 Title: PIOI I/O interface module
