pozsarzs/zacchaeus/Zacchaeus computer/hardware/PMAN-DP Display module/pman-dp-B_Cu.pdf

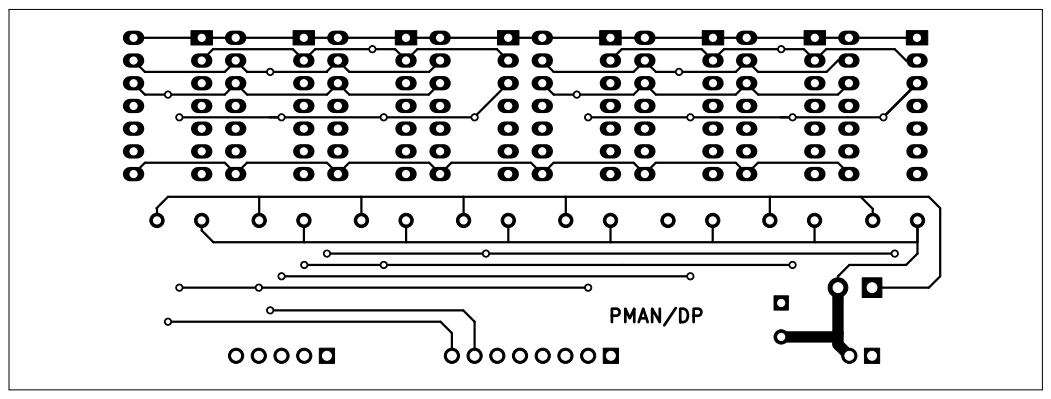
[picture p114: page 1]

Id: 1/1 Title: PMAN/DP - display module
