pozsarzs/zacchaeus/Zacchaeus computer/hardware/PMAN-DP Display module/pman-dp-F_Cu.pdf

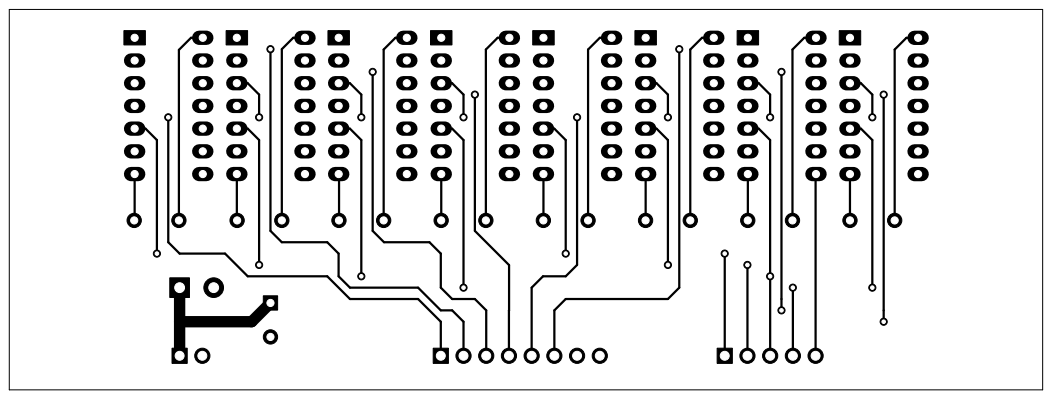
[picture p115: page 1]

Id: 1/1 Title: PMAN/DP - display module
