pozsarzs/zacchaeus/Zacchaeus computer/hardware/PMAN-DP Display module/pman-dp-F_Silkscreen.pdf

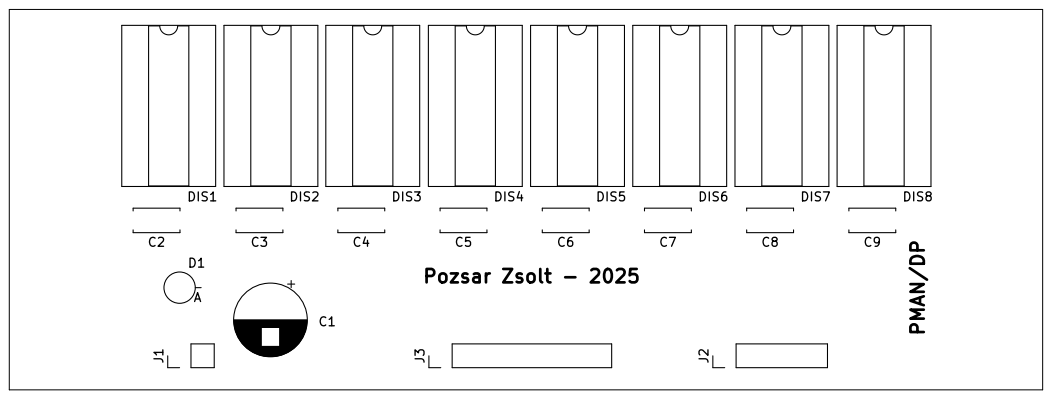
[picture p116: page 1]

Id: 1/1 Title: PMAN/DP - display module
