pozsarzs/zacchaeus/Zacchaeus computer/hardware/PMAN-DP Display module/pman-dp.pdf

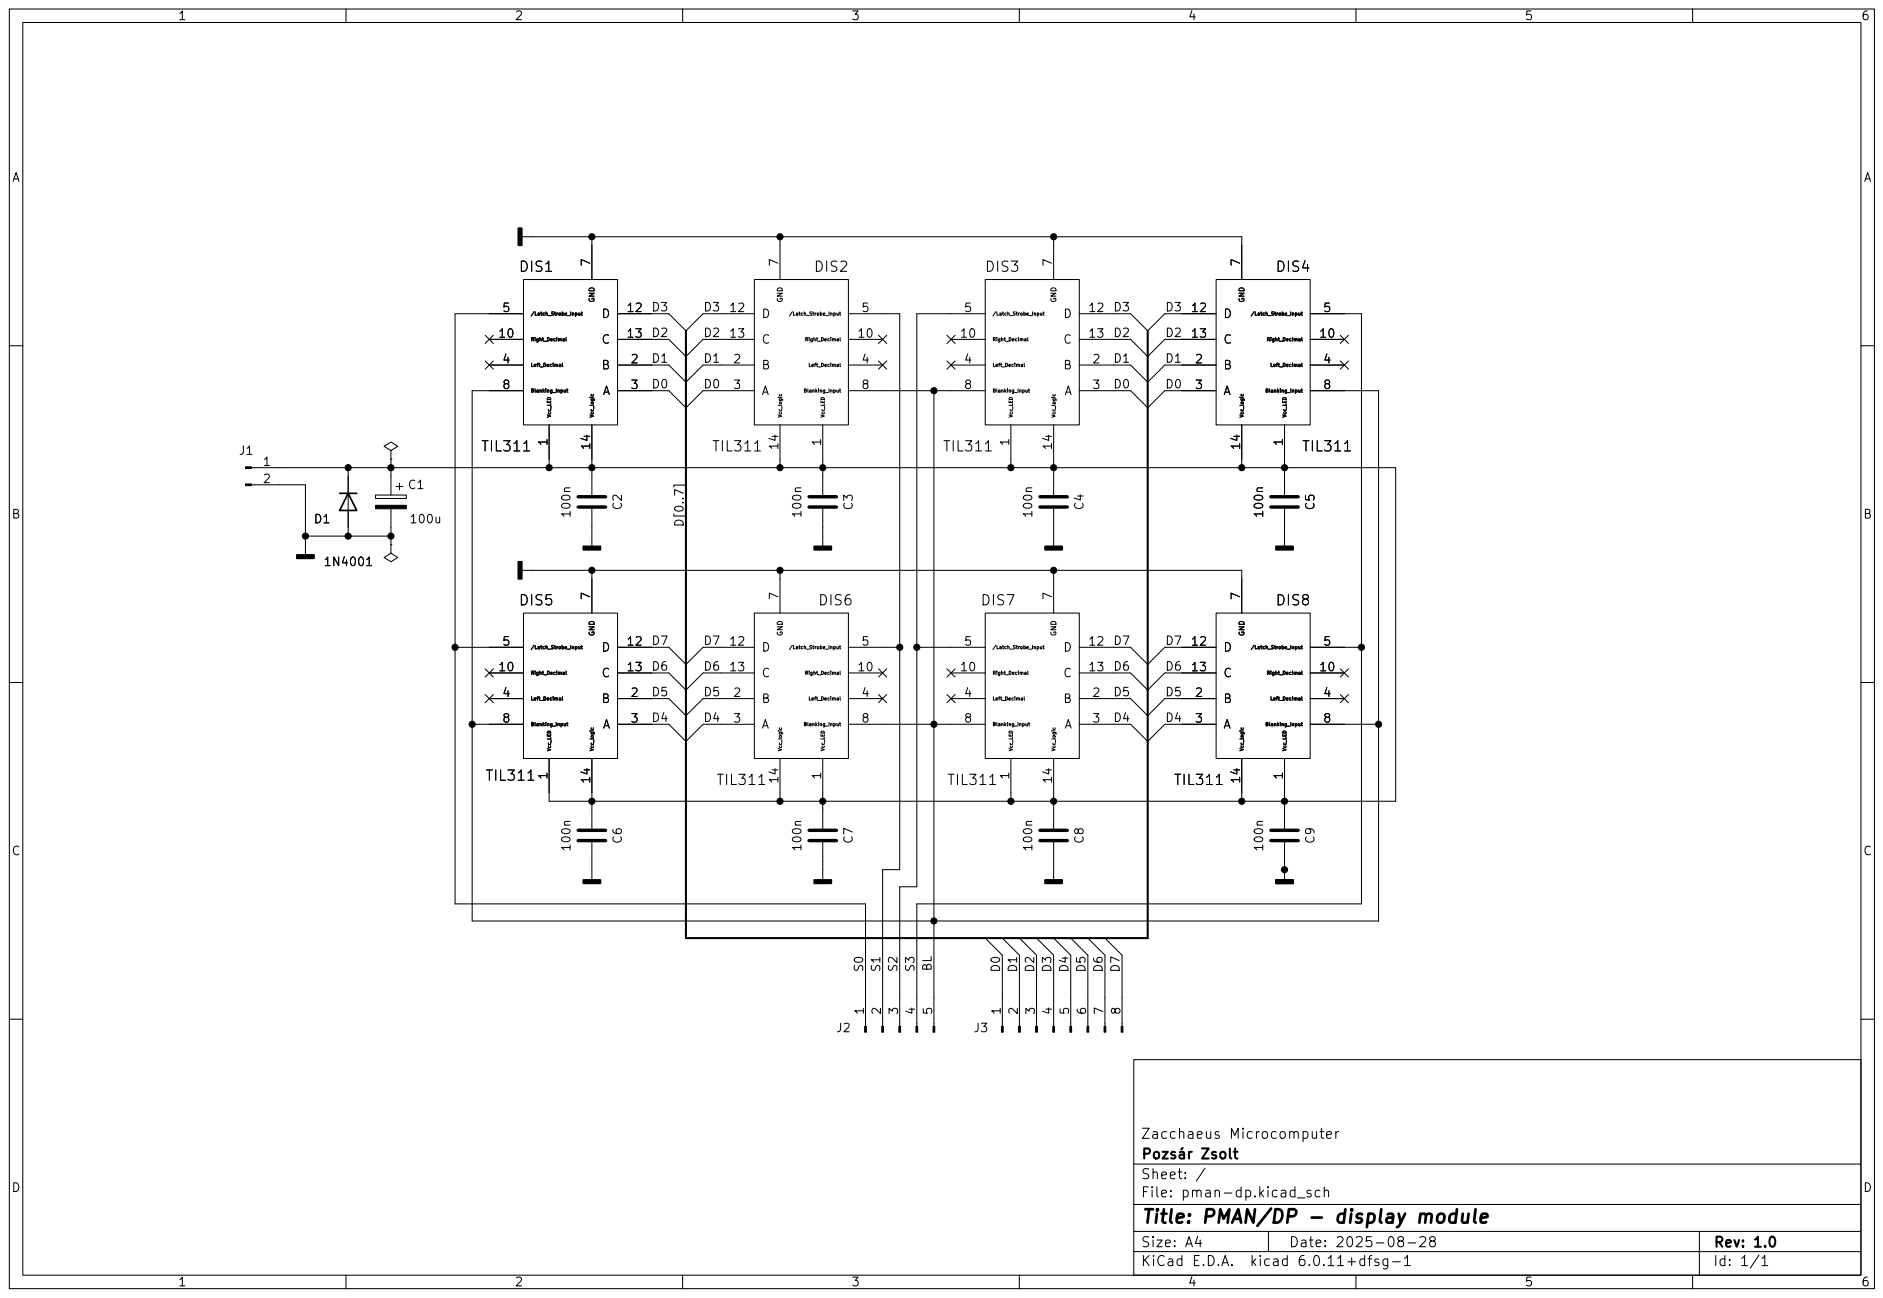
[picture p117: page 1]

Id: 1/1 Title: PMAN/DP - display module
