pozsarzs/zacchaeus/Zacchaeus computer/hardware/PMAN-SW Switch module/pman-sw.pdf

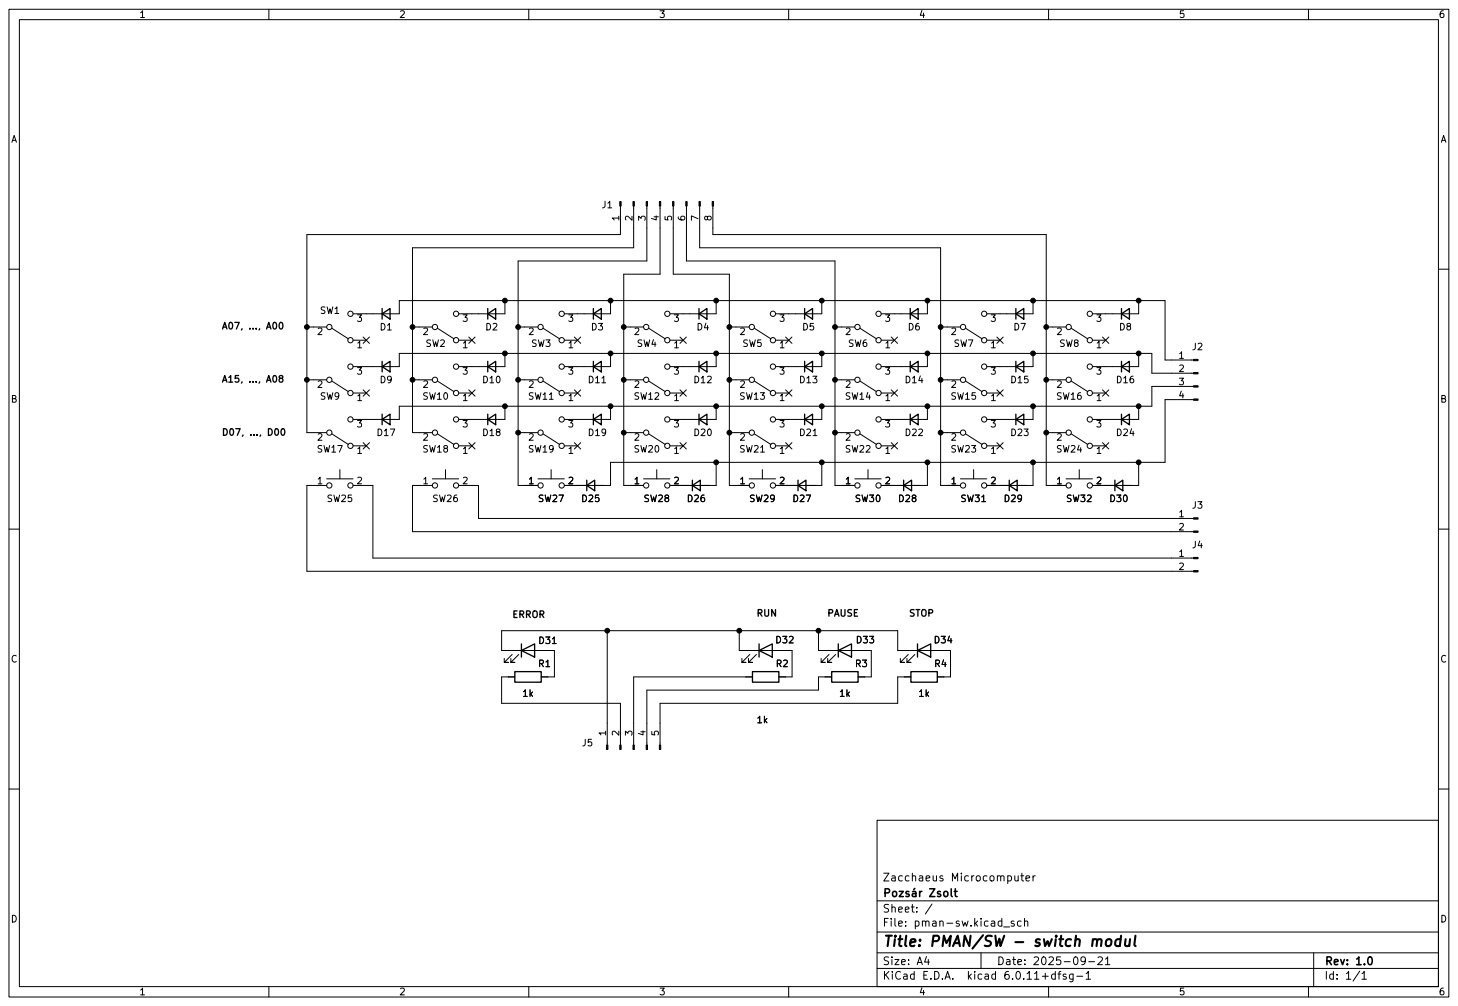
[picture p118: page 1]
