pozsarzs/zacchaeus/Zacchaeus computer/hardware/PPOW Power distribution module/ppow-B_Cu.pdf

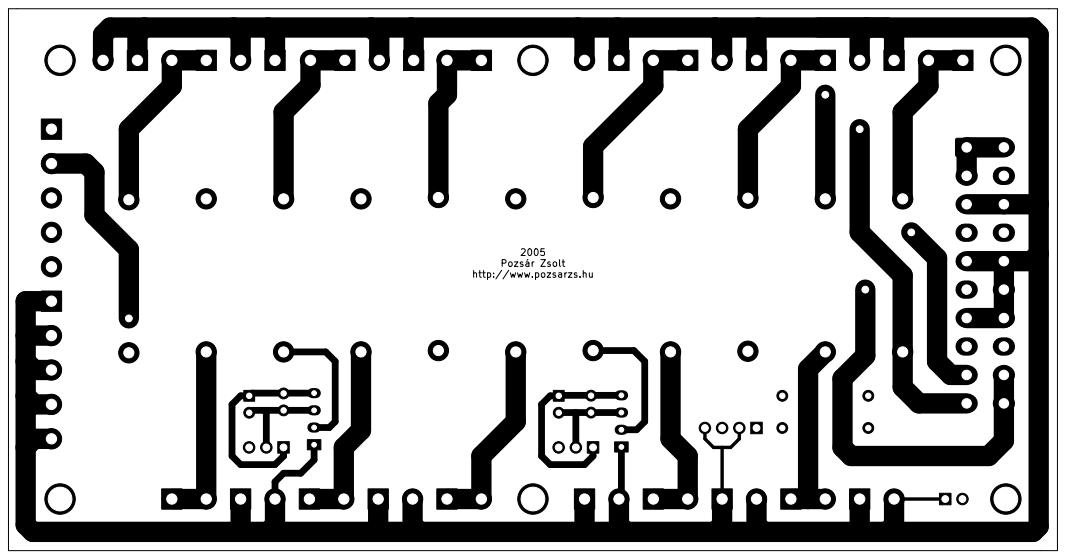
[picture p119: page 1]

2005 þÿPozsár Zsolt http://www.pozsarzs.hu
