pozsarzs/zacchaeus/Zacchaeus computer/hardware/PPOW Power distribution module/ppow-F_Cu.pdf

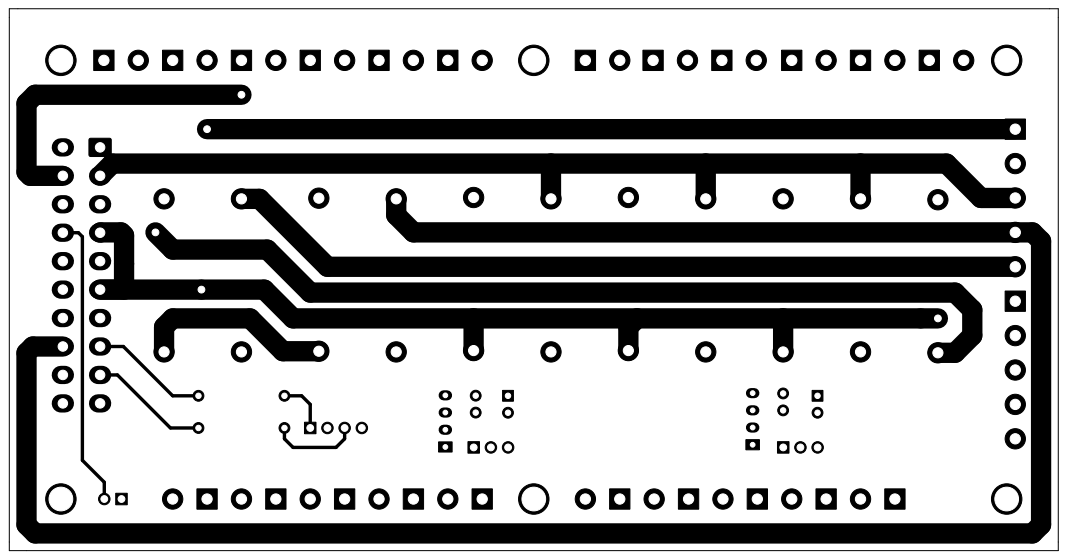
[picture p120: page 1]
