pozsarzs/zacchaeus/Zacchaeus computer/hardware/PPOW Power distribution module/ppow-F_Silkscreen.pdf

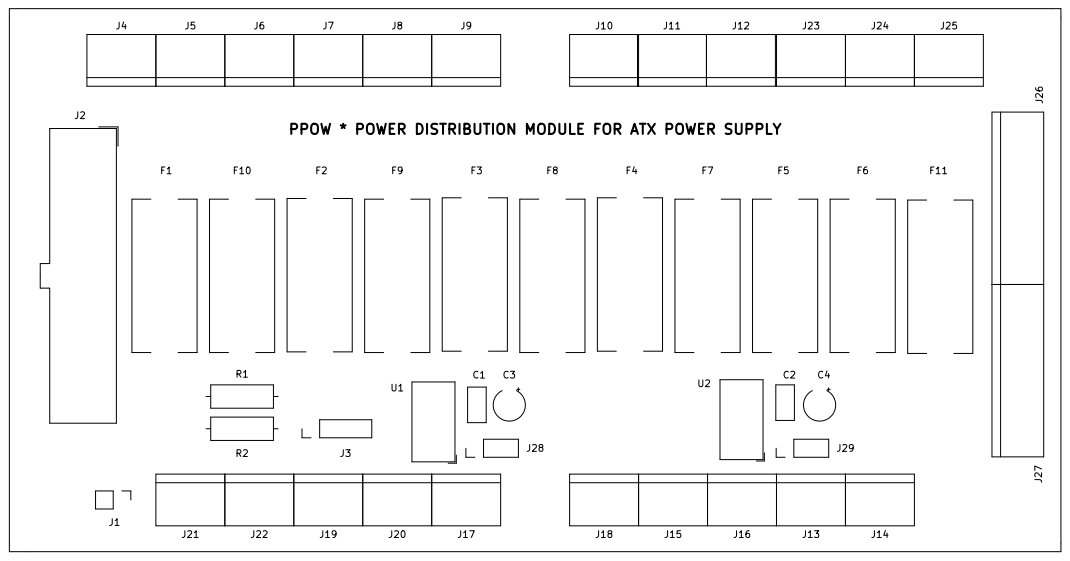
[picture p121: page 1]
