pozsarzs/zacchaeus/Zacchaeus computer/hardware/PSPK Speaker amplifier module/pspk-B_Cu.pdf

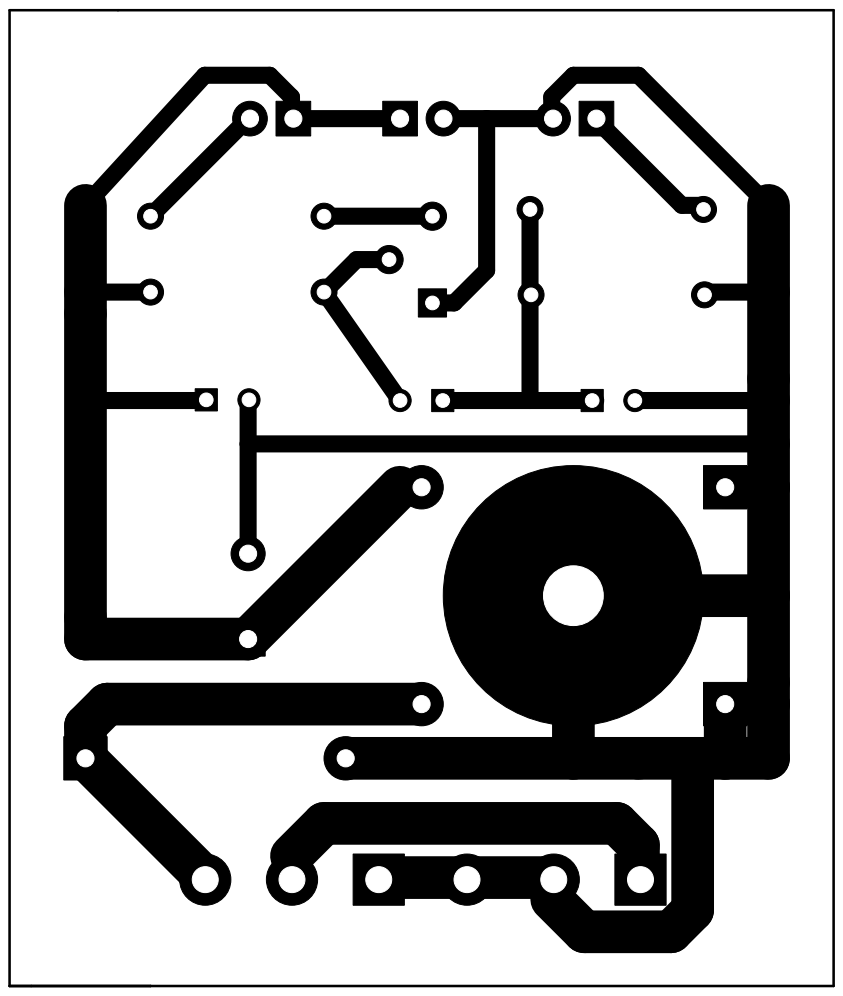
[picture p122: page 1]

Id: 1/1 Title: PSPK Speaker amplifier module
