pozsarzs/zacchaeus/Zacchaeus computer/hardware/PSPK Speaker amplifier module/pspk-F_Silkscreen.pdf

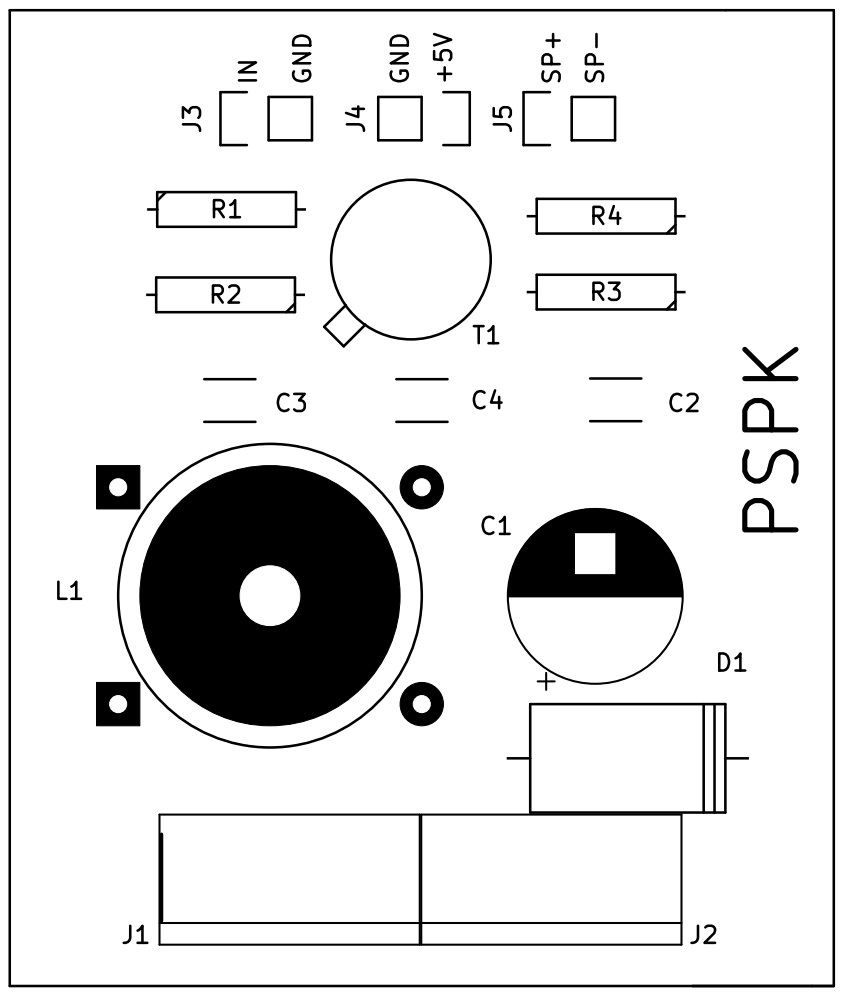
[picture p123: page 1]

Id: 1/1 Title: PSPK Speaker amplifier module
