pozsarzs/zacchaeus/Zacchaeus computer/hardware/PSPK Speaker amplifier module/pspk.pdf

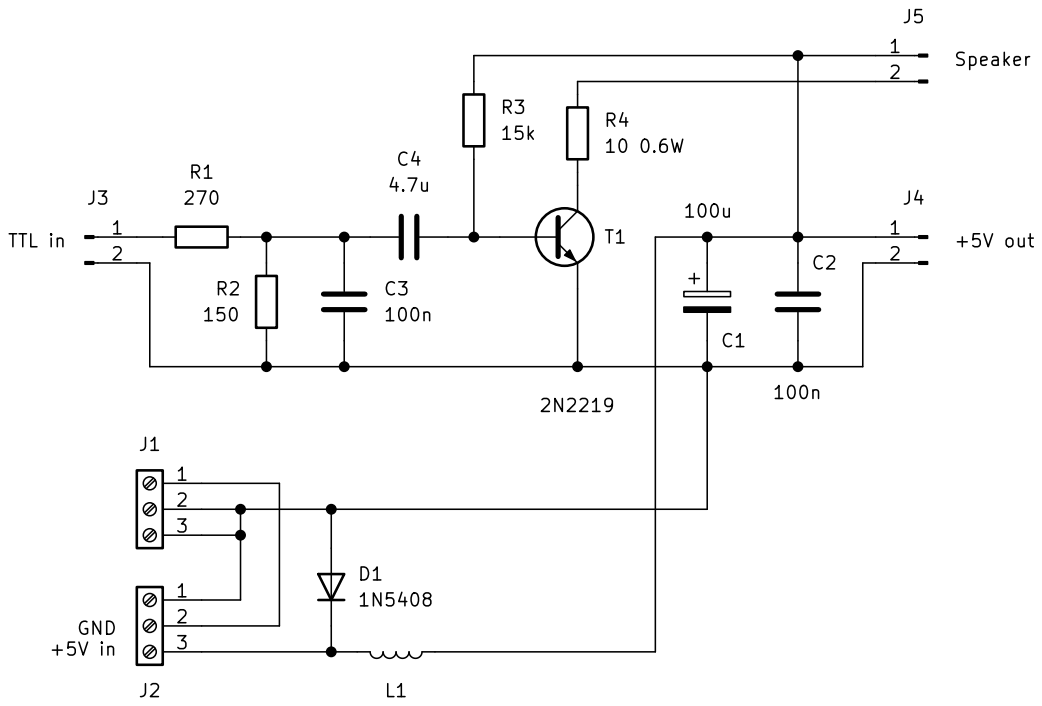
[picture p124: page 1]

Id: 1/1 Title: PSPK Speaker amplifier module
