pozsarzs/zacchaeus/Zacchaeus computer/hardware/SC702 RCBus backplane/SC702 schematic.pdf

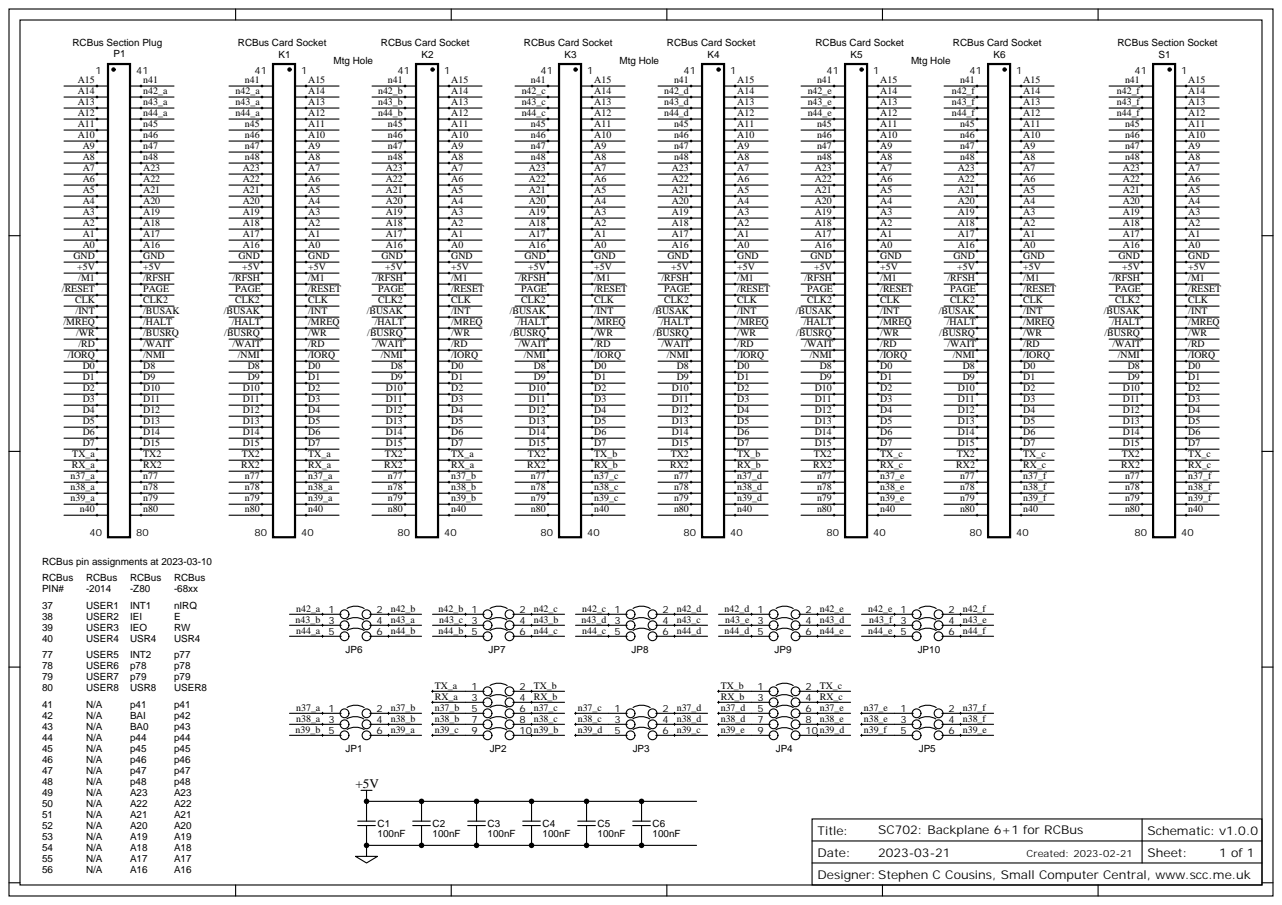
[picture p125: page 1]

Stephen C Cousins, Small Computer Central, www.scc.me.uk
