pozsarzs/zacchaeus/Zacchaeus computer/hardware/SC715 RCBus CF module/SC715 schematic.pdf

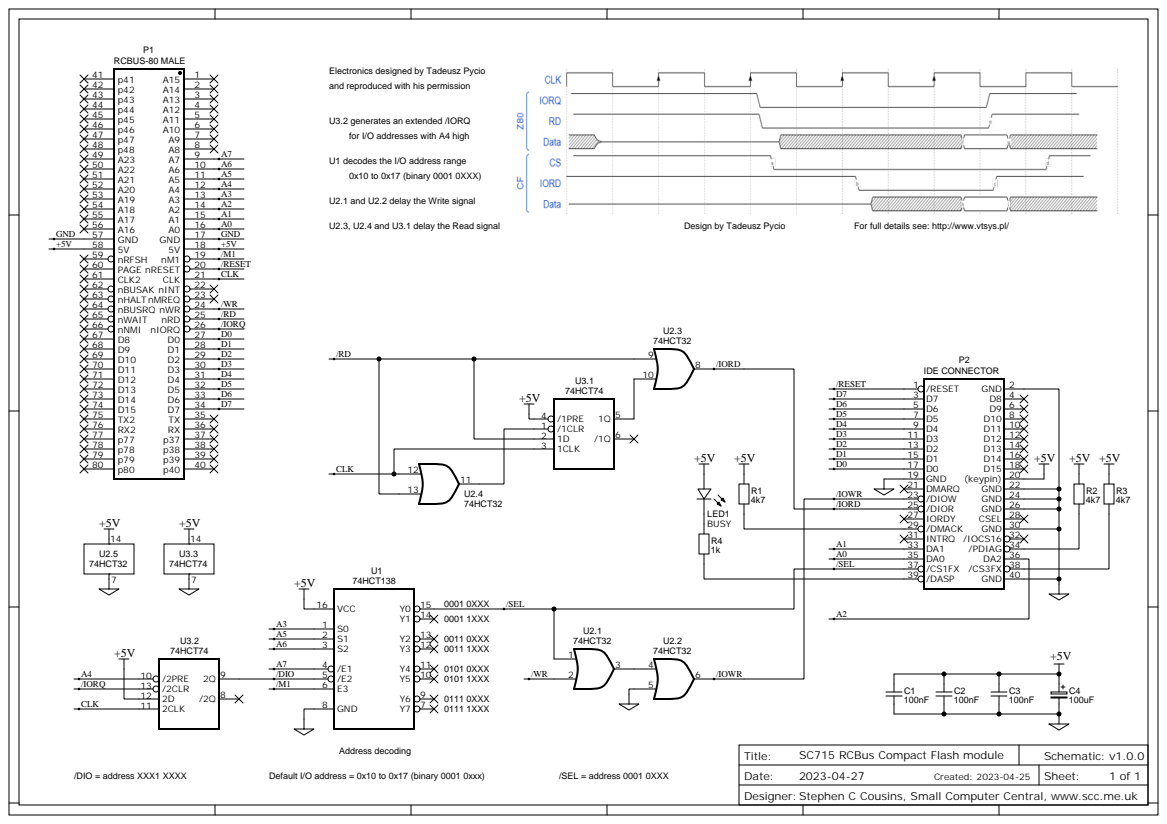
[picture p126: page 1]

Electronics designed by Tadeusz Pycio
and reproduced with his permission

U3.2 generates an extended /IORQ
for I/O addresses with A4 high

U1 decodes the I/O address range
0x10 to 0x17 (binary 0001 0XXX)

U2.1 and U2.2 delay the Write signal

Default I/O address = 0x10 to 0x17 (binary 0001 0xxx)

Stephen C Cousins, Small Computer Central, www.scc.me.uk
