pozsarzs/zacchaeus/Zacchaeus computer/hardware/SC716 RCBus SIO-2 module/SC716 schematic.pdf

## Address decoding

## SIO/2

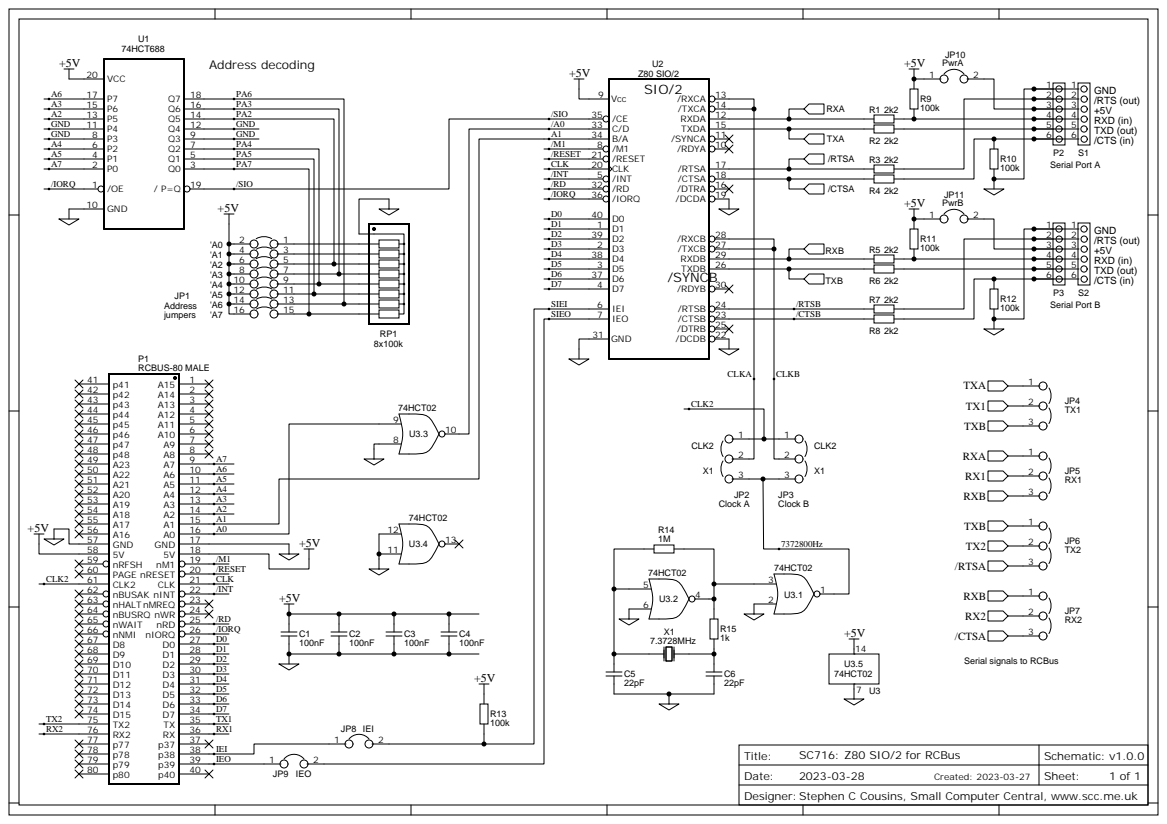
[picture p127: page 1]

Serial signals to RCBus

Stephen C Cousins, Small Computer Central, www.scc.me.uk
