pozsarzs/zacchaeus/Zacchaeus computer/hardware/SC717 RCBus PIO module/SC717 schematic.pdf

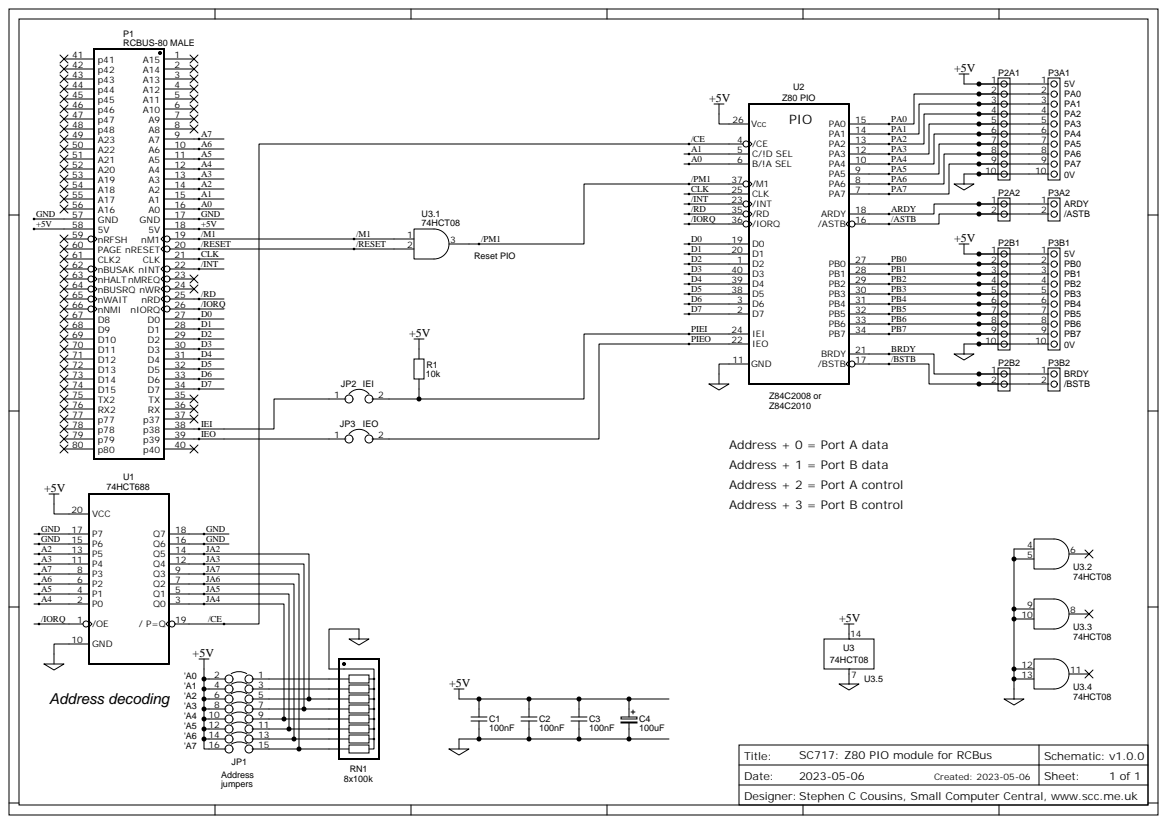
[picture p128: page 1]

Stephen C Cousins, Small Computer Central, www.scc.me.uk
