pozsarzs/zacchaeus/Zacchaeus computer/hardware/SC718 RCBus CTC module/SC718 schematic.pdf

## Address decoding

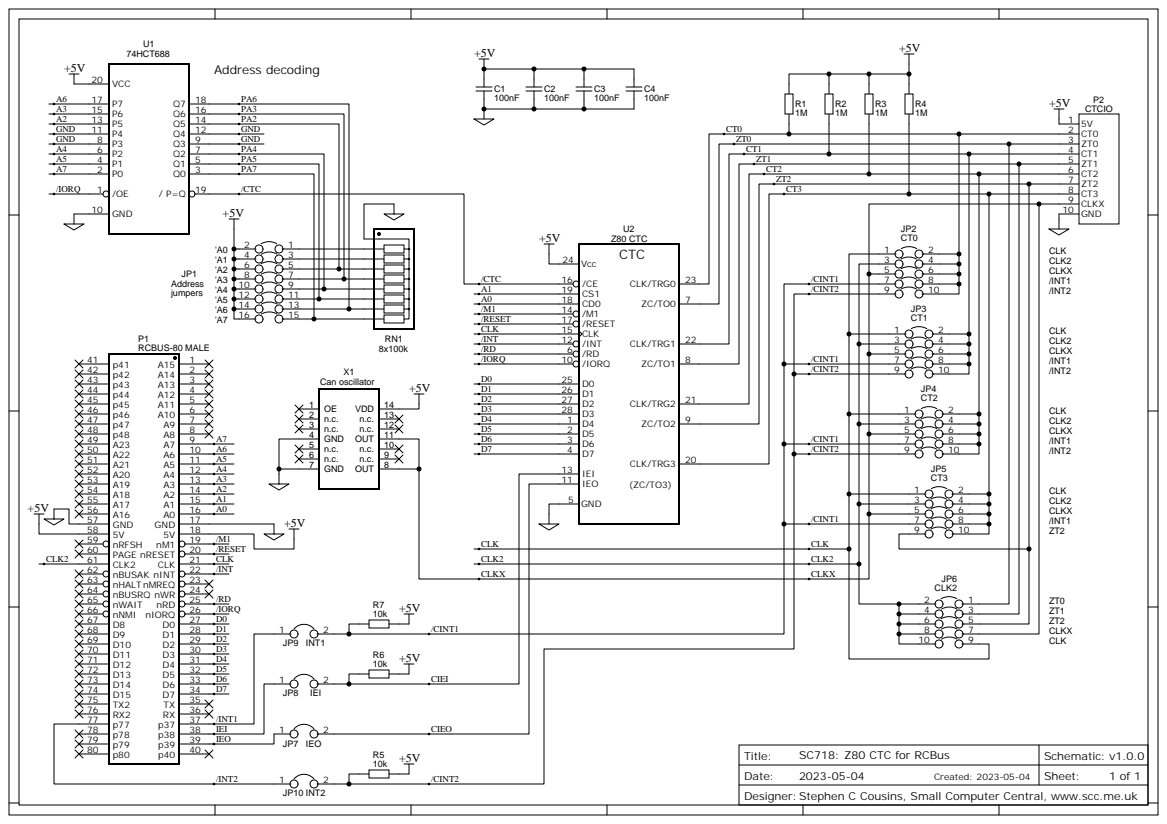
[picture p129: page 1]

Stephen C Cousins, Small Computer Central, www.scc.me.uk
