pozsarzs/zacchaeus/Zacchaeus computer/hardware/SC719 RCBus DIO module/SC719 schematic.pdf

20 | 19 OUTPUT | INPUT
Q0 18 | Q1 17 | Q2 16 | Q3 15 | Q4 14 | Q5 13 | Q6 12 | Q7 11

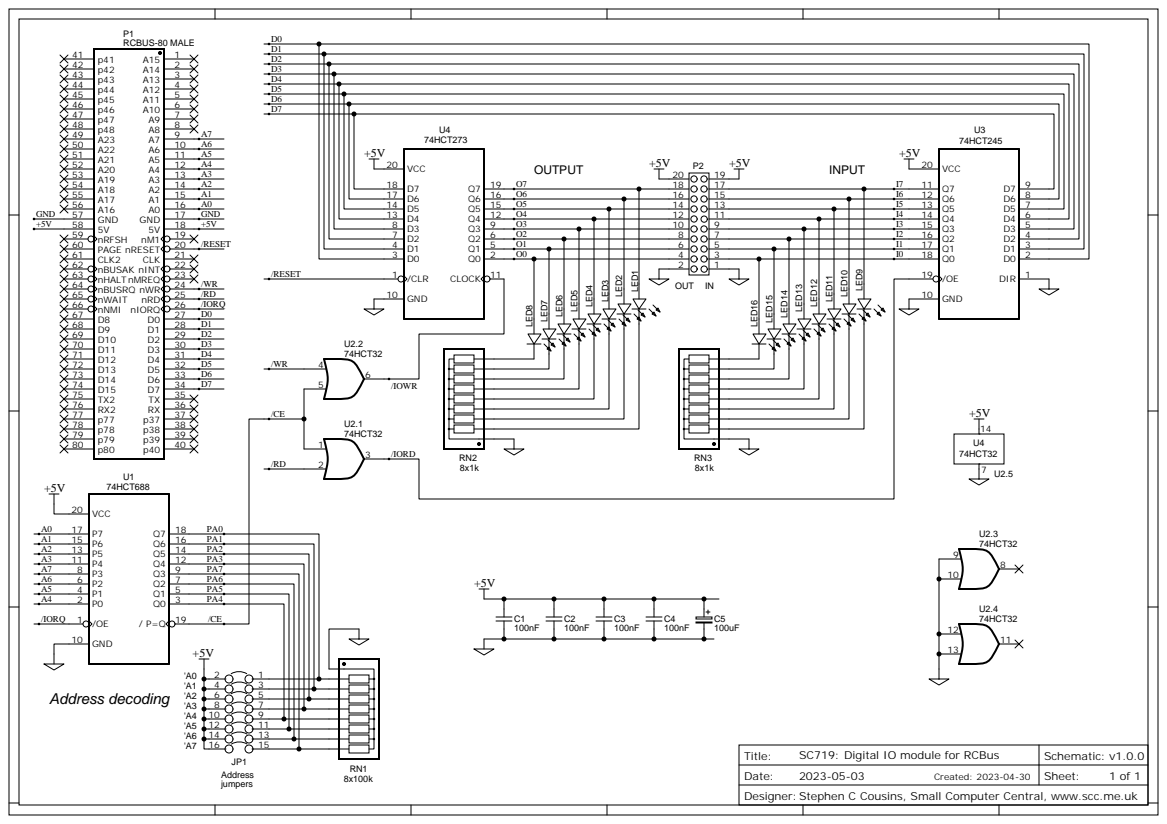
[picture p130: page 1]

Stephen C Cousins, Small Computer Central, www.scc.me.uk
